hbitter/DNMS/Firmware/Teensy/Teensy3.6/V2/README.md

# [English text below](#teensy36-dnms-firmware)

## Teensy3.6 DNMS Firmware

### Versions Historie:

 - DNMS_V2.5.0 - Korrektur Fehler bei der Initialisierung
 - DNMS_V2.5.1 - Korrektur Fehler bei der Initialisierung<br><br>

------------------------------------------------------------------------
## Teensy3.6 DNMS Firmware

### Version history:

 - DNMS_V2.5.0 - Correction of a bug at startup
 - DNMS_V2.5.1 - Correction of a bug at startup<br><br>
