hbitter/DNMS/Firmware/Teensy/Teensy4.0/V2/README.md

# [English text below](#dnms-firmware-teensy40-v2-english)

# DNMS Firmware Teensy4.0 V2

## Diese Versionen berechnen LAeq, LAmin und LAmax

### aktuelle Versionen:

- DNMS_V2.4.4 - ohne USB-Audio Ausgabe
- DNMS_V2.4.5 - mit USB-Audio Ausgabe

------------------------------------------------------------------------

# DNMS Firmware Teensy4.0 V2 English

## This version calculates LAeq, LAmin and LAmax

### current versions:

- DNMS_V2.4.4 - without USB-Audio output
- DNMS_V2.4.5 - with USB-Audio output
