hbitter/DNMS/Firmware/Teensy4.0/DNMS_Vt.0.4/images/Image 1.jpg

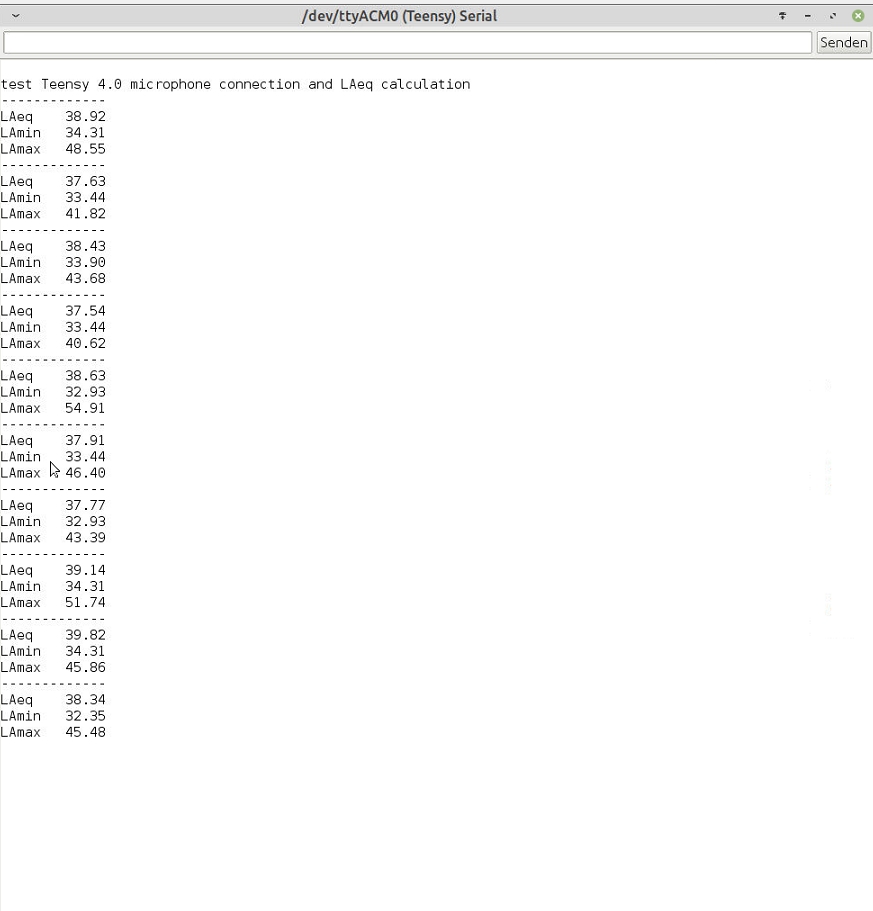
Firmware/Teensy4.0/DNMS_Vt.0.4/images/Image 1.jpg
