hbitter/DNMS/Firmware/Teensy/Teensy3.6/images/Arduino IDE Teensy3.6 USB.jpg

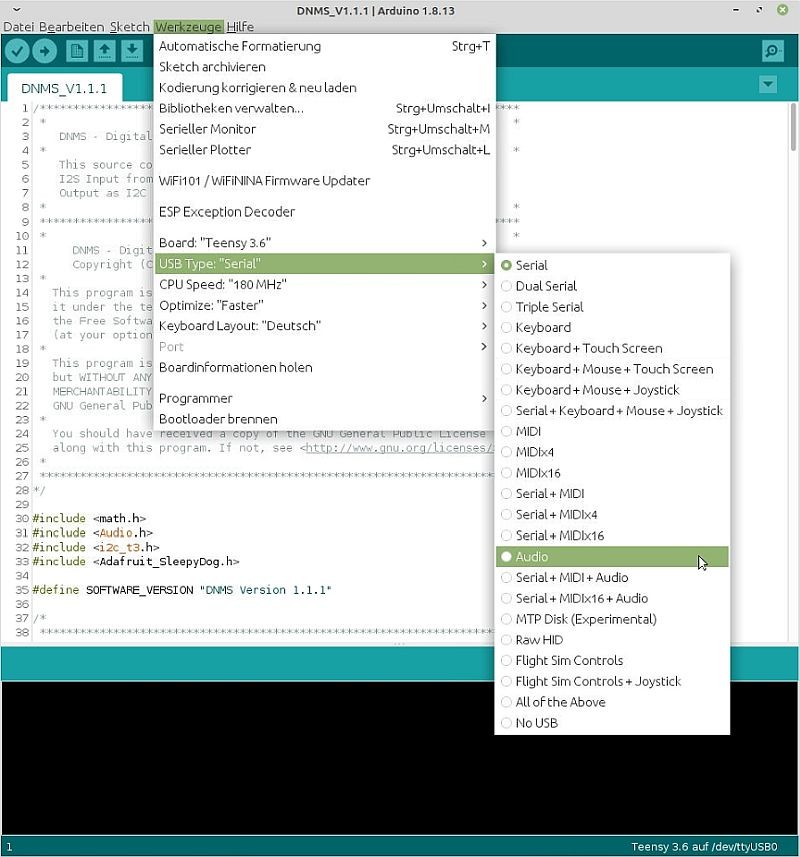
Firmware/Teensy/Teensy3.6/images/Arduino IDE Teensy3.6 USB.jpg
