hbitter/DNMS/PCBs/Airrohr PCB/Airrohr PCB V1.2 KiCad/Airrohr PCB V1.2 Bild 1.jpg

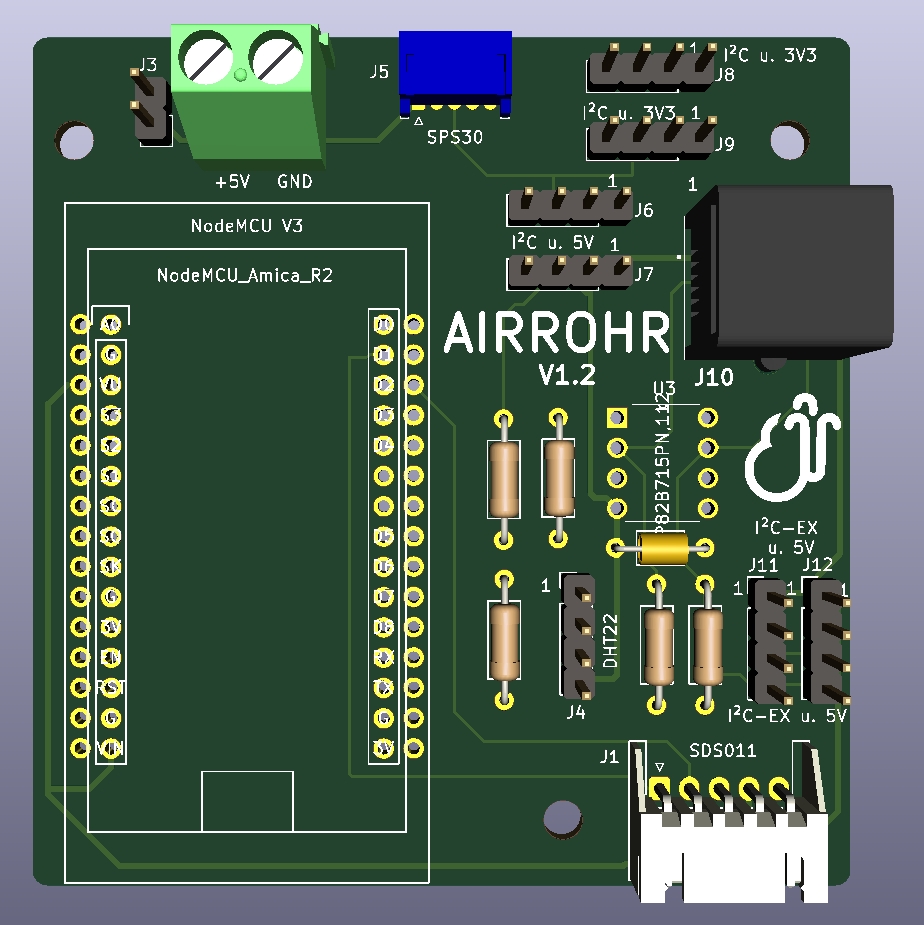
PCBs/Airrohr PCB/Airrohr PCB V1.2 KiCad/Airrohr PCB V1.2 Bild 1.jpg
