hbitter/DNMS/PCBs/Airrohr PCB/Airrohr PCB V1.2 KiCad/Airrohr PCB V1.2 Schaltplan.jpg

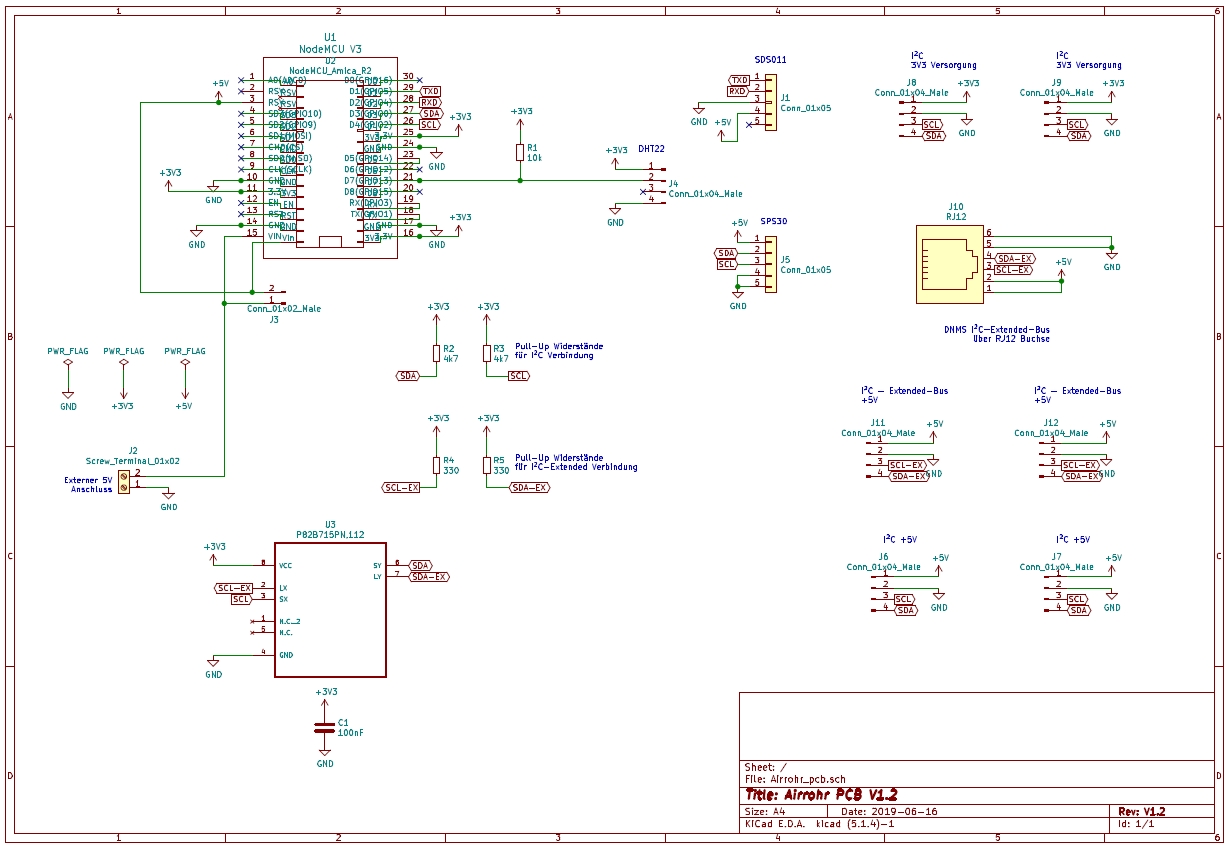
PCBs/Airrohr PCB/Airrohr PCB V1.2 KiCad/Airrohr PCB V1.2 Schaltplan.jpg
