hbitter/DNMS/PCBs/Airrohr-PCB/Airrohr-PCB-V1.6/Bild1.png

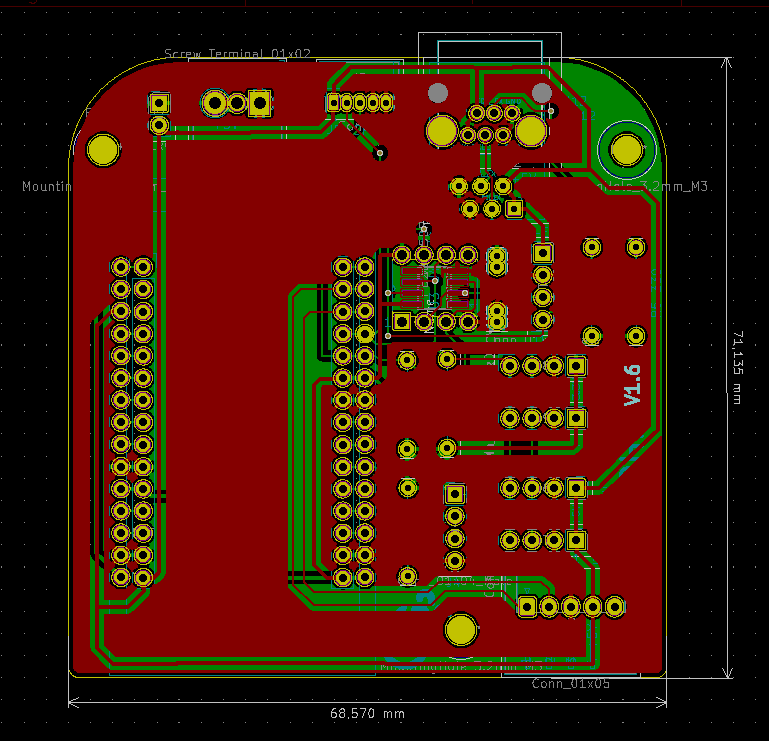
PCBs/Airrohr-PCB/Airrohr-PCB-V1.6/Bild1.png
