hbitter/DNMS/PCBs/Airrohr-PCB/Airrohr-PCB-V1.6/Bild2.png

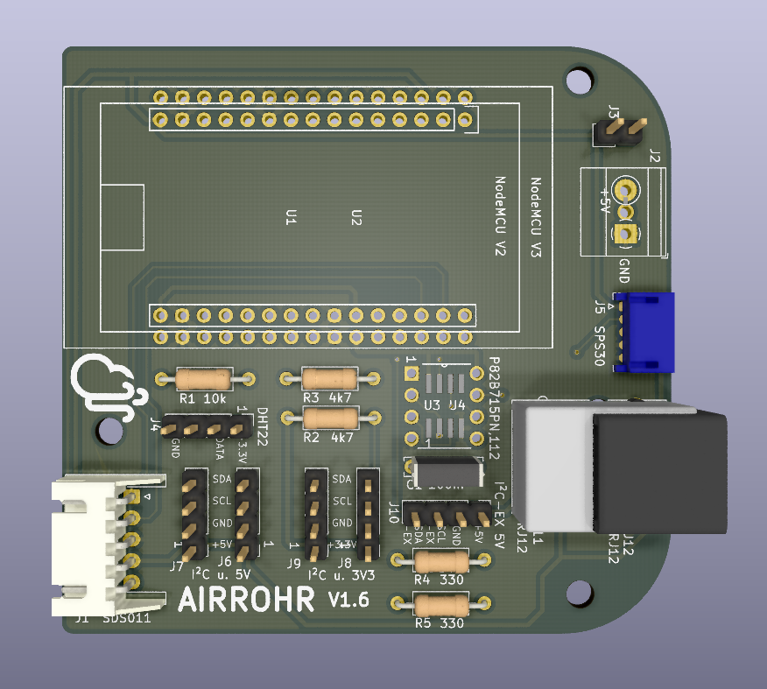
PCBs/Airrohr-PCB/Airrohr-PCB-V1.6/Bild2.png
