hbitter/DNMS/PCBs/Airrohr-PCB/Airrohr-PCB-V1.6/Bild3.png

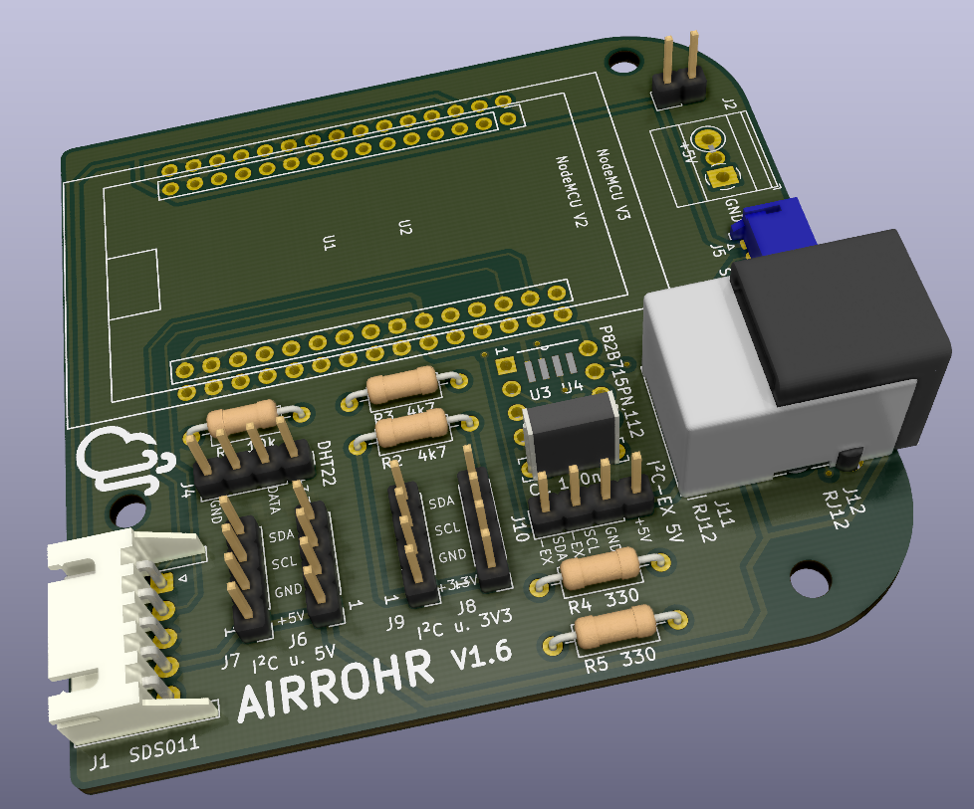
PCBs/Airrohr-PCB/Airrohr-PCB-V1.6/Bild3.png
