hbitter/DNMS/PCBs/DNMS - T3.6/DNMS - T3.6 V1.1/Ansicht PCB 1.jpg

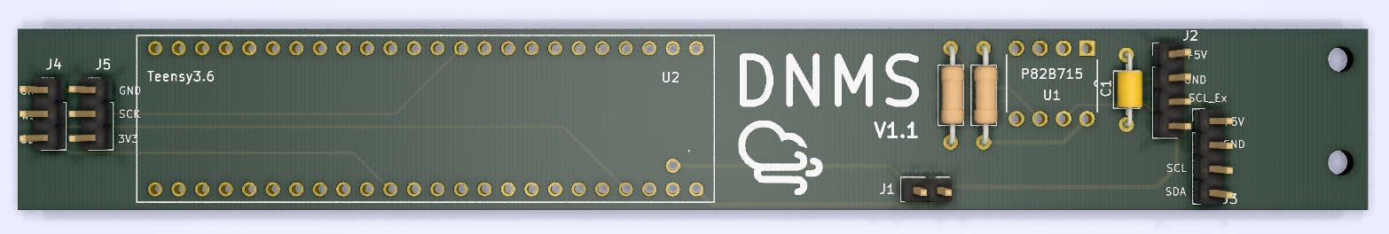
PCBs/DNMS - T3.6/DNMS - T3.6 V1.1/Ansicht PCB 1.jpg
