hbitter/DNMS/PCBs/DNMS - T3.6/DNMS - T3.6 V1.1/Ansicht PCB 2.jpg

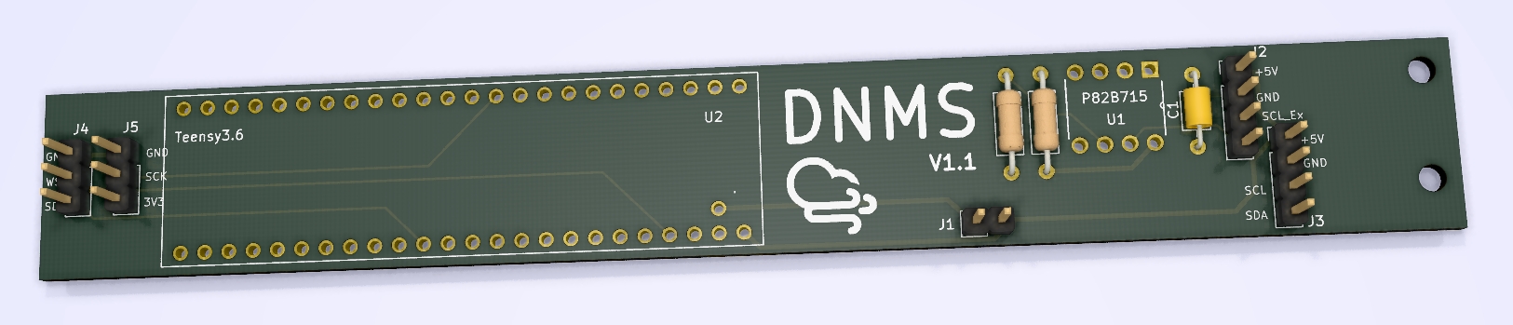
PCBs/DNMS - T3.6/DNMS - T3.6 V1.1/Ansicht PCB 2.jpg
