hbitter/DNMS/PCBs/DNMS - T3.6/DNMS-T3.6-V1.2/DNMS - T3.6 V1.2 Bild 2.jpg

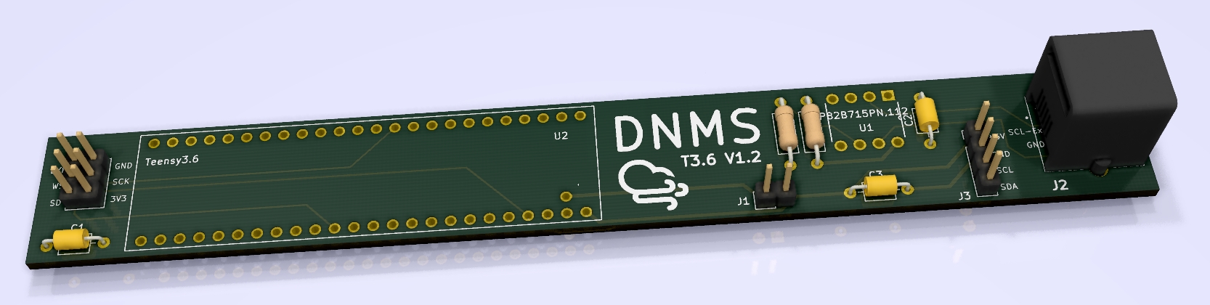
PCBs/DNMS - T3.6/DNMS-T3.6-V1.2/DNMS - T3.6 V1.2 Bild 2.jpg
