hbitter/DNMS/PCBs/DNMS - T4+NodeMCU/DNMS - T4+NodeMCU V1.2/DNMS - T4+NodeMCU V1.2 back 2.jpg

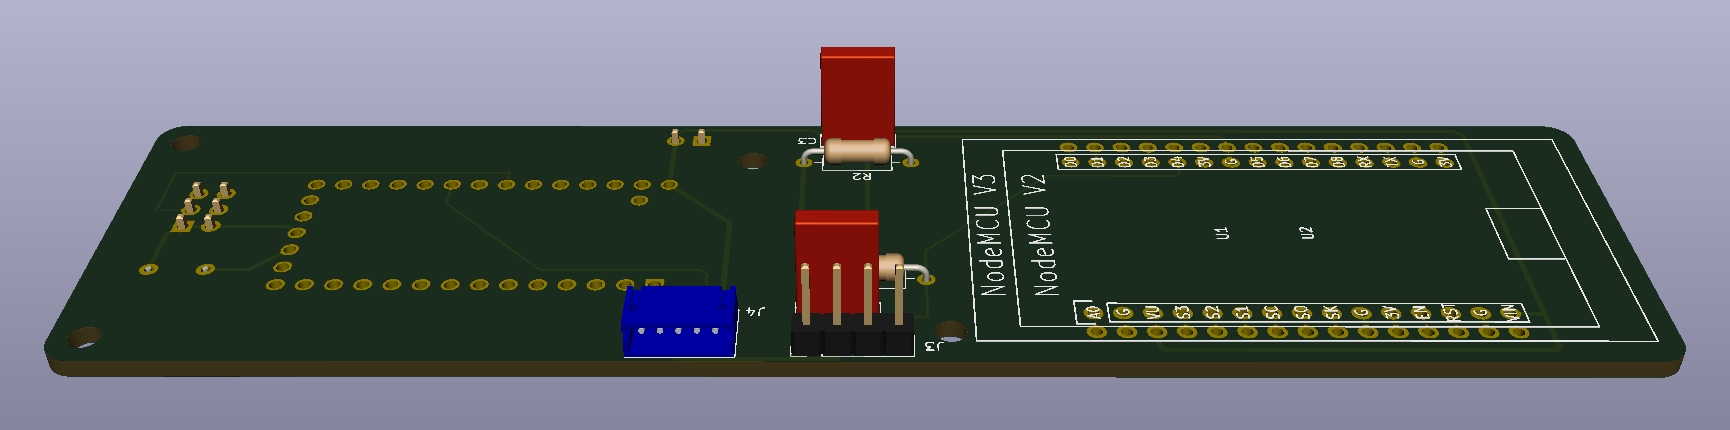
PCBs/DNMS - T4+NodeMCU/DNMS - T4+NodeMCU V1.2/DNMS - T4+NodeMCU V1.2 back 2.jpg
