hbitter/DNMS/PCBs/DNMS - T4/DNMS - T4 V1.2/DNMS - T4 V1.2 Bild 2.jpg

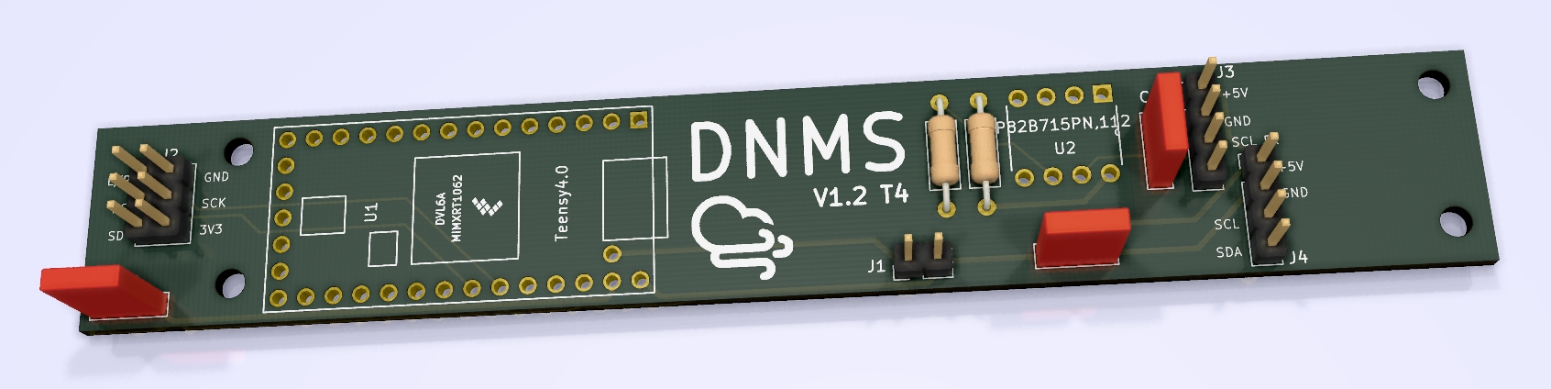
PCBs/DNMS - T4/DNMS - T4 V1.2/DNMS - T4 V1.2 Bild 2.jpg
