hbitter/DNMS/PCBs/DNMS - T4/DNMS - T4 V1.2/DNMS - T4 V1.2 Schaltplan.jpg

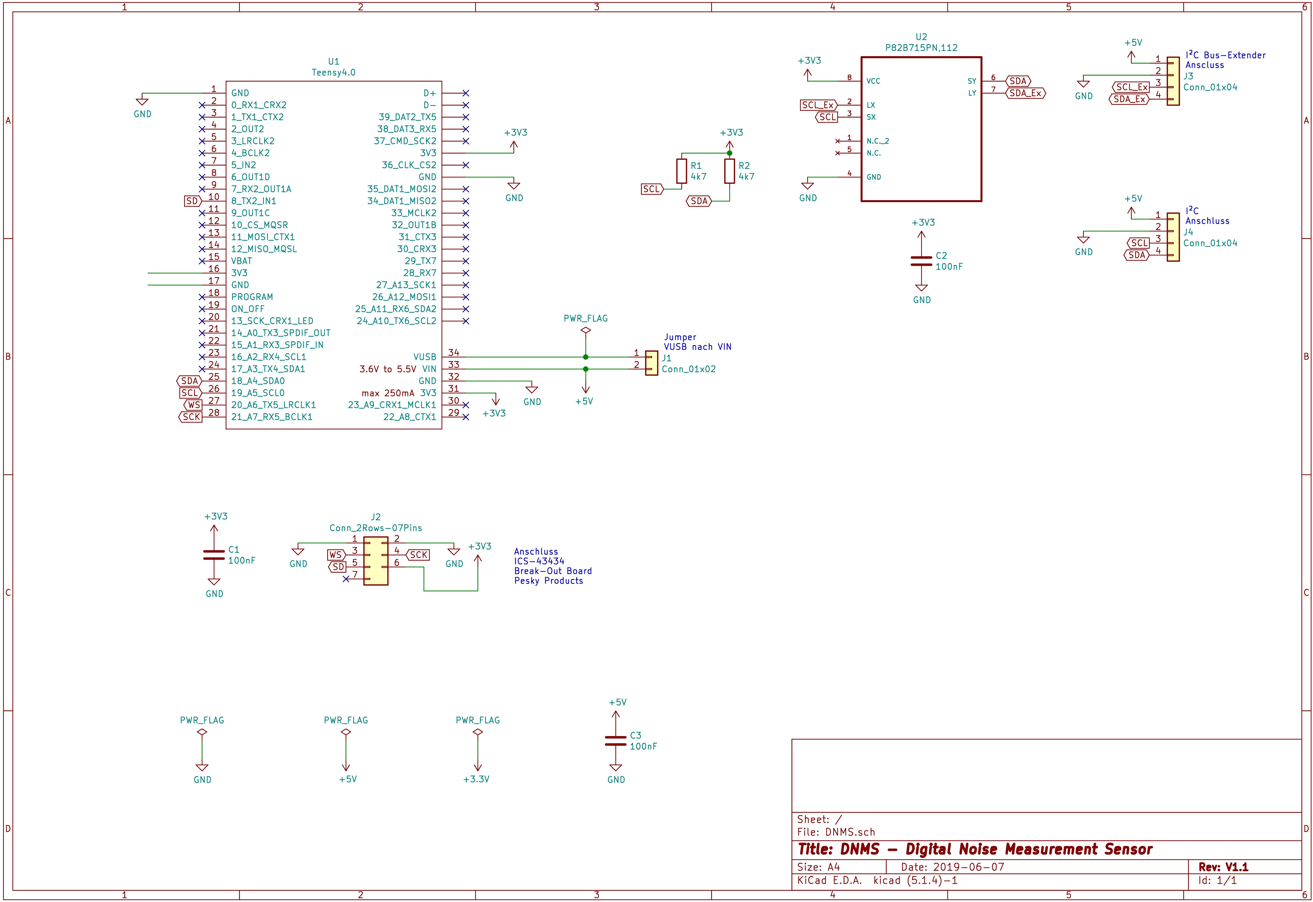
PCBs/DNMS - T4/DNMS - T4 V1.2/DNMS - T4 V1.2 Schaltplan.jpg
