hbitter/DNMS/PCBs/DNMS-RPI-HAT/DNMS-RPI-HAT-V1.0/Bild 1.png

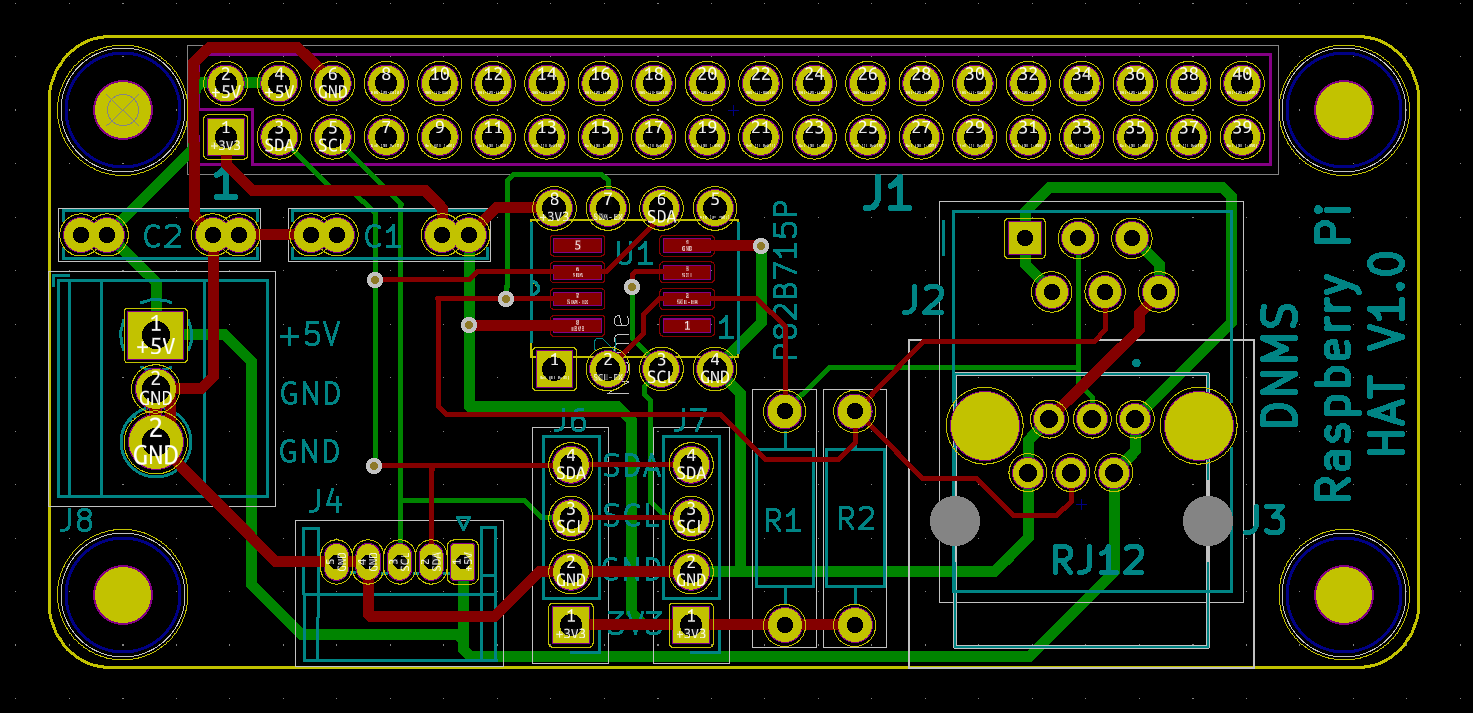
PCBs/DNMS-RPI-HAT/DNMS-RPI-HAT-V1.0/Bild 1.png
