hbitter/DNMS/PCBs/DNMS-RPI-HAT/DNMS-RPI-HAT-V1.0/Bild 4.png

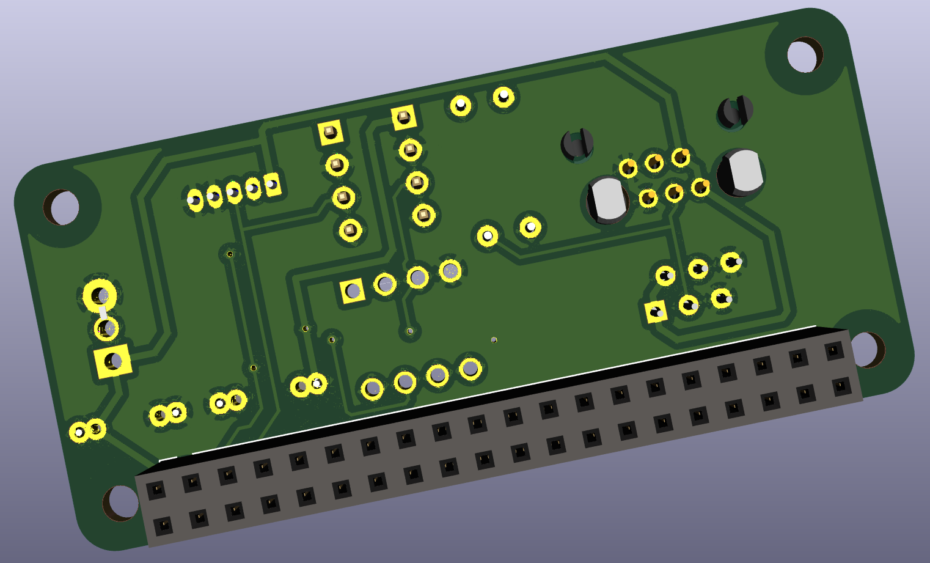
PCBs/DNMS-RPI-HAT/DNMS-RPI-HAT-V1.0/Bild 4.png
