hbitter/DNMS/PCBs/DNMS-RPI-HAT/images/DNMS-RPI-HAT-V1.0 Bild2.jpg

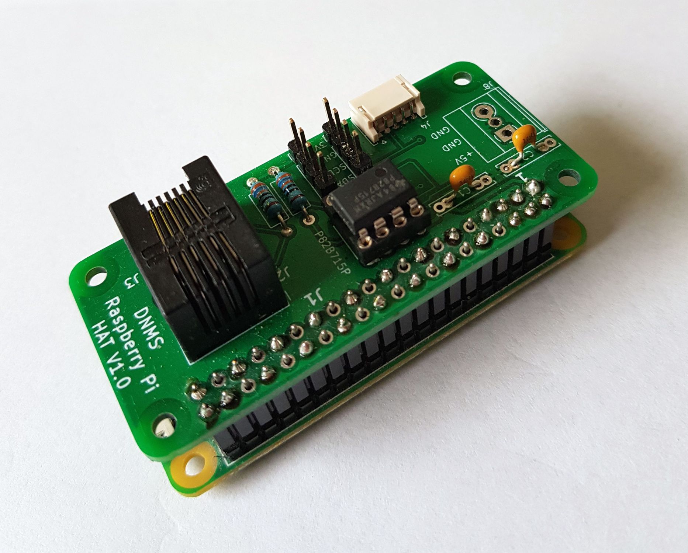
PCBs/DNMS-RPI-HAT/images/DNMS-RPI-HAT-V1.0 Bild2.jpg
