hbitter/DNMS/PCBs/DNMS-T3.6+NodeMCU/DNMS-T3.6+NodeMCUV1.0/T3.6+NodeMCU-V1.0-Bild-4.jpg

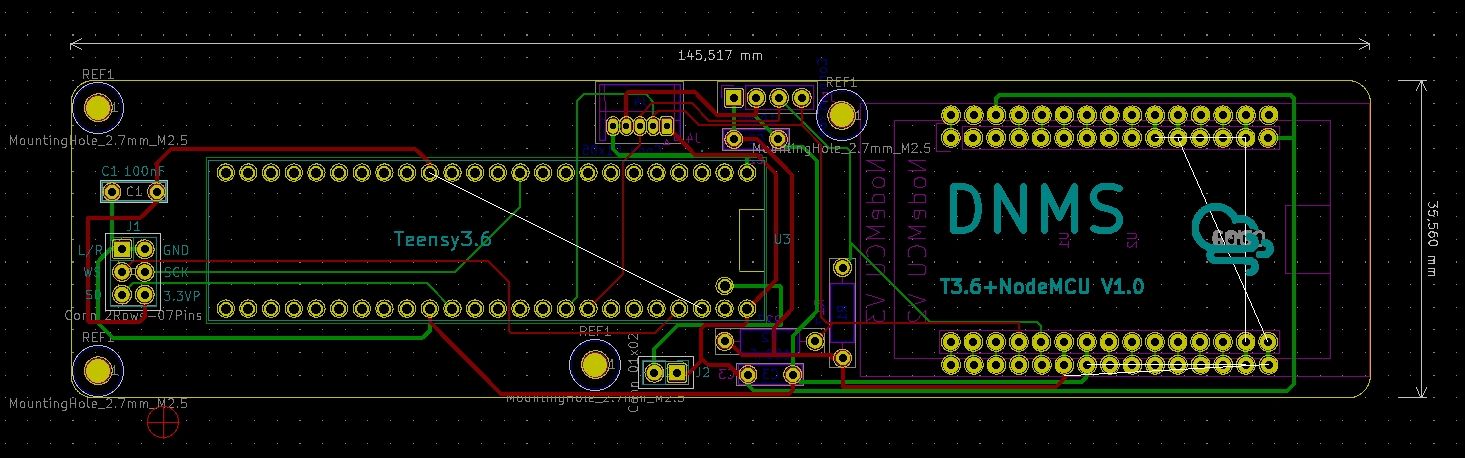
PCBs/DNMS-T3.6+NodeMCU/DNMS-T3.6+NodeMCUV1.0/T3.6+NodeMCU-V1.0-Bild-4.jpg
