hbitter/DNMS/PCBs/DNMS-T3.6/DNMS-T3.6-V1.4/Bild2.jpg

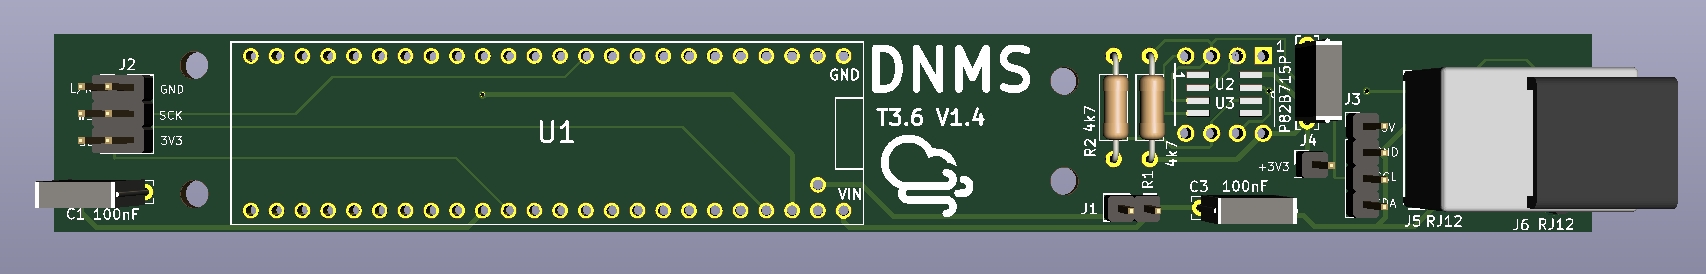
PCBs/DNMS-T3.6/DNMS-T3.6-V1.4/Bild2.jpg
