hbitter/DNMS/PCBs/DNMS-T4.0+NodeMCU/DNMS-T4.0+NodeMCU-V1.5/Bild5.png

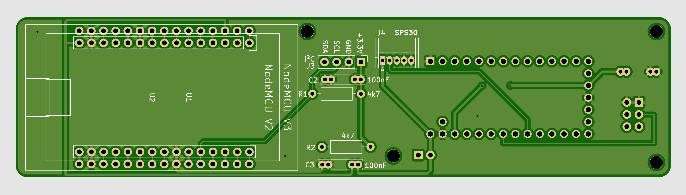
PCBs/DNMS-T4.0+NodeMCU/DNMS-T4.0+NodeMCU-V1.5/Bild5.png
