hbitter/DNMS/PCBs/DNMS-T4.0/DNMS-T4.0-V1.7/Bild4.png

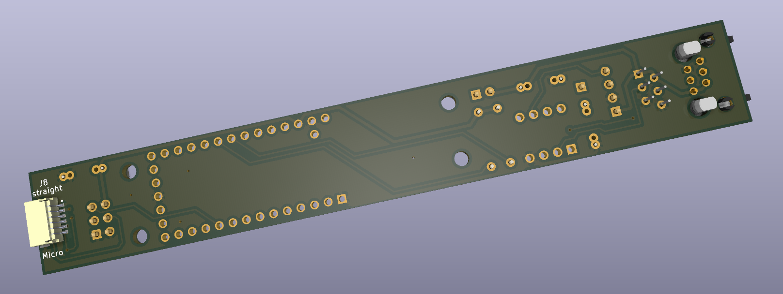
PCBs/DNMS-T4.0/DNMS-T4.0-V1.7/Bild4.png
