hbitter/DNMS/PCBs/DNMS-T4.0/DNMS-T4.0-V1.7/Teensy_Mikro_reverse.jpg

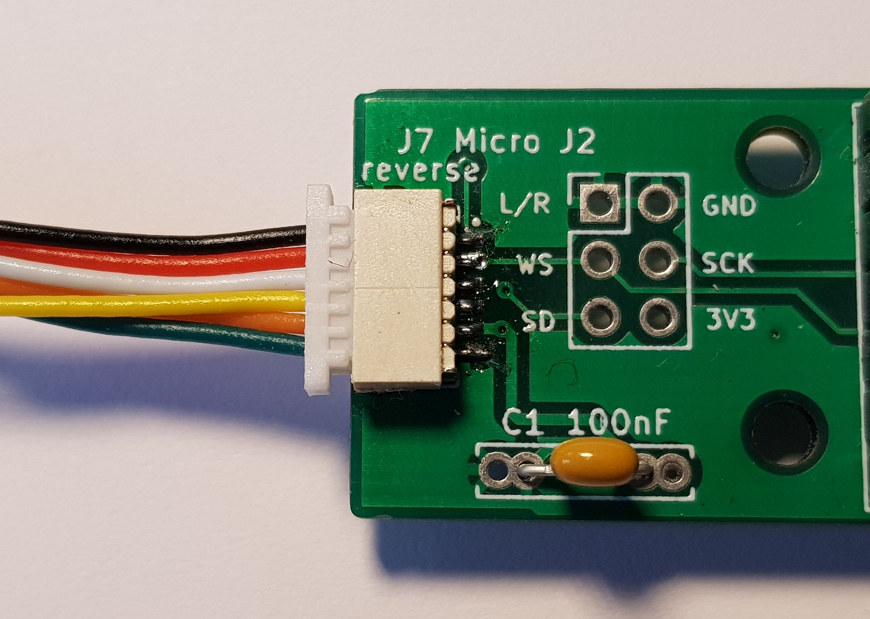
PCBs/DNMS-T4.0/DNMS-T4.0-V1.7/Teensy_Mikro_reverse.jpg
