hbitter/DNMS/PCBs/DNMS-T4.0/DNMS-T4.0-V1.8S/Aisler zugewiesene Bauteile 2026-04-07_18-02.png

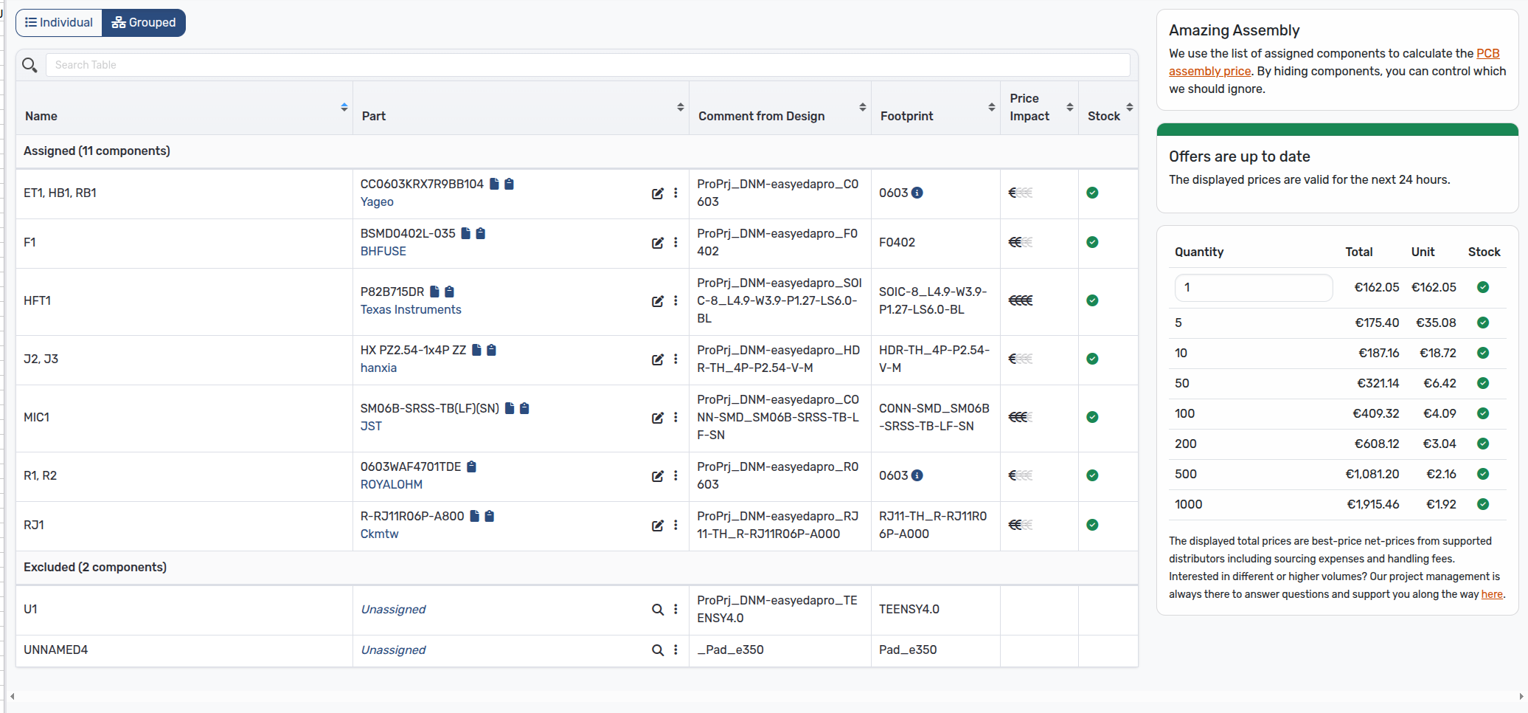
PCBs/DNMS-T4.0/DNMS-T4.0-V1.8S/Aisler zugewiesene Bauteile 2026-04-07_18-02.png
