hbitter/DNMS/PCBs/DNMS-T4.0/DNMS-T4.0-V1.8S/picture1.png

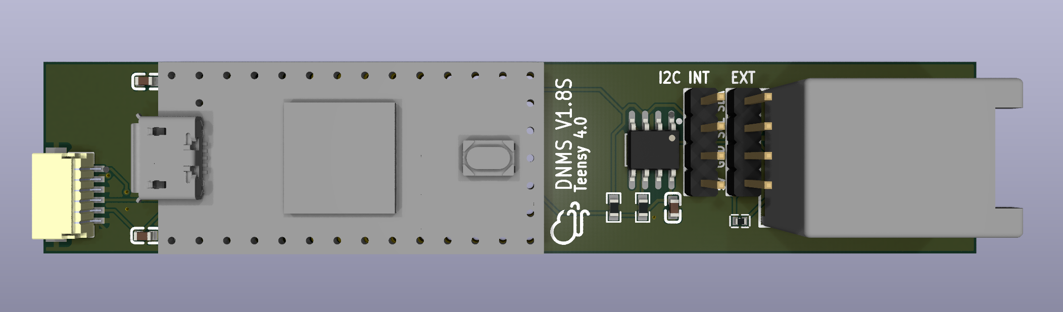
PCBs/DNMS-T4.0/DNMS-T4.0-V1.8S/picture1.png
