hbitter/DNMS/PCBs/DNMS-T4.0/DNMS-T4.0-V1.8S/ProPrj_DNMS_TEENSY_2025-10-10.png

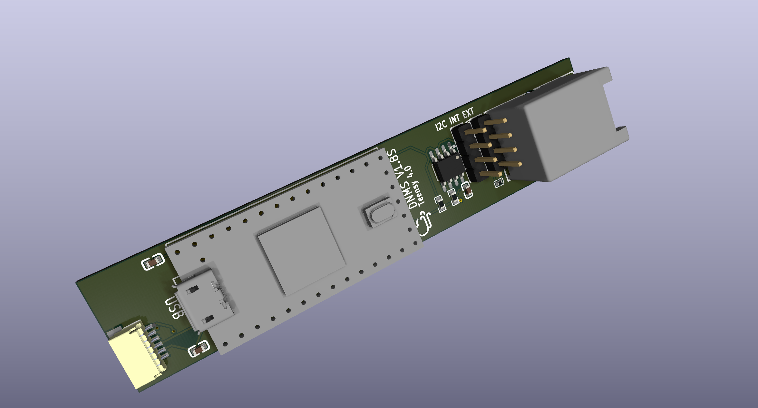
PCBs/DNMS-T4.0/DNMS-T4.0-V1.8S/ProPrj_DNMS_TEENSY_2025-10-10.png
