hbitter/DNMS/PCBs/ICS-43434 microphone PCB/ICS-43434-PCB-V1.4/Bild1.png

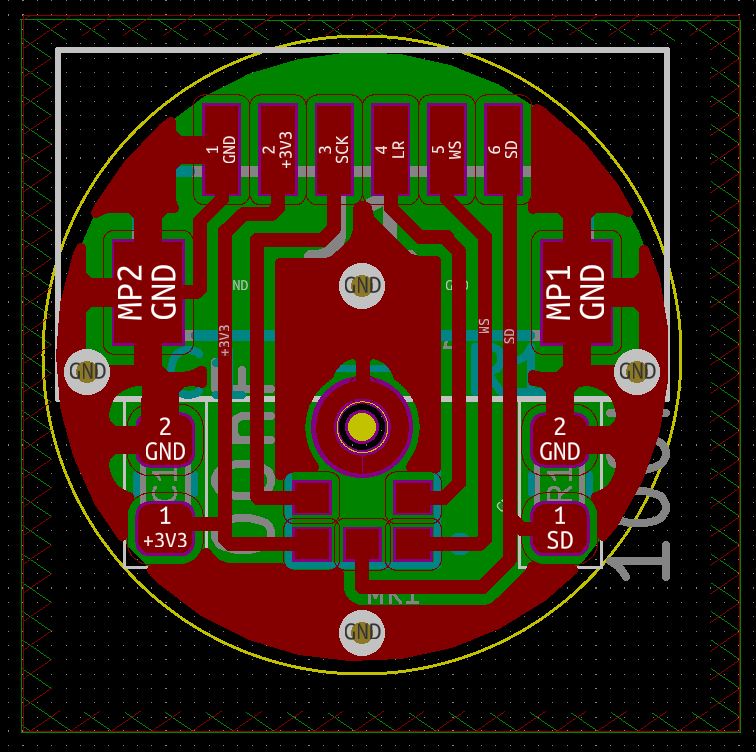
PCBs/ICS-43434 microphone PCB/ICS-43434-PCB-V1.4/Bild1.png
