hbitter/DNMS/PCBs/ICS-43434 microphone PCB/ICS-43434-PCB-V1.4/Bild4.png

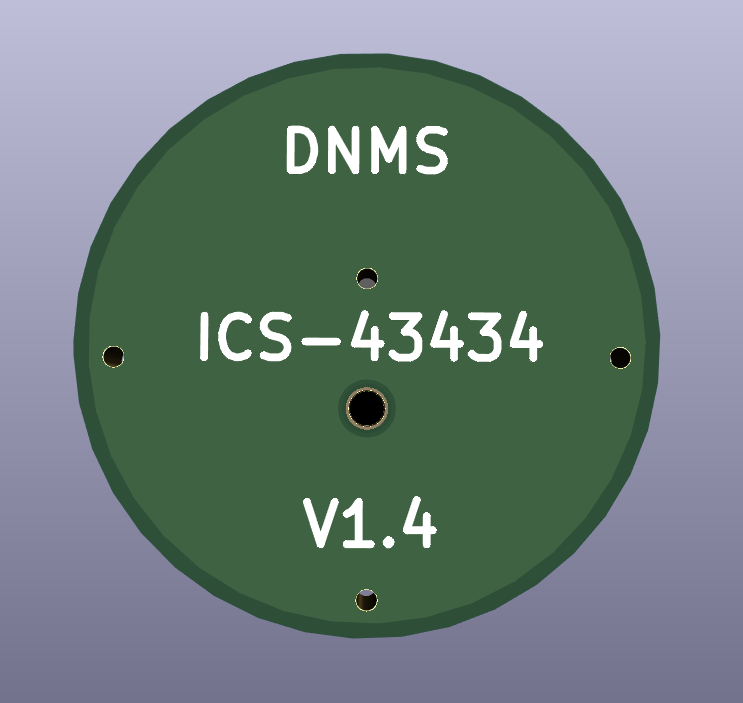
PCBs/ICS-43434 microphone PCB/ICS-43434-PCB-V1.4/Bild4.png
