hbitter/DNMS/PCBs/IM72D128 microphone PCB/IM72D128-PCB-V1.0/Bild1.png

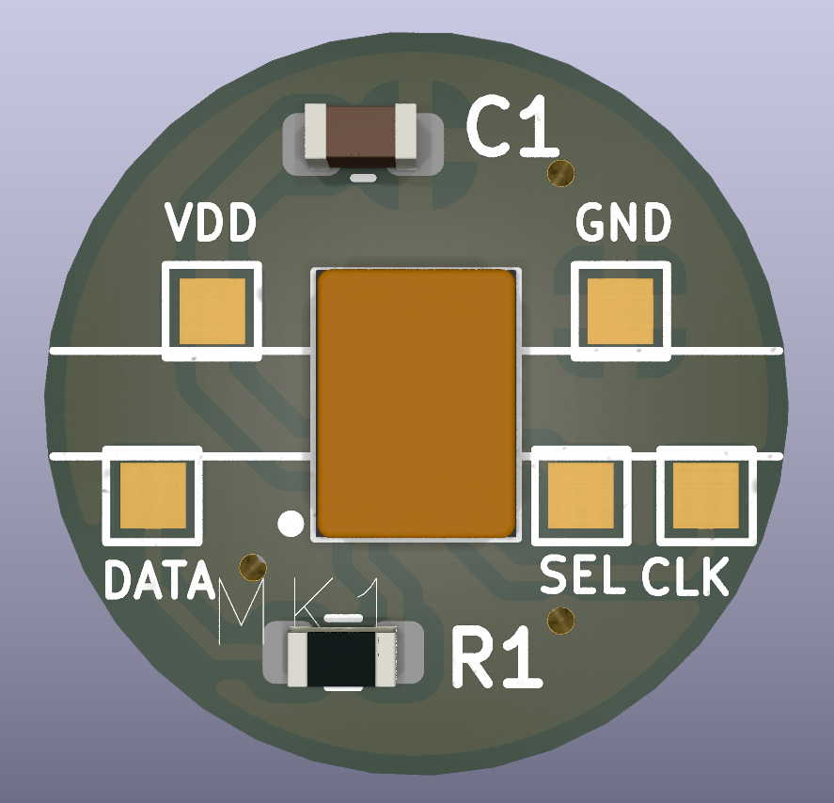
PCBs/IM72D128 microphone PCB/IM72D128-PCB-V1.0/Bild1.png
