hbitter/DNMS/PCBs/IM72D128 microphone PCB/IM72D128-Tube-PCB-V1.0/Bild5.png

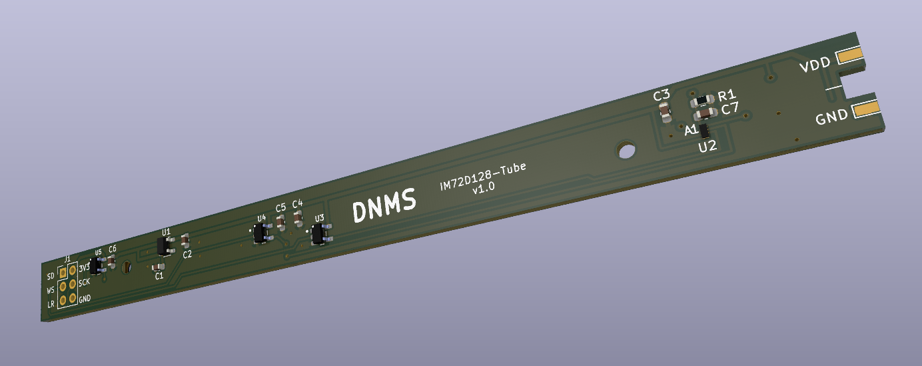
PCBs/IM72D128 microphone PCB/IM72D128-Tube-PCB-V1.0/Bild5.png
