hbitter/DNMS/PCBs/images/Airrohr-ESP32-V1.0.jpg

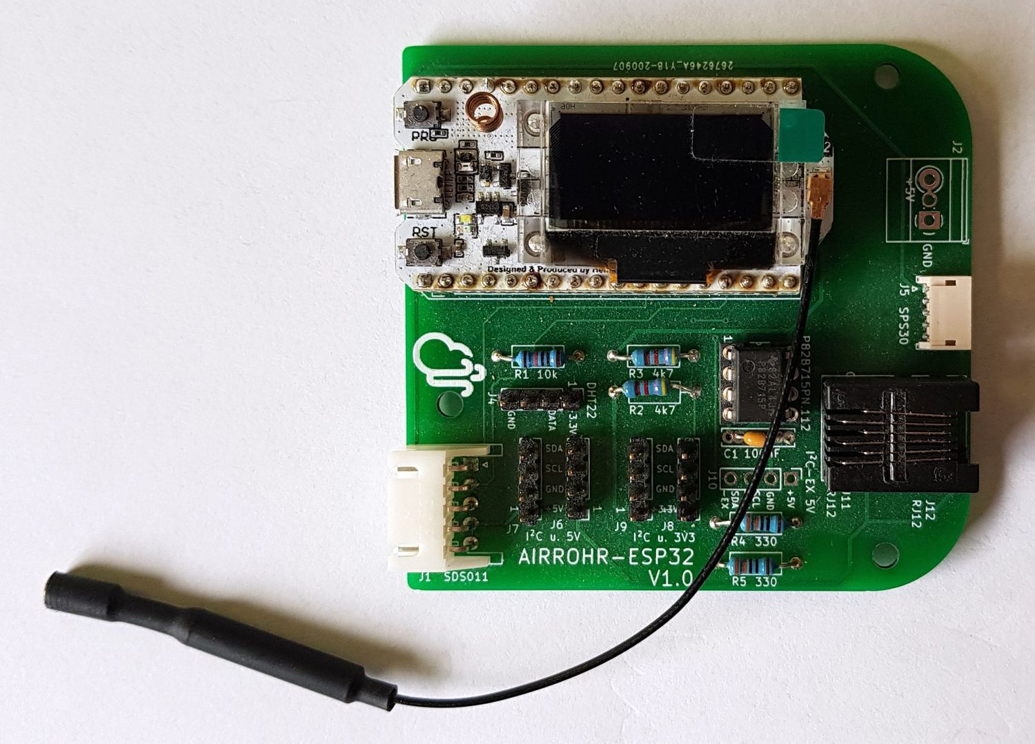
PCBs/images/Airrohr-ESP32-V1.0.jpg
