hbitter/DNMS/web-flash-esp8266-de/noise.webp

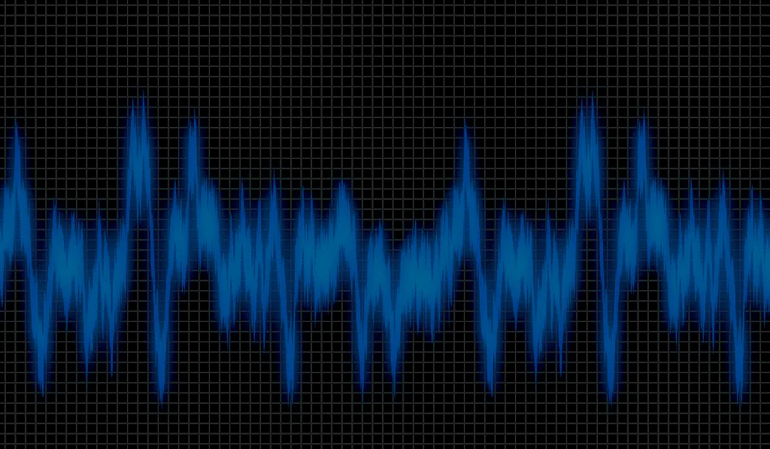
web-flash-esp8266-de/noise.webp
