hbitter/DNMS/PCBs/ICS-43434 microphone PCB/ICS-43434-PCB-V1.4/10sets-ICS-43434-PCB-V1.4-BOM.xls

PCBWay Bom Quotation , Product No.:
Item # | *Designator | *Qty | Manufacturer | *Mfg Part # | Description / Value | *Package/Footprint | Mounting Type | Your Instructions / Notes | *Unit Price(10 sets) | *Total | *Delivery Time | *PCBWay Note | PCBWay Update
1 | R1 | 1 | Yageo | RC0603JR-07100KL | RES SMD 100K OHM 5% 1/10W 0603 | 0603 | SMT | any other Manufacturer is ok |  | $0.000
2 | MK1 | 1 | TDK InvenSense | ICS-43434 | MEMS Microphone | 6-Terminal LGA_CAV | SMT | Link to Datasheet: https://invensense.tdk.com/products/ics-43434/ |  | $0.000
3 | C1 | 1 | KEMET | C0603C104M4RAC7411 | CAP CER 0.1UF 16V X7R 0603 | 0603 | SMT | any other Manufacturer is ok |  | $0.000
4 | J1 | 1 | JST | BM06B-SRSS-TB(LF)(SN) | JST SH Series 6-pin connector |  | SMT | any other Manufacturer is ok |  | $0.000
 |  |  |  |  |  |  |  |  | All Total | $0.000
