hbitter/DNMS/Test Ergebnisse - test results/ICS-43434 DNMS_V5.2.4 26.01.2024.xlsx

Sheet: Teil1
ICS-43434 Vergleich von vier Watterott Prototyp Mikrofonen
Datum der Test: 26.01.2024
Ort: HFT, Stuttgart im Halbfreifeldraum
DNMS Firmware Version: DNMS_V5.2.4
Referenzsystem zum Vergleich: XL2 Analysator von NTI Audio mit Bauartzulassung und Klasse 1 Mikrofon
Folgende Bezeichung und Zuordnung:
XL2 Referenzsystem von NTI Audio
M1 bit 1,8V Versorgungsspannung
M2 bit 3,3V Versorgungsspannung
M3 HFT 1,8V Versorgungsspannung
M4 HFT 3,3V Versorgungsspannung
Messungen:
1.1 Klasse 1 Kalibrator 114 dB Einzahlwerte
 | LZ | LA
XL2 | 114.0 | 114.0
M1 | 113.9 | 113.9
M2 | 114.1 | 114.1
M3 | 114.0 | 114.0
M4 | 113.6 | 113.6
1.2. Kalibrator Terzen Z-Werte über 1 s
Hz | 20 | 31,5 | 40 | 40 | 50 | 63 | 80 | 100 | 125 | 160 | 200 | 250 | 315 | 400 | 500 | 630 | 800 | 1000 | 1250 | 1600 | 2000 | 2500 | 3150 | 4000 | 5000 | 6300 | 8000 | 10000 | 12500 | 16000 | 20000
XL2
M1 | 38.0 | 39.1 | 42.0 | 33.6 | 33.0 | 28.7 | 26.8 | 26.8 | 26.0 | 26.8 | 28.6 | 28.0 | 31.4 | 34.7 | 38.6 | 41.2 | 43.4 | 114.0 | 42.6 | 19.5 | 68.5 | 17.4 | 62.6 | 47.6 | 48.5 | 52.6 | 43.0 | 46.9 | 42.6 | 36.4 | 31.8
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
