hbitter/DNMS/Test Ergebnisse - test results/IM72D128 DNMS_V5.2.6 26.01.2024.xlsx

Sheet: Teil1
IM72D128 Vergleich von drei Watterott Prototyp Mikrofonen und einem selbst gefertigtem Mikrofon
Datum der Test: 26.01.2024
Ort: HFT, Stuttgart im Halbfreifeldraum
DNMS Firmware Version: DNMS_V5.2.6
Referenzsystem zum Vergleich: XL2 Analysator von NTI Audio mit Bauartzulassung und Klasse 1 Mikrofon
Folgende Bezeichung und Zuordnung:
XL2 Referenzsystem von NTI Audio
M1 bit 1,8V Versorgungsspannung
M2 bit 3,3V Versorgungsspannung
M3 selbst gefertigt 1,8V Versorgungsspannung
M4 HFT 3,3V Versorgungsspannung
Messungen:
1.1 Klasse 1 Kalibrator 114 dB Einzahlwerte
 | LZ | LA
XL2 | 114.0 | 114.0
M1 | 114.1 | 114.1
M2 | 114.4 | 114.4
M3 | 114.7 | 114.7
M4 | 114.3 | 114.4
1.2. Kalibrator Terzen Z-Werte über 1 s
Hz | 20 | 31,5 | 40 | 40 | 50 | 63 | 80 | 100 | 125 | 160 | 200 | 250 | 315 | 400 | 500 | 630 | 800 | 1000 | 1250 | 1600 | 2000 | 2500 | 3150 | 4000 | 5000 | 6300 | 8000 | 10000 | 12500 | 16000 | 20000
XL2
M1 | 39.9 | 41.4 | 34.5 | 30.8 | 30.9 | 28.9 | 23.9 | 33.0 | 34.6 | 22.3 | 27.2 | 28.6 | 30.2 | 33.4 | 35.8 | 40.3 | 44.7 | 114.0 | 16.6 | 18.4 | 51.3 | 17.9 | 64.1 | 40.1 | 47.9 | 25.3 | 19.2 | 20.8 | 16.6 | 15.0 | 7.1
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
