hbitter/DNMS/PCBs/DNMS - T3.6/DNMS - T3.6 V1.1/DNMS - T3.6 V1.1 Schaltplan.pdf

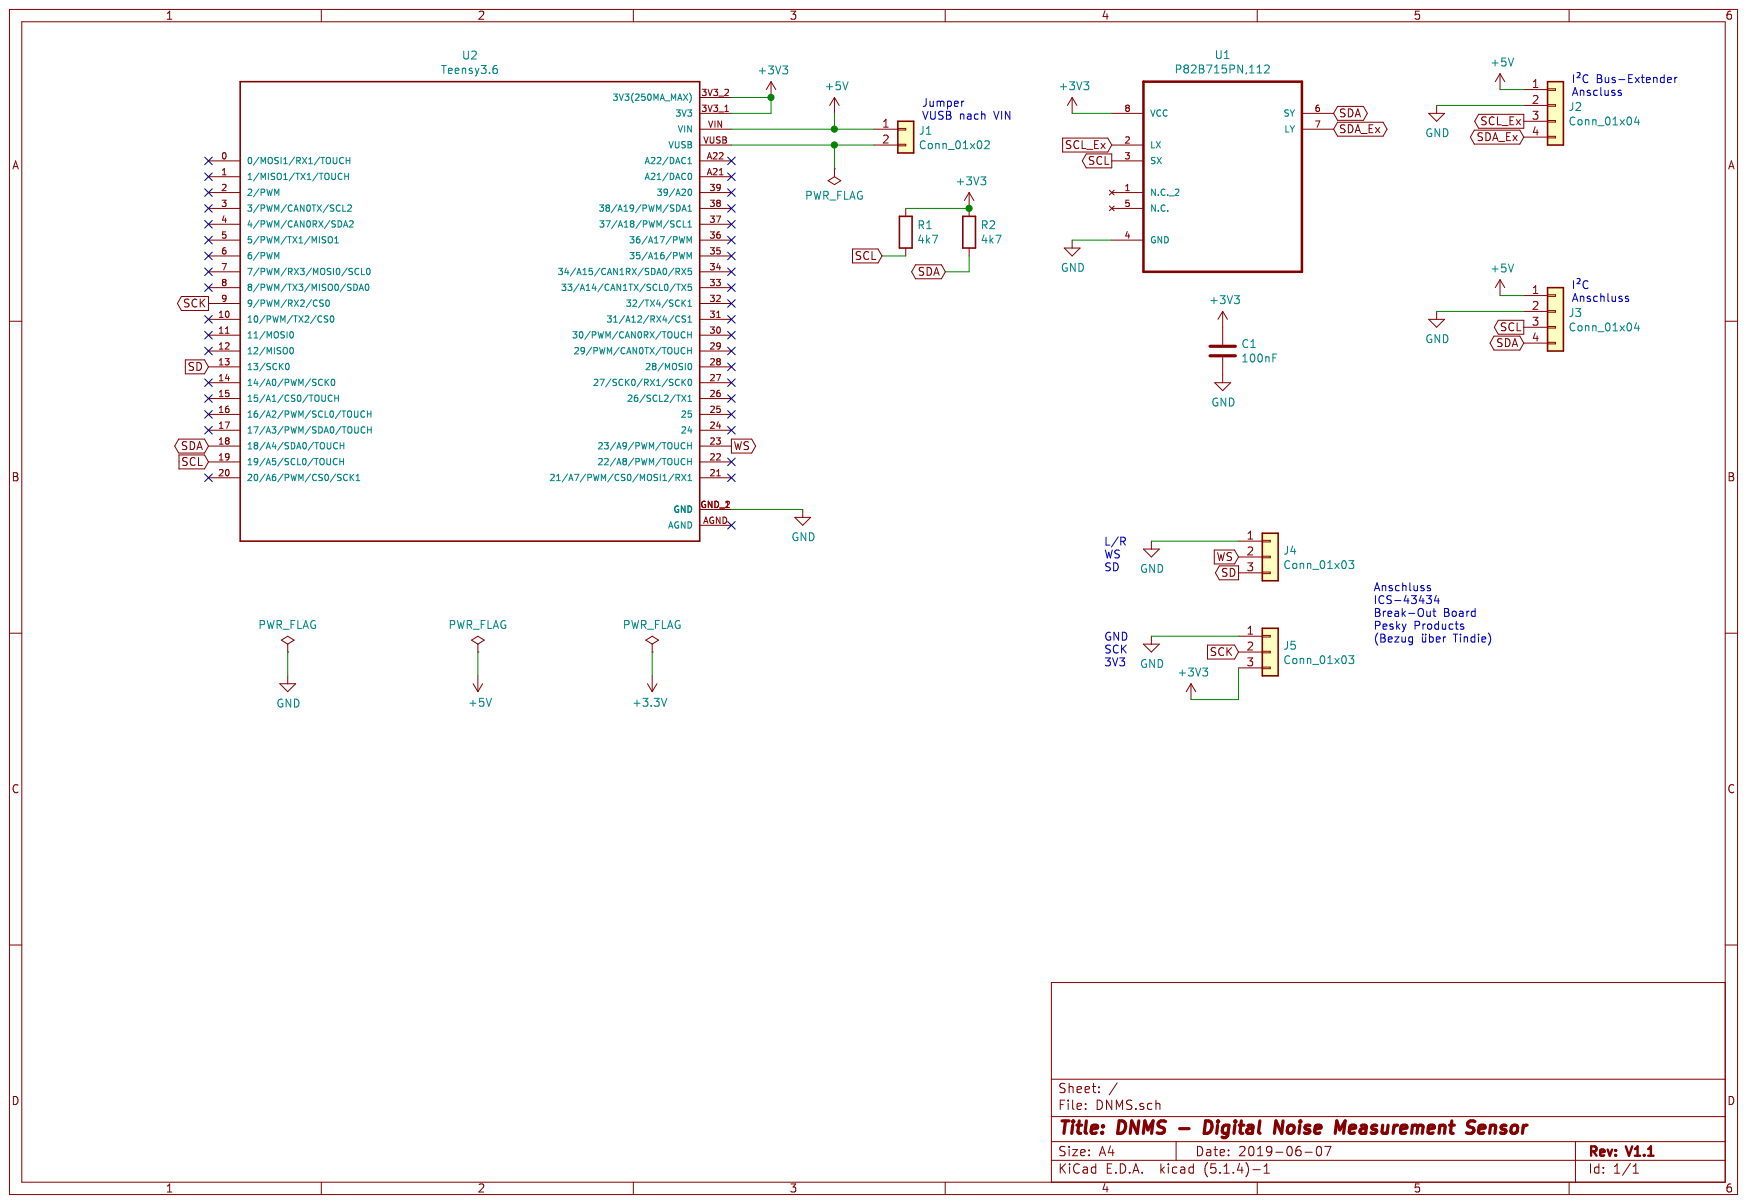
[picture p161: page 1]
