hbitter/DNMS/PCBs/DNMS - T4/DNMS - T4 V1.2/DNMS - T4 V1.2 Schaltplan.pdf

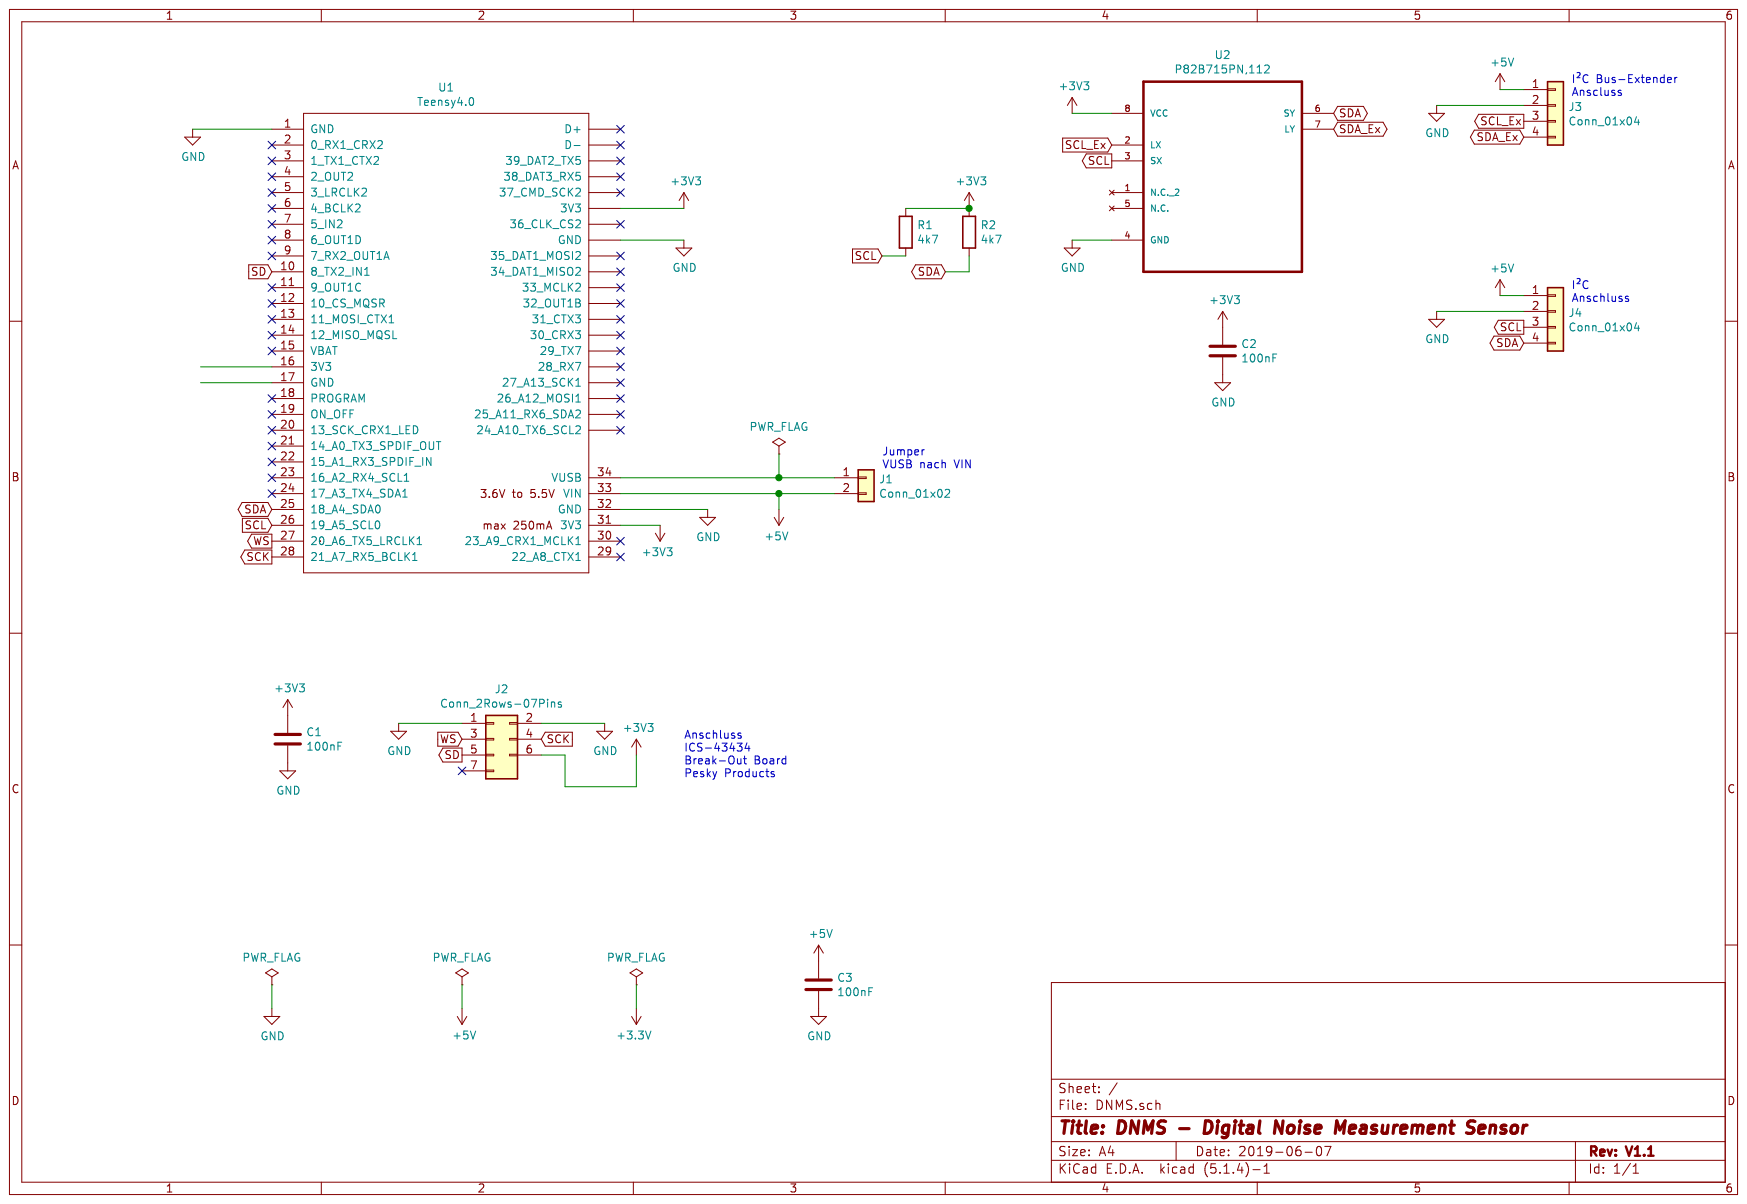
[picture p163: page 1]
