hbitter/DNMS/PCBs/DNMS-T4.0/DNMS-T4.0-V1.7/RJ-12 6P-6C Pulse/Pulse+ce553027-lc-686555.pdf

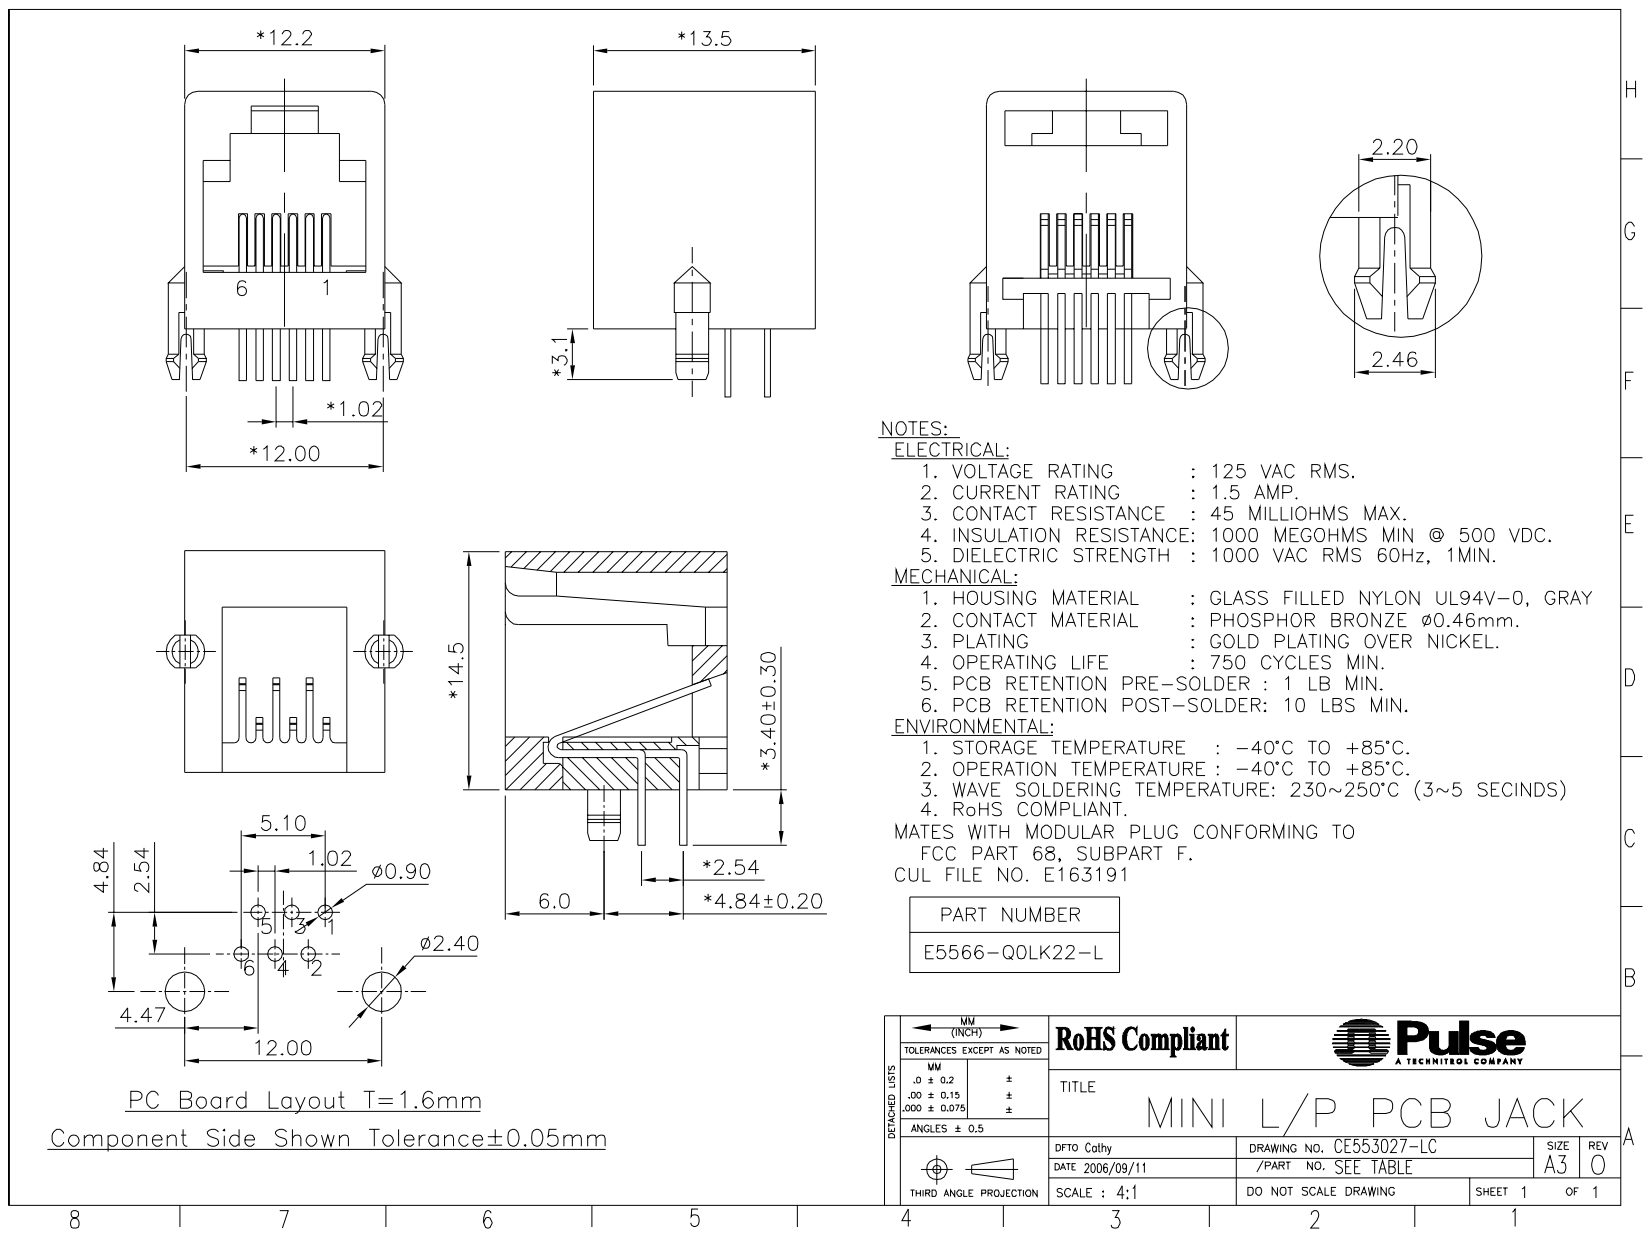
[picture p164: page 1]
