hbitter/DNMS/PCBs/DNMS-T4.0/DNMS-T4.0-V1.8S/RJ-12 6P-6C Amphenol u.a/Molex 955016669_sd drawing.pdf

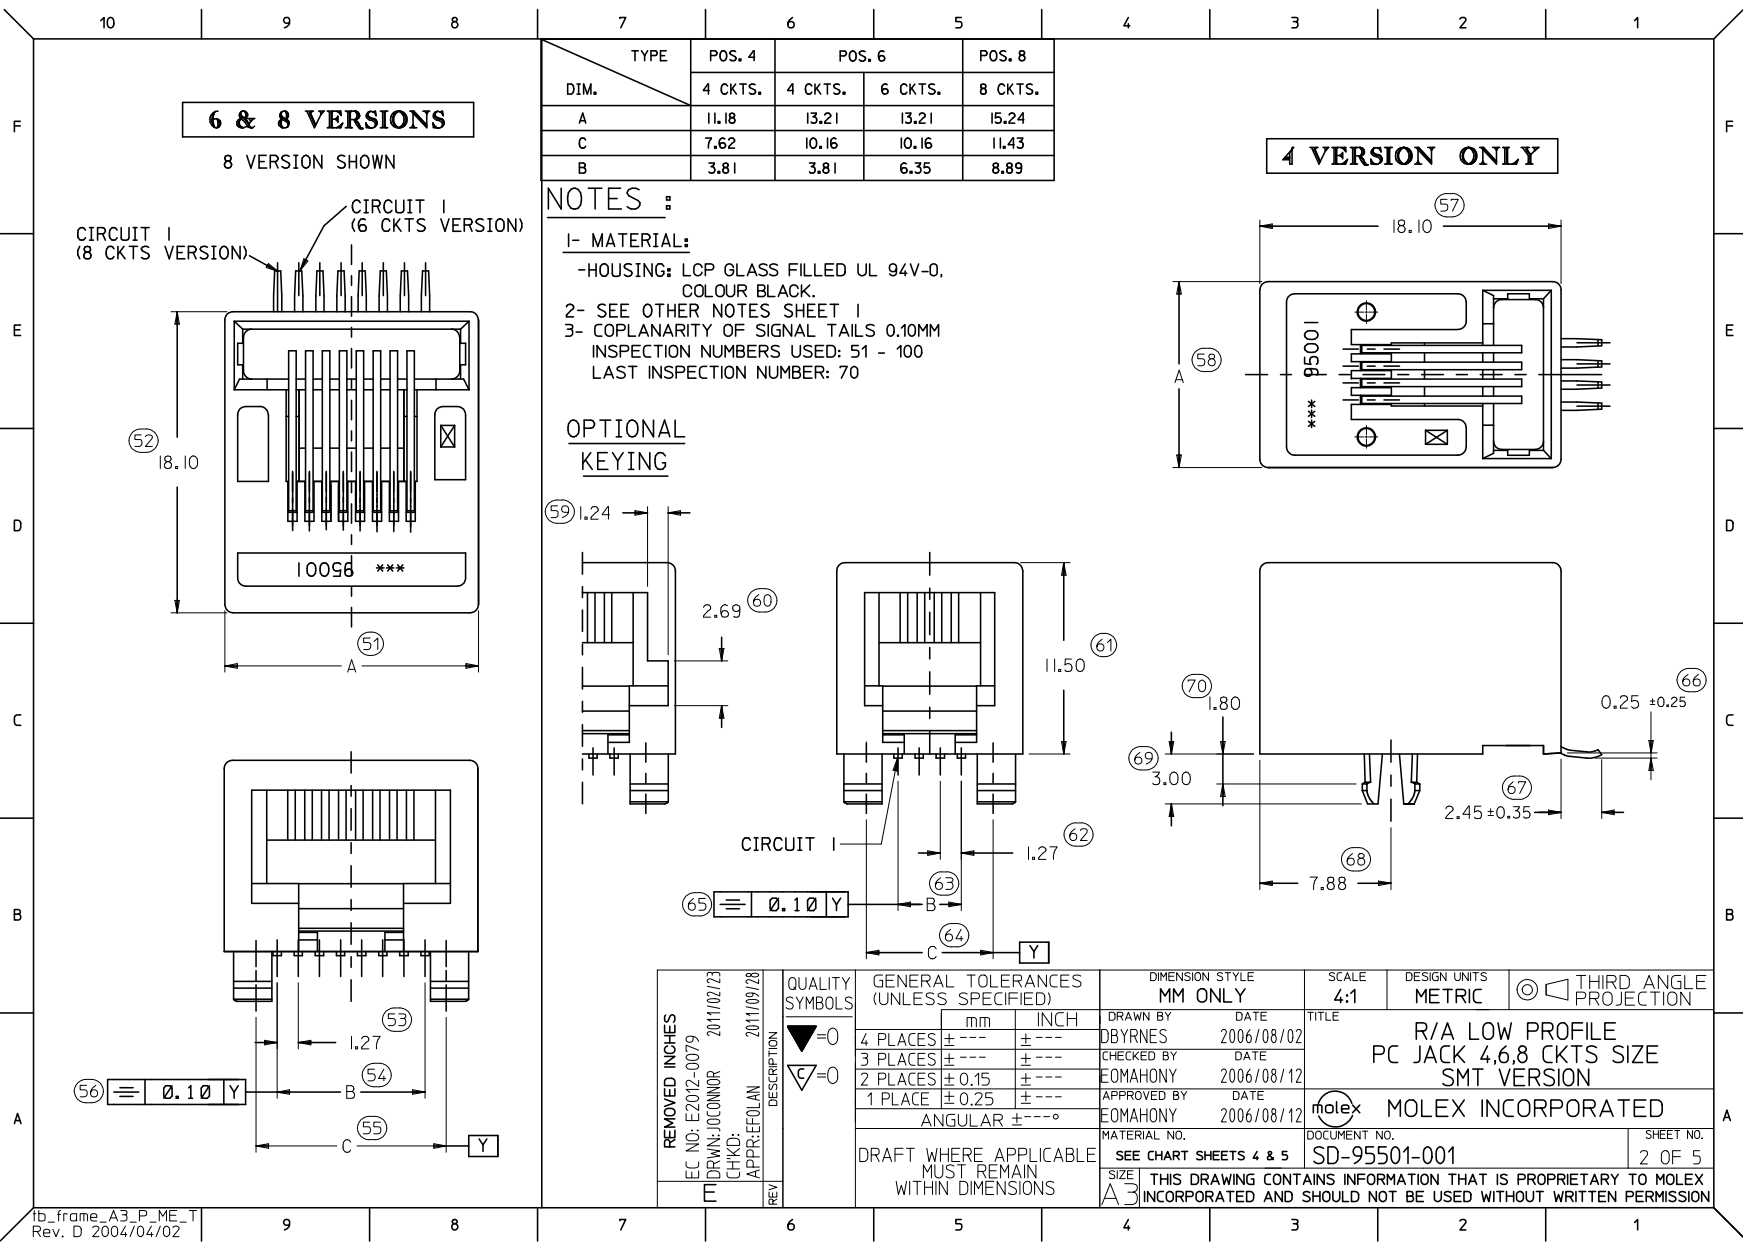
[picture p165: page 1]

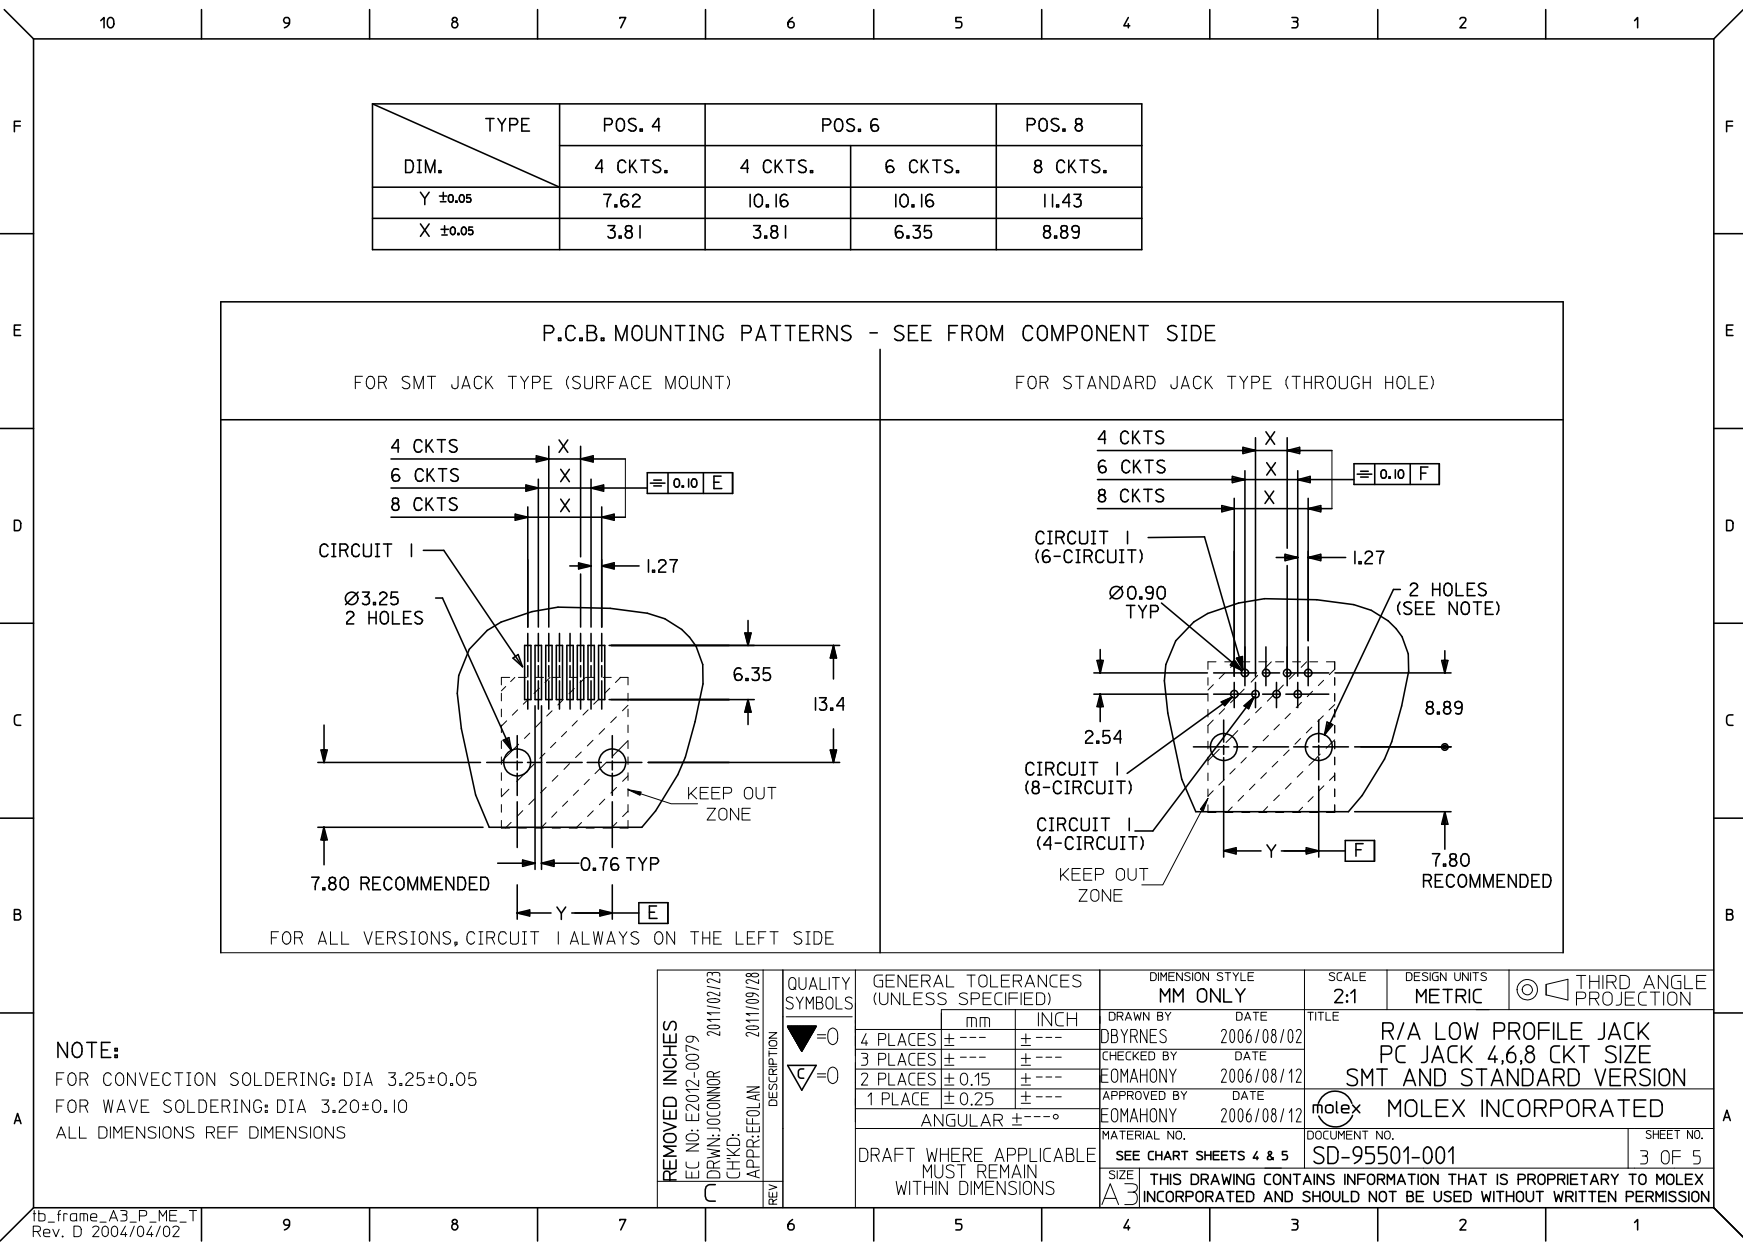
[picture p166: page 2]

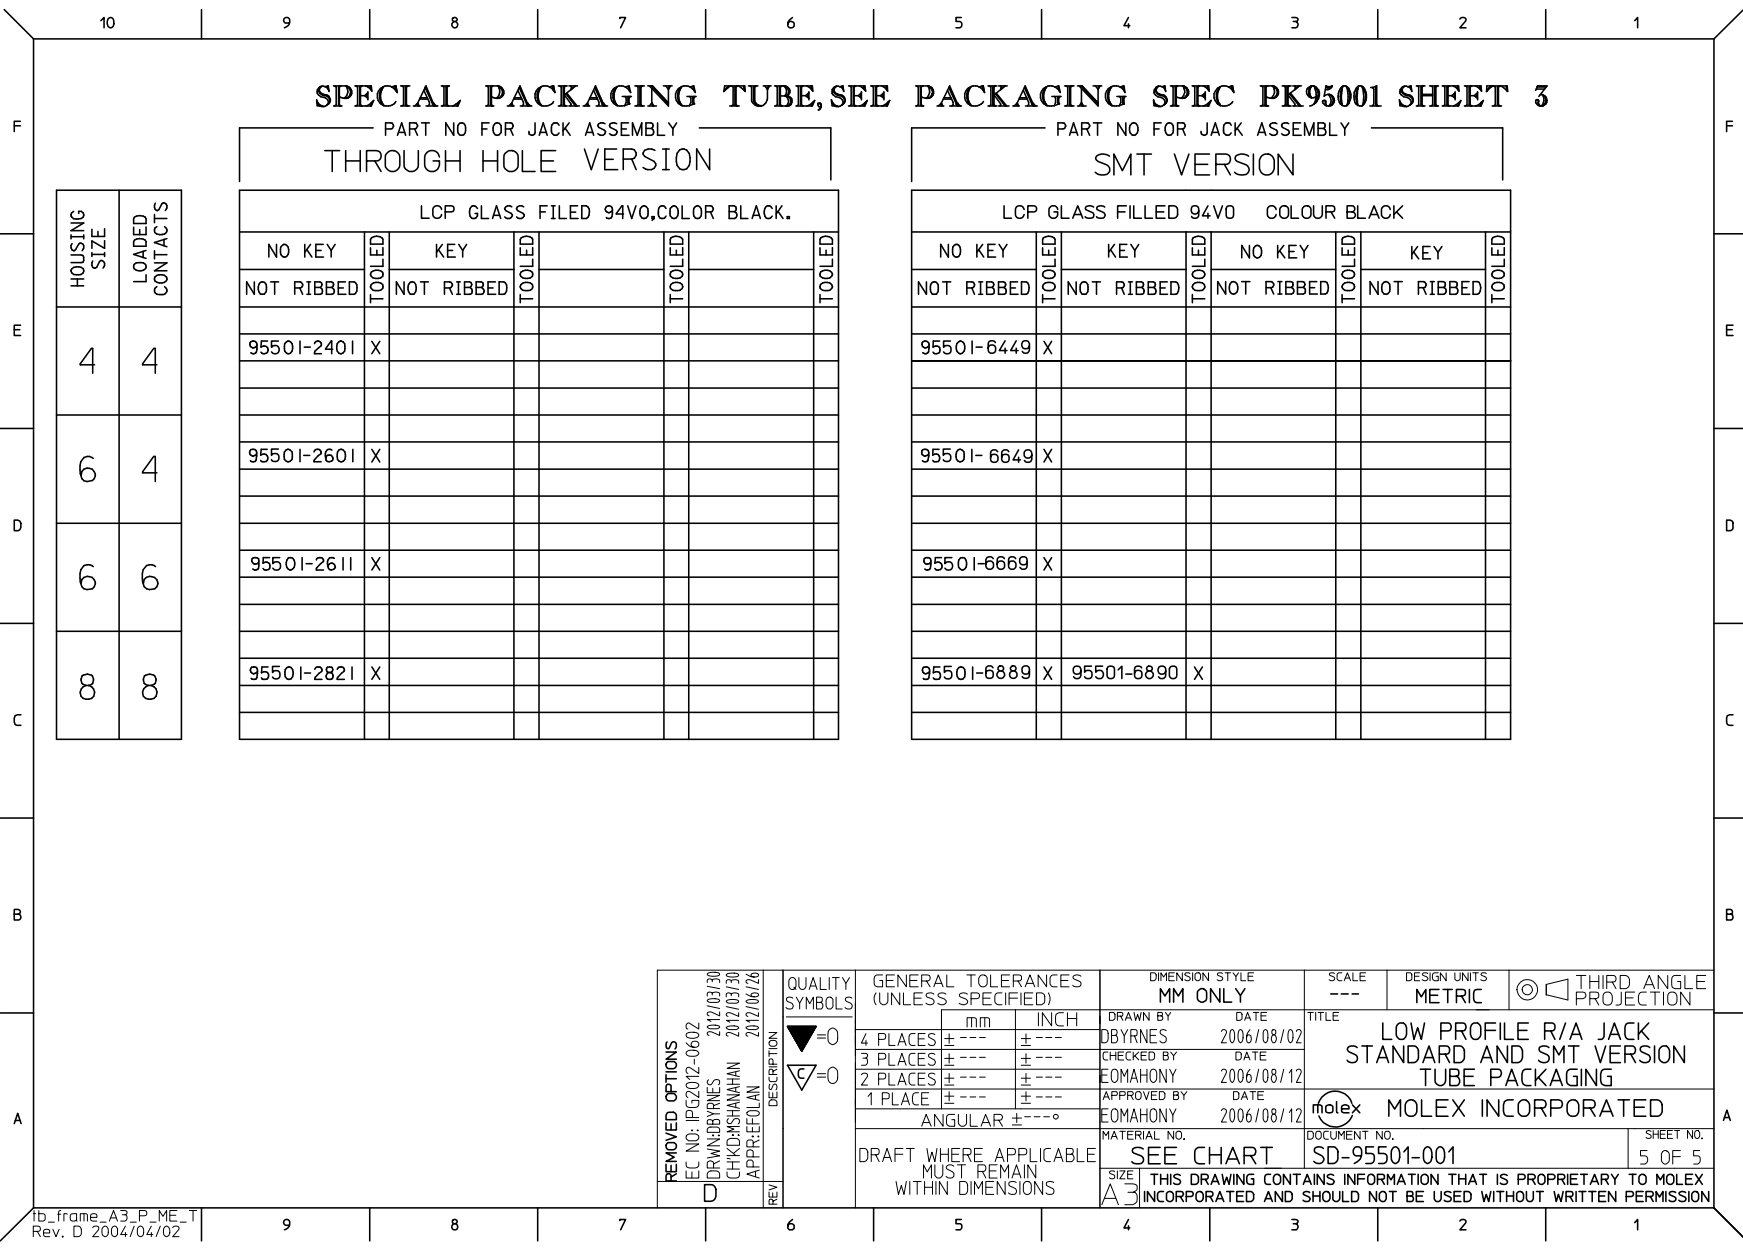
[picture p167: page 3]
