hbitter/DNMS/PCBs/DNMS-RPI-HAT/DNMS-RPI-HAT-V1.0/Phoenix_MKDS/MKDS-1-5-2-5-08_FAM.pdf

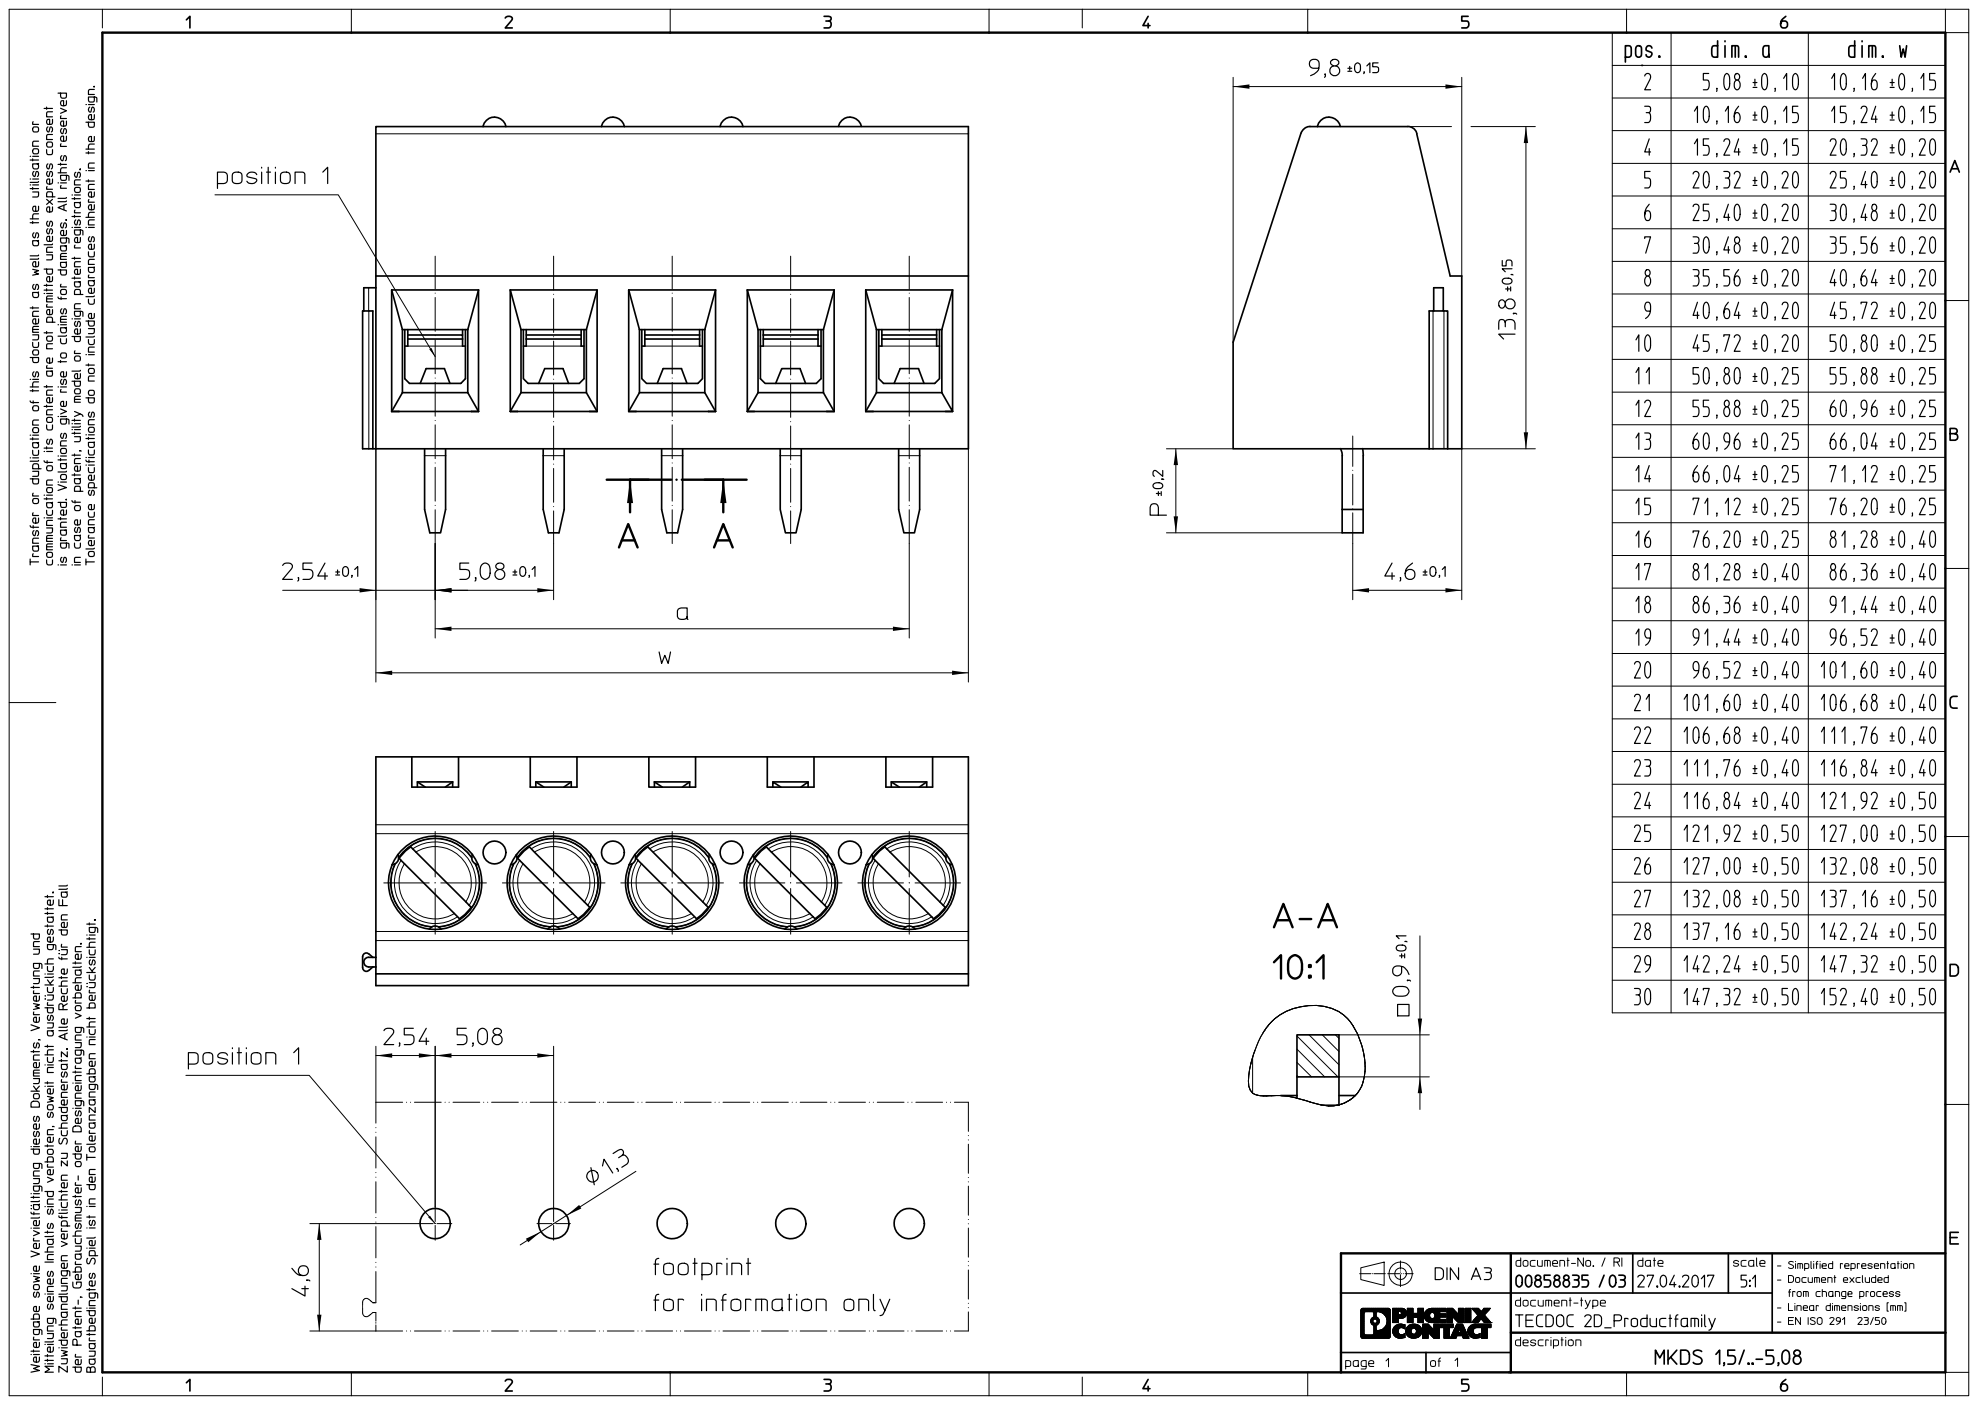
[picture p168: page 1]
