hbitter/DNMS/PCBs/DNMS-T4.0/DNMS-T4.0-V1.5/schematic DNMS-T4.0-V1.5.pdf

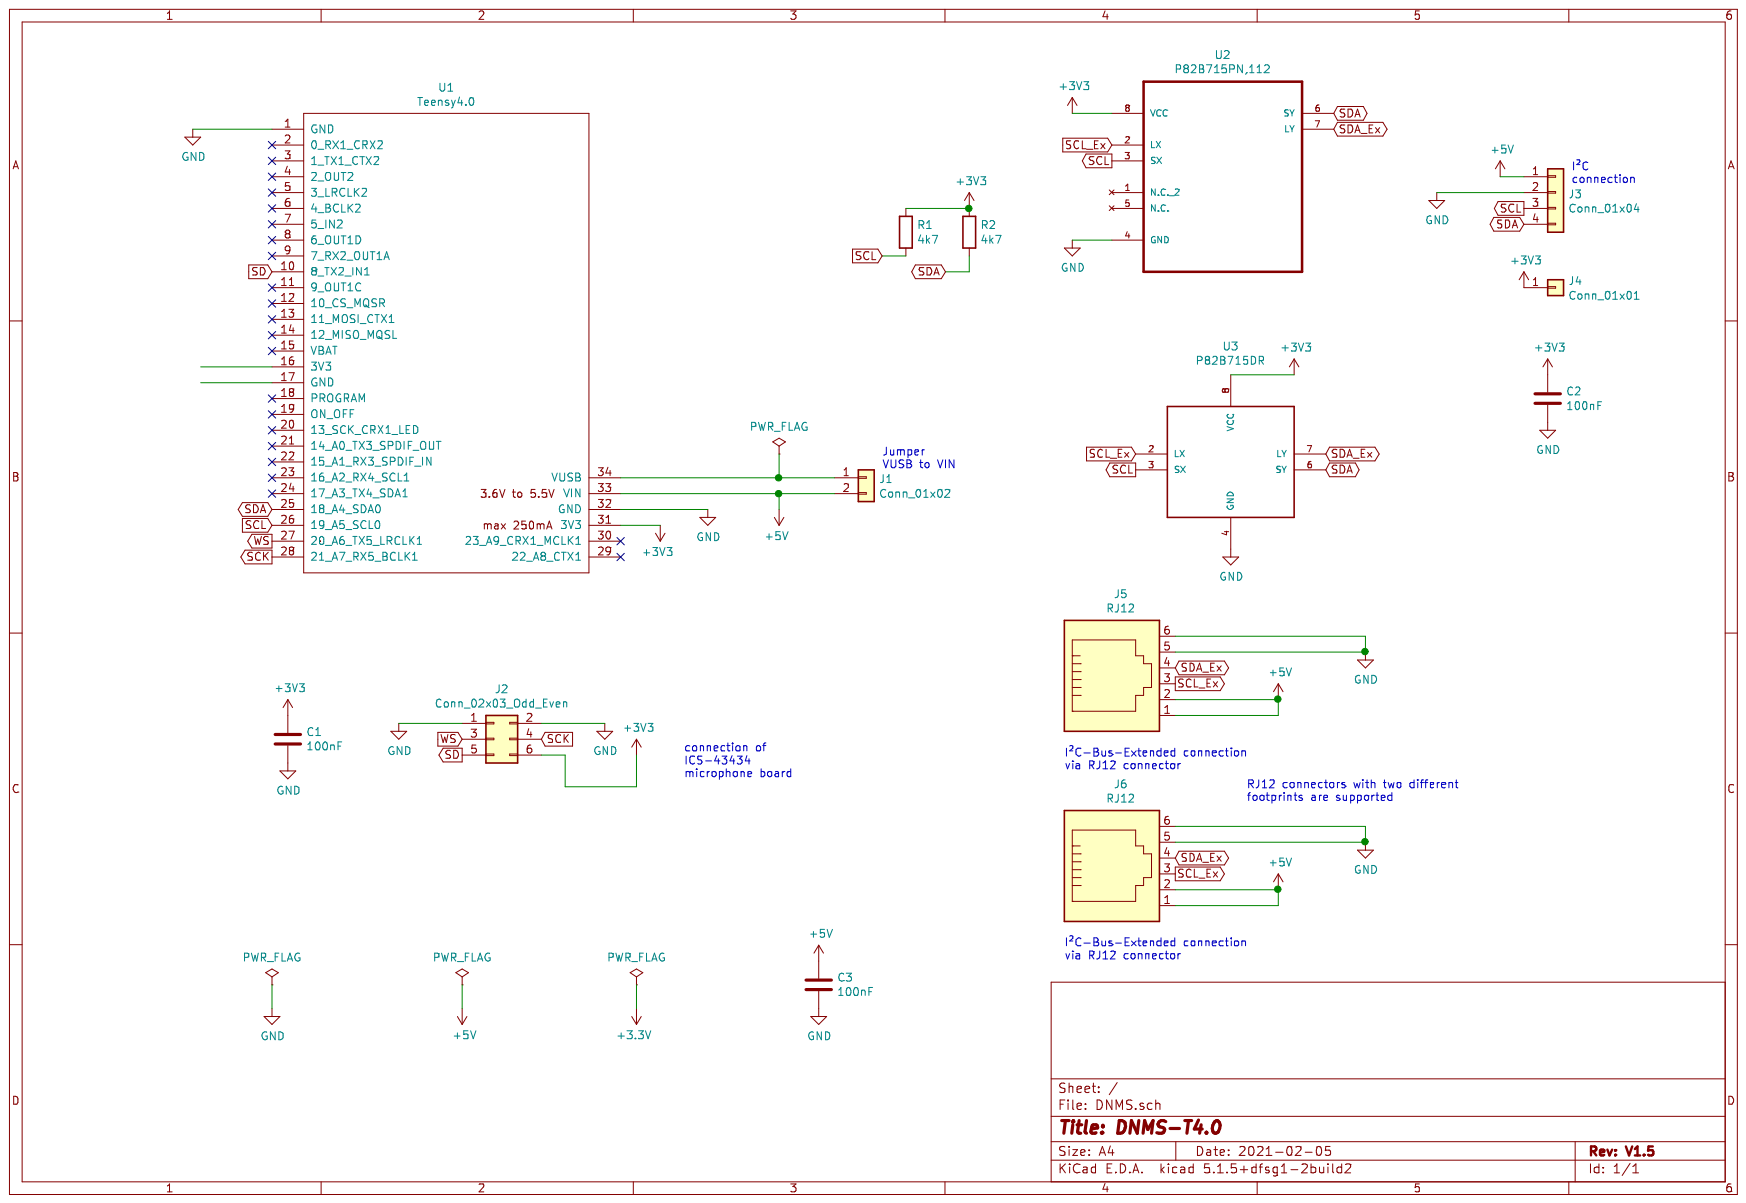
[picture p169: page 1]
