hbitter/DNMS/PCBs/ICS-43434 microphone PCB/ICS-43434-PCB-V1.3/schematic.pdf

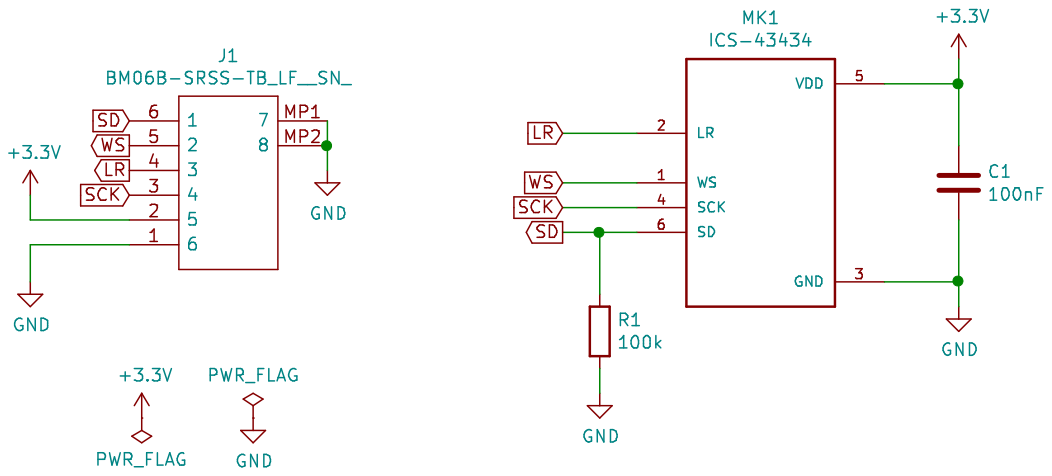
[picture p170: page 1]
