hbitter/DNMS/PCBs/Airrohr-PCB/old versions/Airrohr-PCB-V1.5/schematic AIRROHR-V1.5.pdf

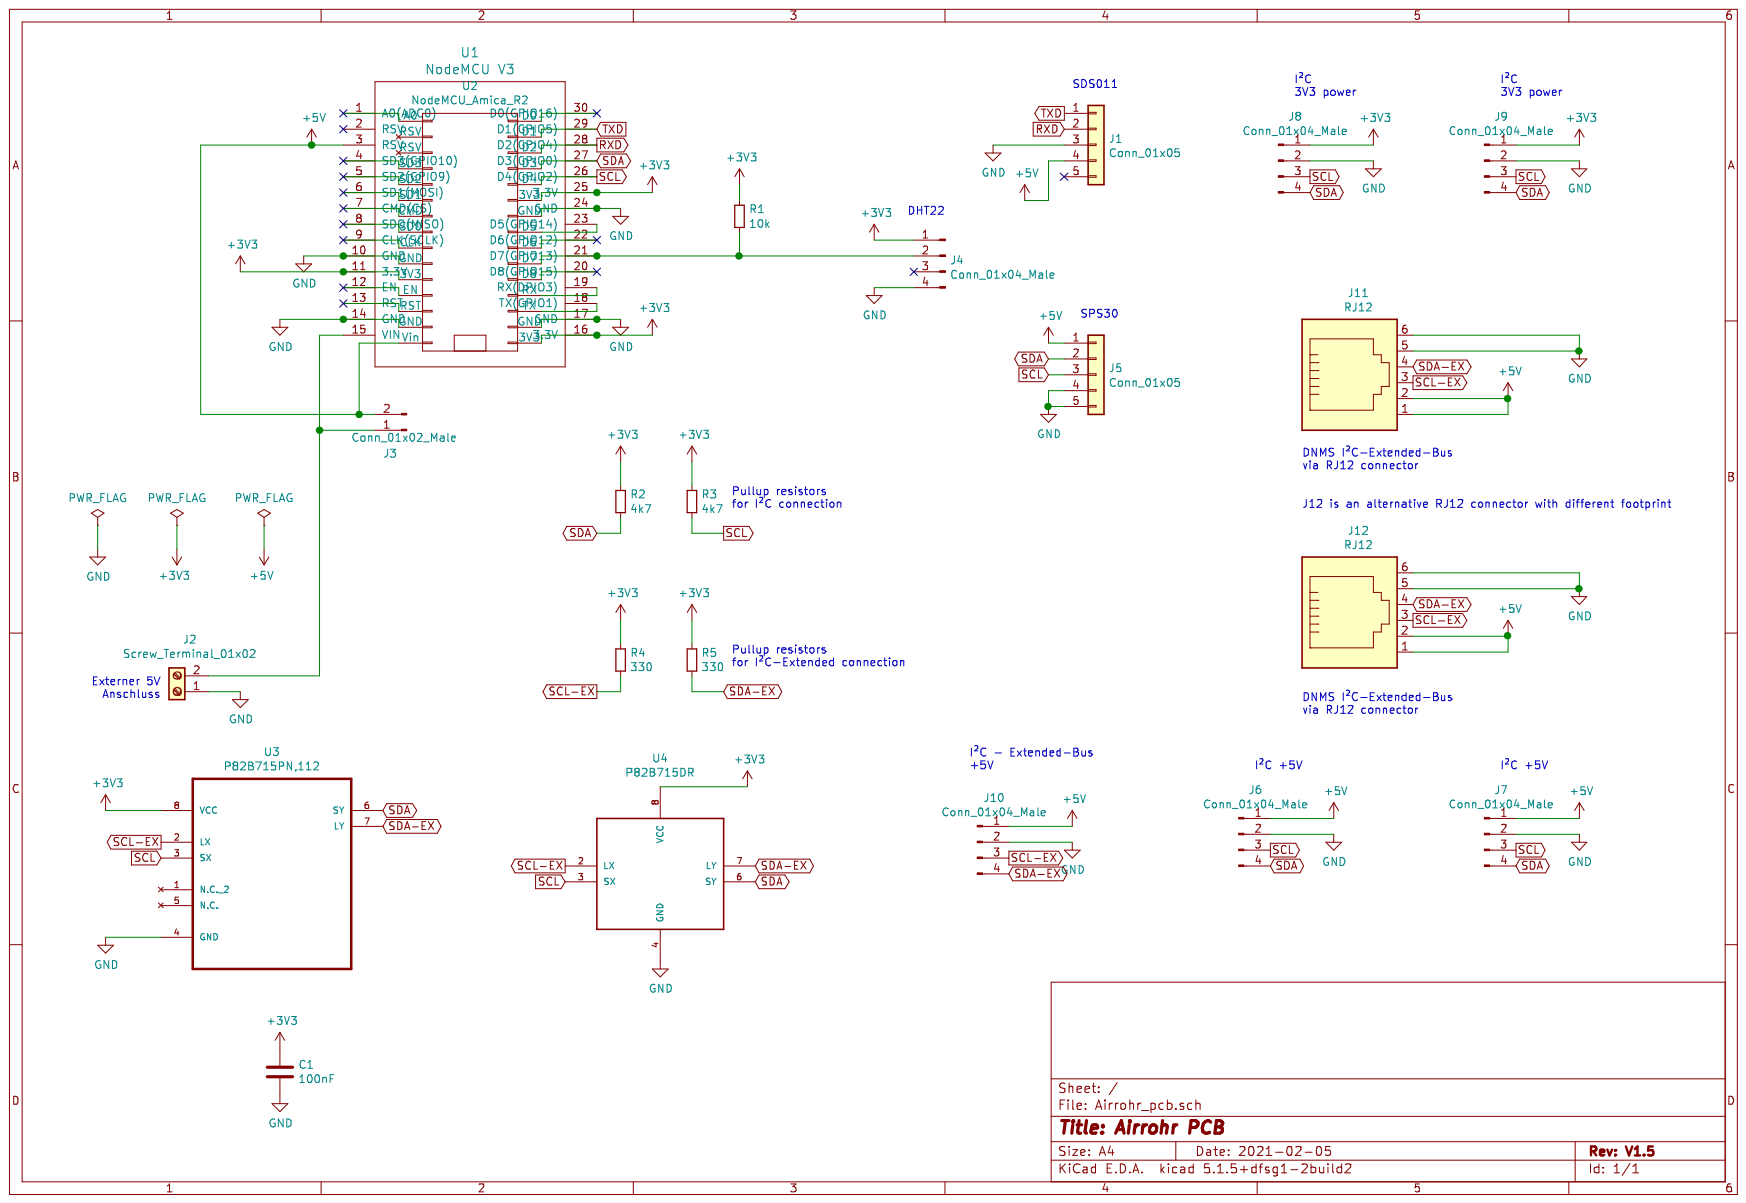
[picture p171: page 1]
