hbitter/DNMS/PCBs/DNMS-T4.0/old versions/DNMS-T4.0-V1.4/schematic DNMS-T4.0-V1.4.pdf

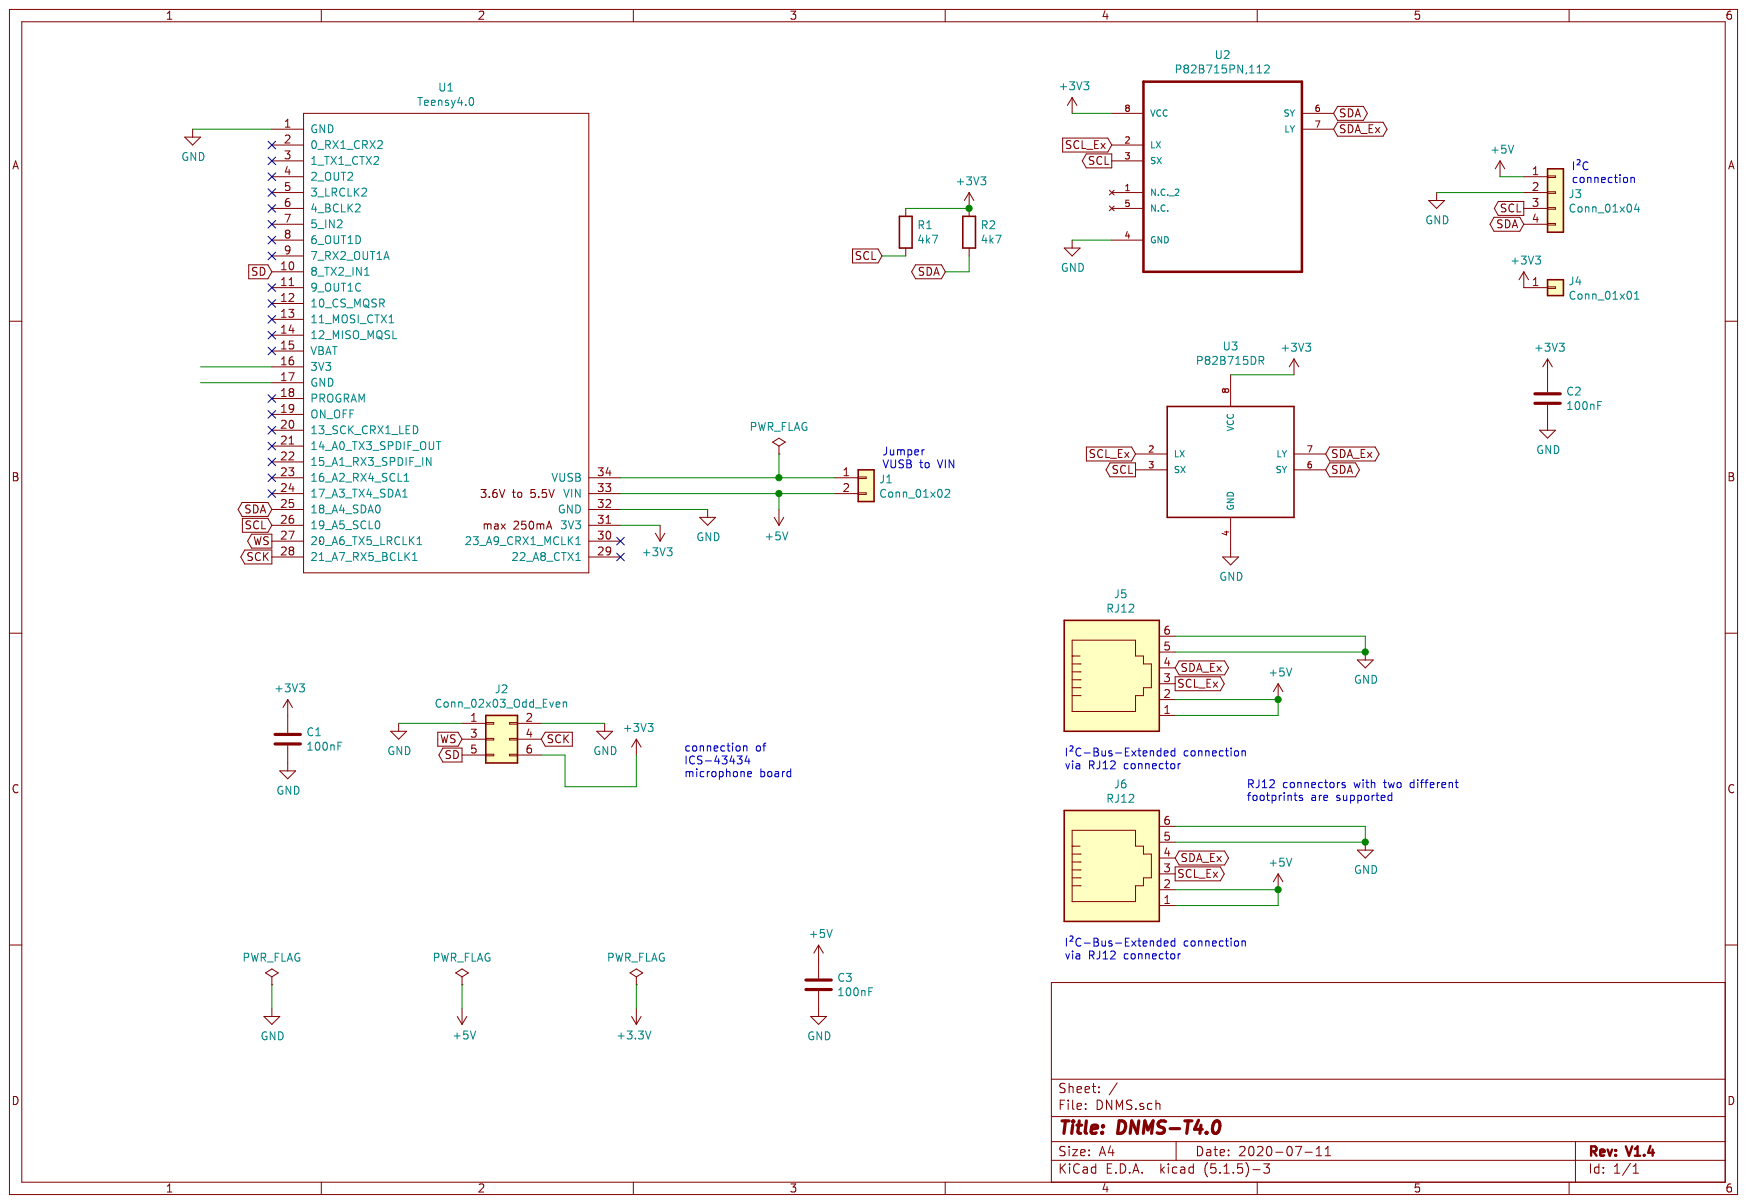
[picture p172: page 1]
