hbitter/DNMS/PCBs/Airrohr-PCB/old versions/Airrohr-PCB-V1.4/schematic AIRROHR-V1.4.pdf

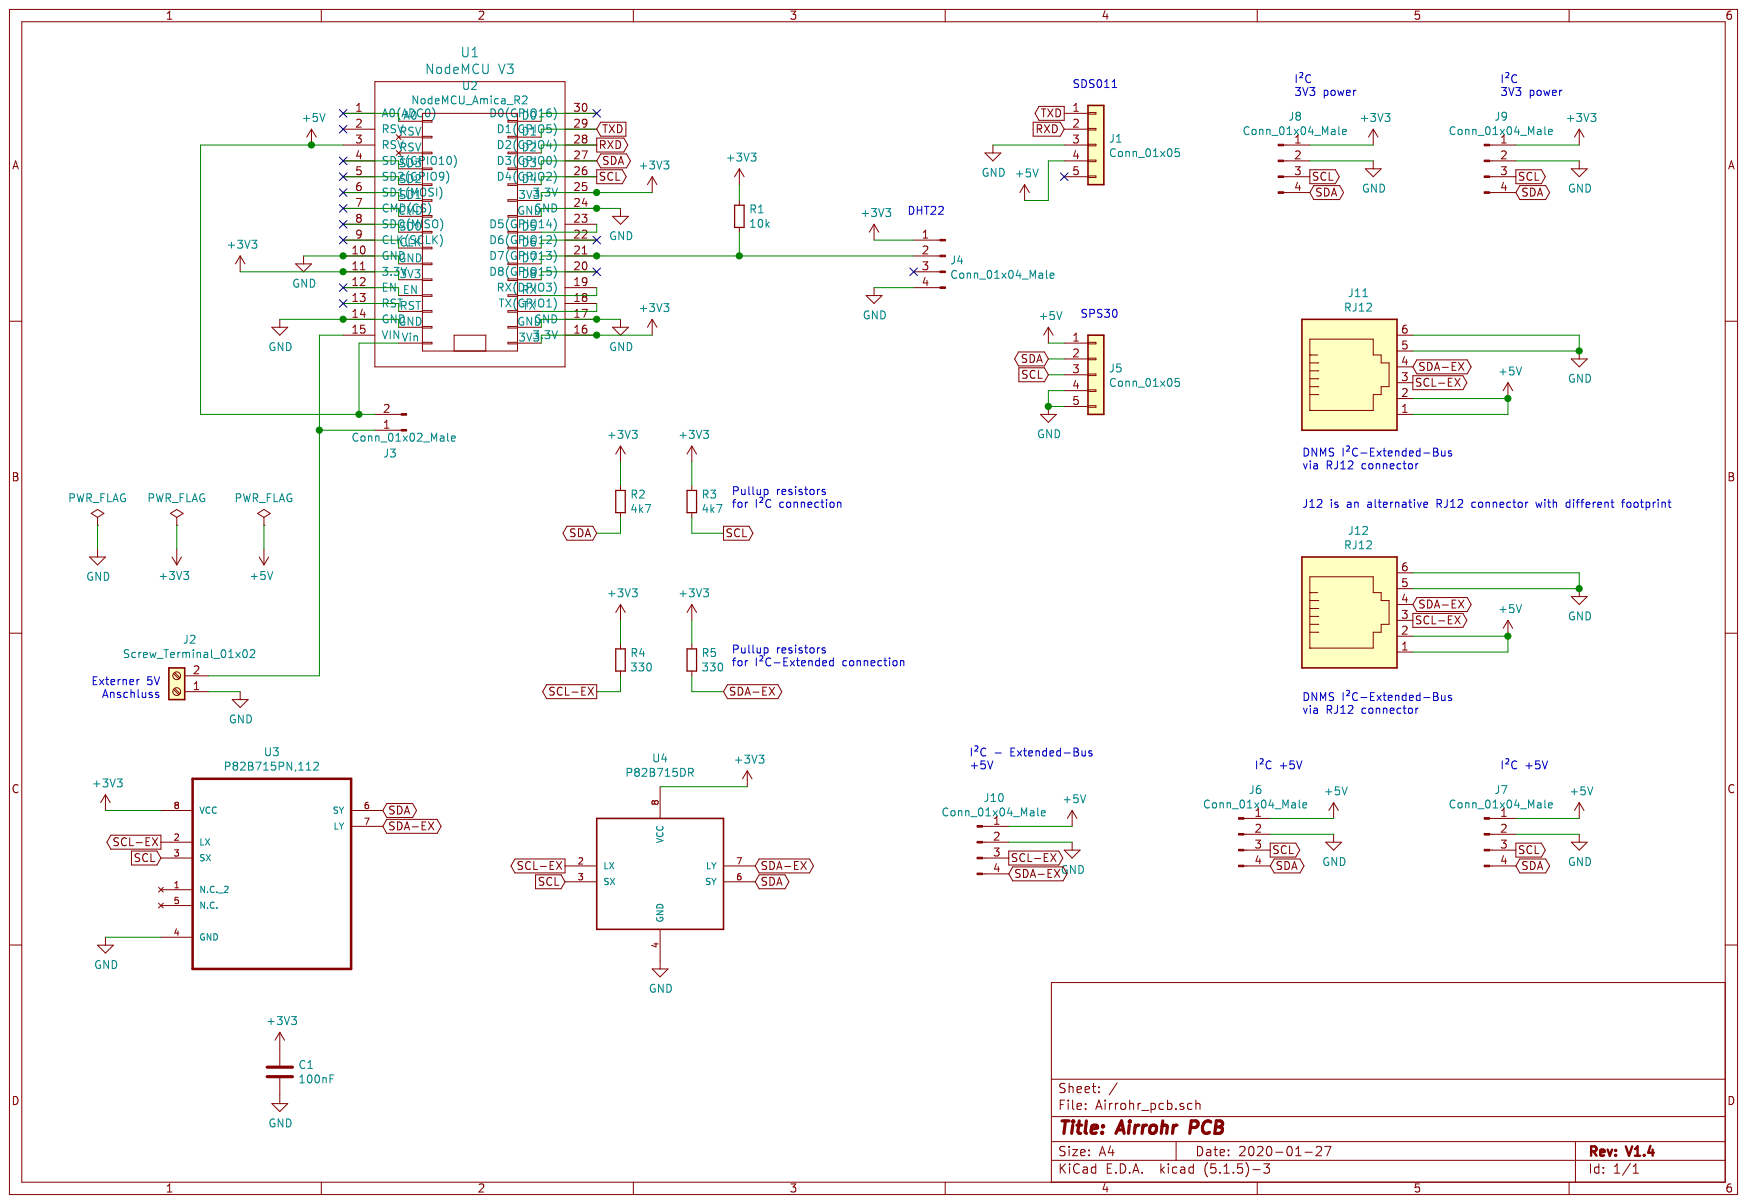
[picture p173: page 1]
