hbitter/DNMS/PCBs/Airrohr PCB/Airrohr PCB V1.1 KiCad/Airrohr V1.1 Schaltplan.pdf

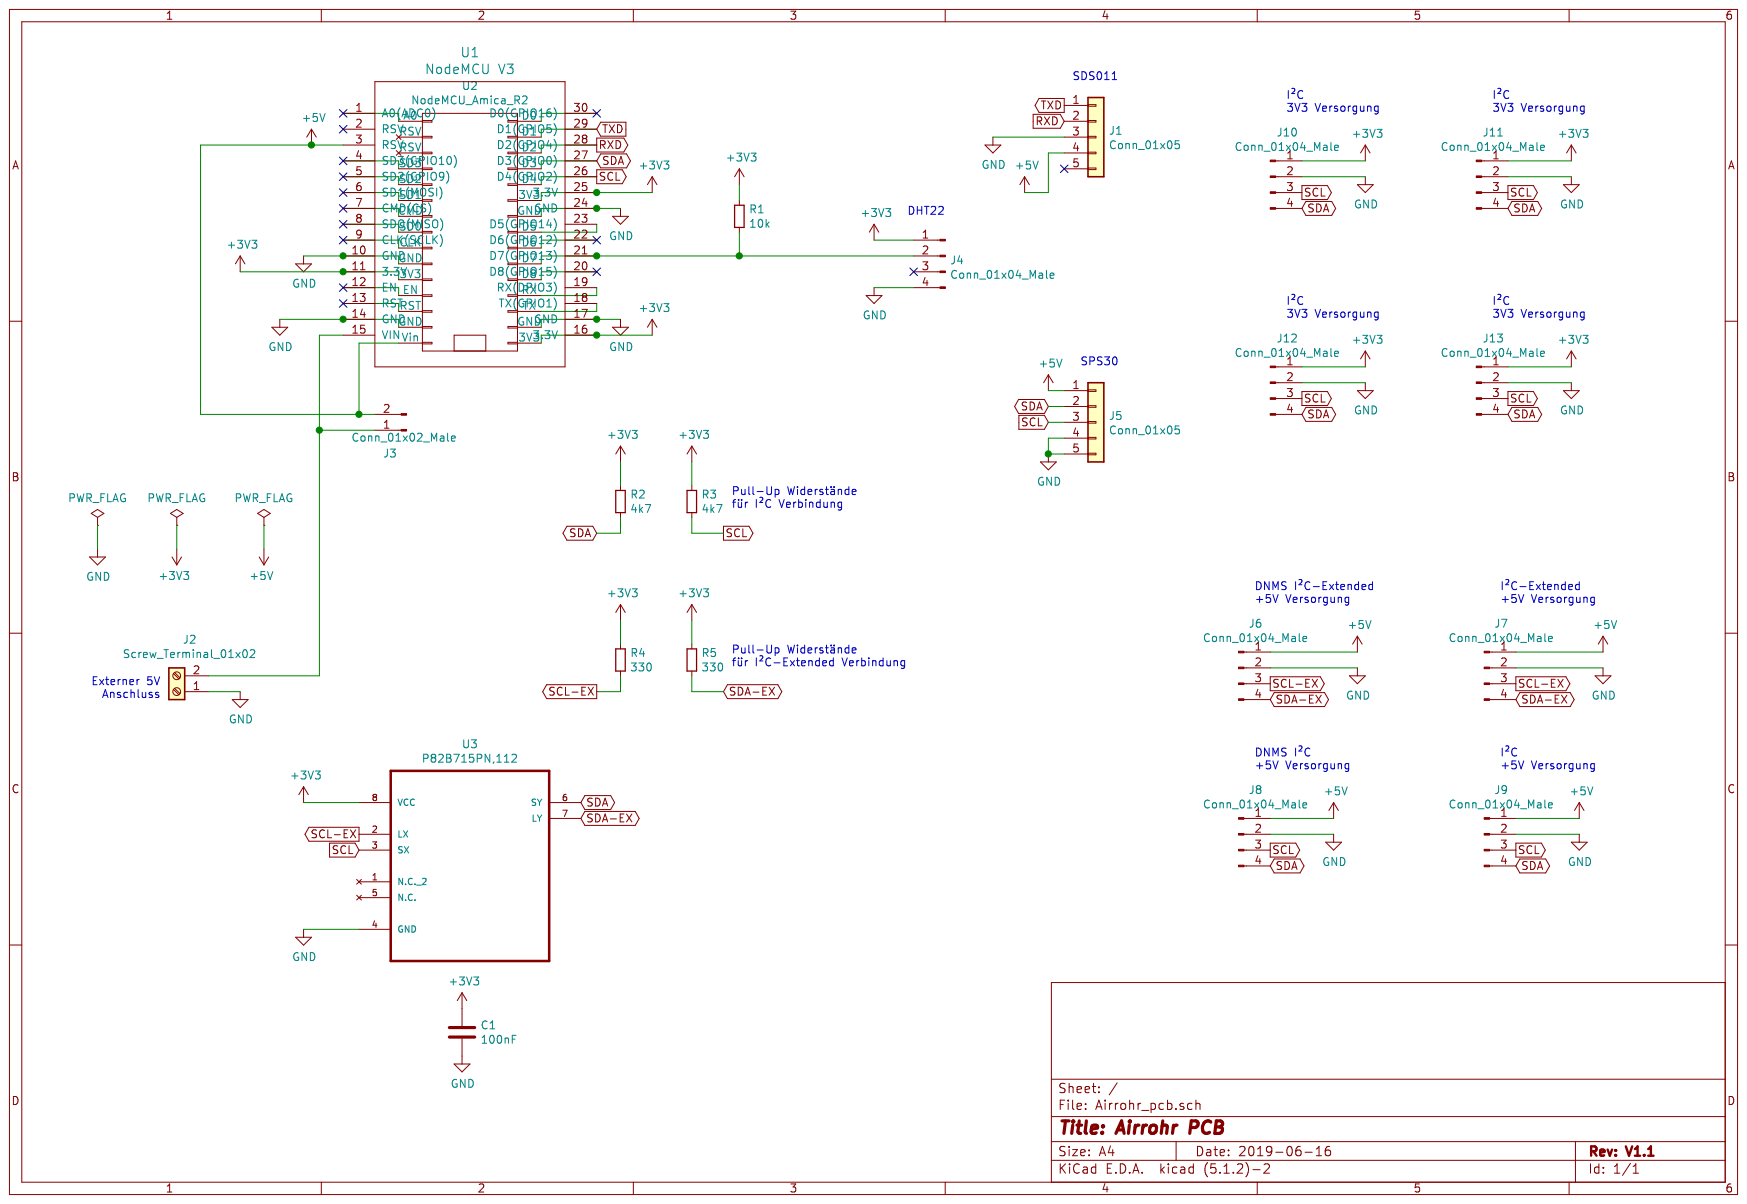
[picture p174: page 1]
