hbitter/DNMS/PCBs/DNMS-T3.6/old versions/DNMS-T3.6-V1.3/Schaltplan.pdf

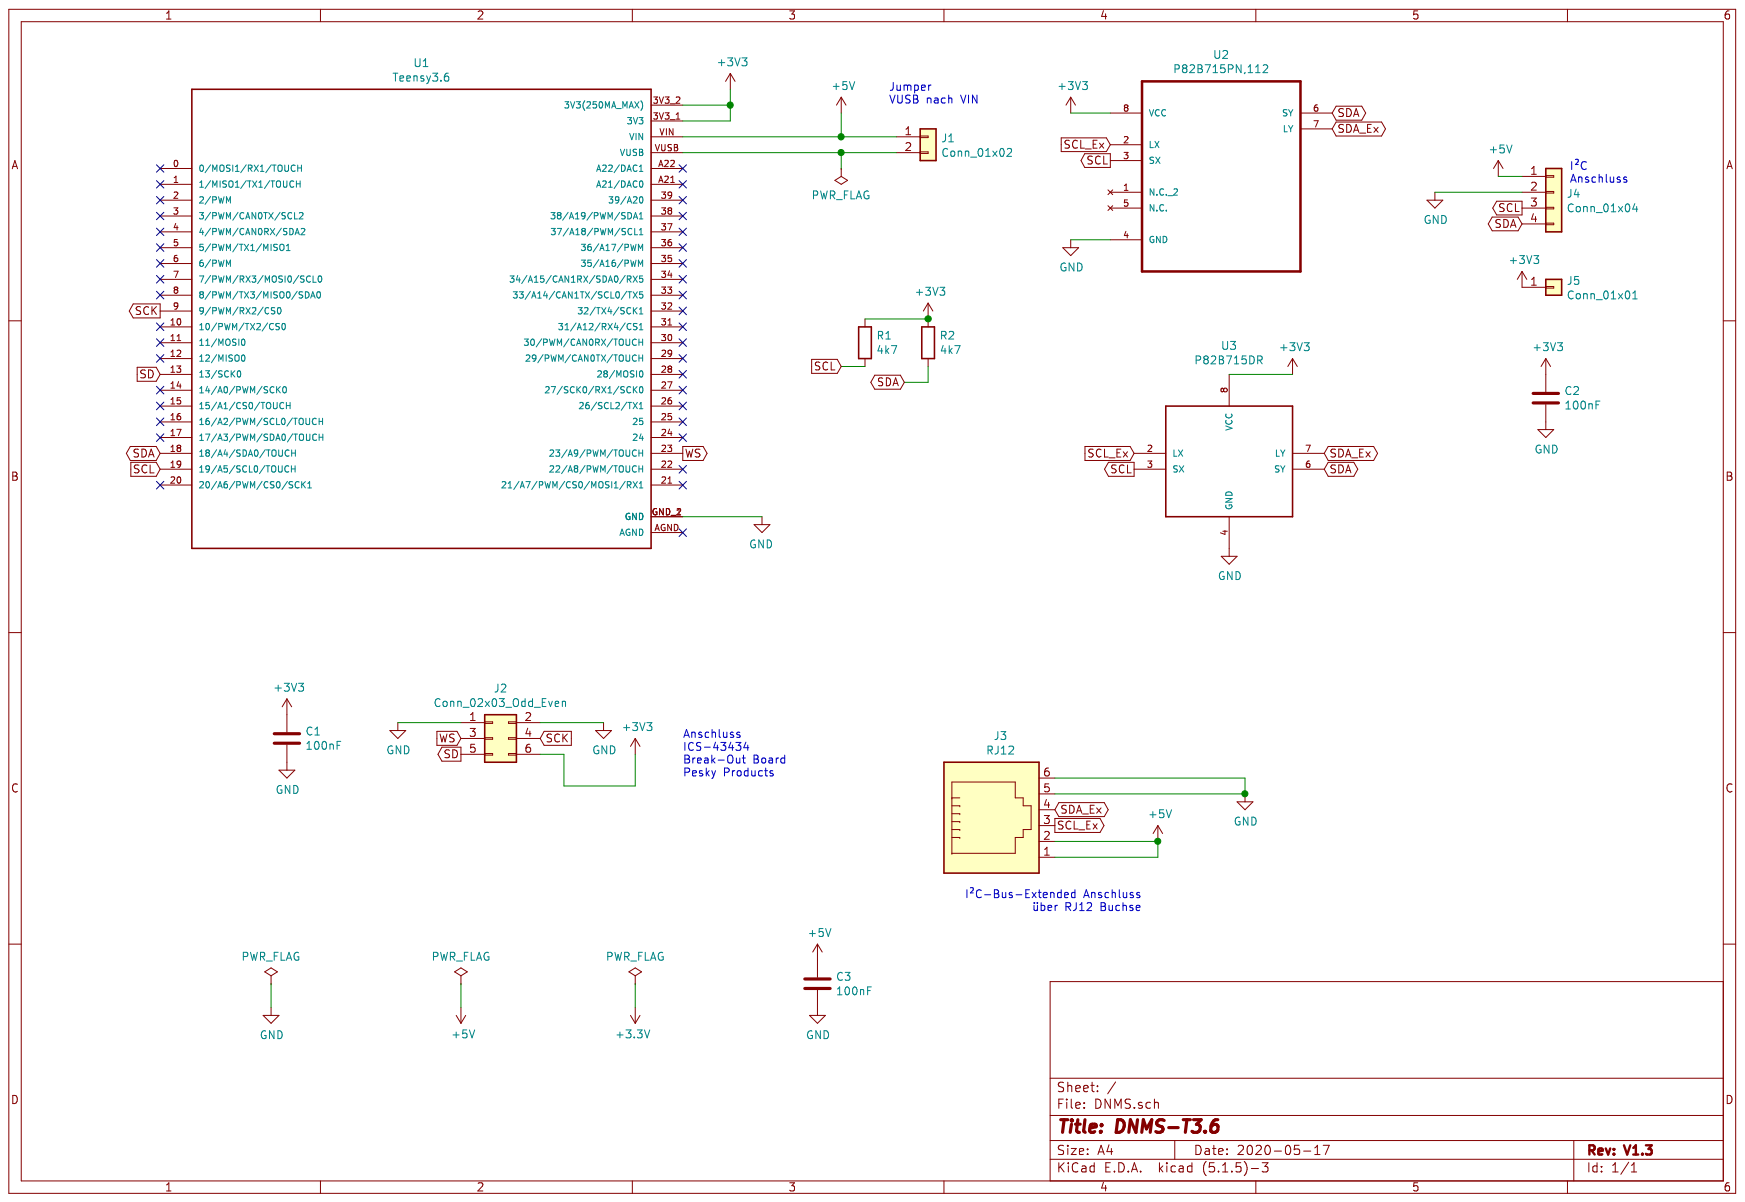
[picture p175: page 1]
