hbitter/DNMS/PCBs/DNMS-T4.0/old versions/DNMS-T4 V1.2/DNMS.kicad_pcb

## KiCad design PCBs/DNMS-T4.0/old versions/DNMS-T4 V1.2/DNMS.kicad_pcb (2021-01-29, an earlier design)

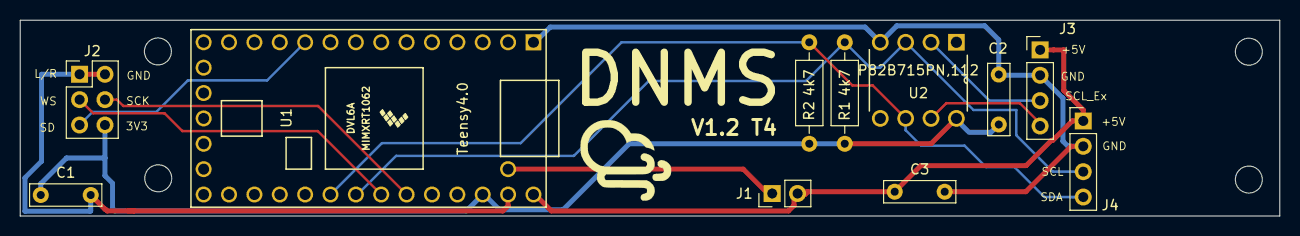
[picture p192: board PCBs/DNMS-T4.0/old versions/DNMS-T4 V1.2/DNMS.kicad_pcb from above]

Board: 2 copper layers, 126.1 x 19.6 mm, 15 parts (0 on the bottom side), 11 nets.

Parts:
C1, C2, C3: 100nF; C_Rect_L7.0mm_W2.0mm_P5.00mm
J1: Conn_01x02; PinHeader_1x02_P2.54mm_Vertical
J2: Conn_2Rows-07Pins; PinHeader_2x03_P2.54mm_Vertical
J3, J4: Conn_01x04; PinHeader_1x04_P2.54mm_Vertical
R1, R2: 4k7; R_Axial_DIN0207_L6.3mm_D2.5mm_P10.16mm_Horizontal
REF1, REF1#2, REF1#3, REF2: MountingHole_2.7mm_M2.5
U1: Teensy4.0; Teensy40
U2: P82B715PN,112; DIP254P762X420-8

Connections:
+3V3: C1.1, C2.1, J2.6, R1.1, R2.1, U1.31, U2.8
+5V: C3.1, J1.2, J3.1, J4.1, U1.33
GND: C1.2, C2.2, C3.2, J2.1, J2.2, J3.2, J4.2, U1.1, U1.32, U2.4
unnamed: J1.1, U1.34
SCK: J2.4, U1.28
SCL: J4.3, R1.2, U1.26, U2.3
SCL_Ex: J3.3, U2.2
SD: J2.5, U1.10
SDA: J4.4, R2.2, U1.25, U2.6
SDA_Ex: J3.4, U2.7
WS: J2.3, U1.27
