hbitter/DNMS/PCBs/DNMS-T3.6/old versions/DNMS-T3.6-V1.2/DNMS.kicad_pcb

## KiCad design PCBs/DNMS-T3.6/old versions/DNMS-T3.6-V1.2/DNMS.kicad_pcb (2021-01-29, an earlier design)

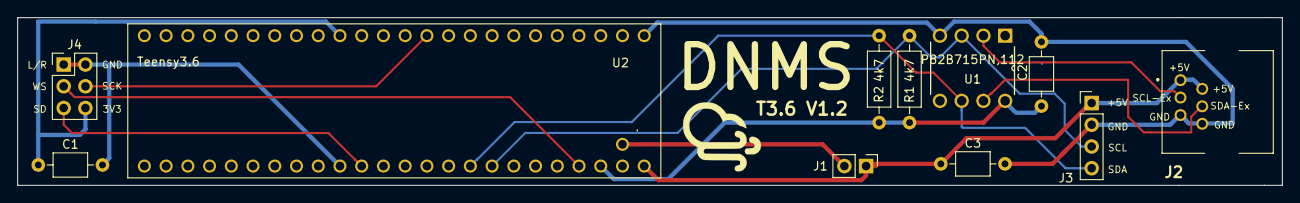
[picture p193: board PCBs/DNMS-T3.6/old versions/DNMS-T3.6-V1.2/DNMS.kicad_pcb from above]

Board: 2 copper layers, 147.8 x 19.6 mm, 11 parts (0 on the bottom side), 9 nets.

Parts:
C1, C2, C3: 100nF; C_Axial_L3.8mm_D2.6mm_P7.50mm_Horizontal
J1: Conn_01x02; PinHeader_1x02_P2.54mm_Vertical
J2: RJ12; RJ12_Pulse_E5566Q0LK22L
J3: Conn_01x04; PinHeader_1x04_P2.54mm_Vertical
J4: Conn_2Rows-07Pins; PinHeader_2x03_P2.54mm_Vertical
R1, R2: 4k7; R_Axial_DIN0207_L6.3mm_D2.5mm_P10.16mm_Horizontal
U1: P82B715PN,112; DIP254P762X420-8
U2: Teensy3.6

Connections:
+3V3: C1.1, C2.1, J4.6, R1.1, R2.1, U1.8, U2.3V3_1, U2.3V3_2
+5V: C3.1, J1.1, J2.1, J2.2, J3.1, U2.VIN
GND: C1.2, C2.2, C3.2, J2.5, J2.6, J3.2, J4.1, J4.2, U1.4, U2.GND_1, U2.GND_2
unnamed: J1.2, U2.VUSB
SCK: J4.4, U2.9
SCL: J3.3, R1.2, U1.3, U2.19
SD: J4.5, U2.13
SDA: J3.4, R2.2, U1.6, U2.18
WS: J4.3, U2.23
