hbitter/DNMS/PCBs/DNMS-T3.6/old versions/DNMS-T3.6-V1.3/DNMS.kicad_pcb

## KiCad design PCBs/DNMS-T3.6/old versions/DNMS-T3.6-V1.3/DNMS.kicad_pcb (2021-01-29, an earlier design)

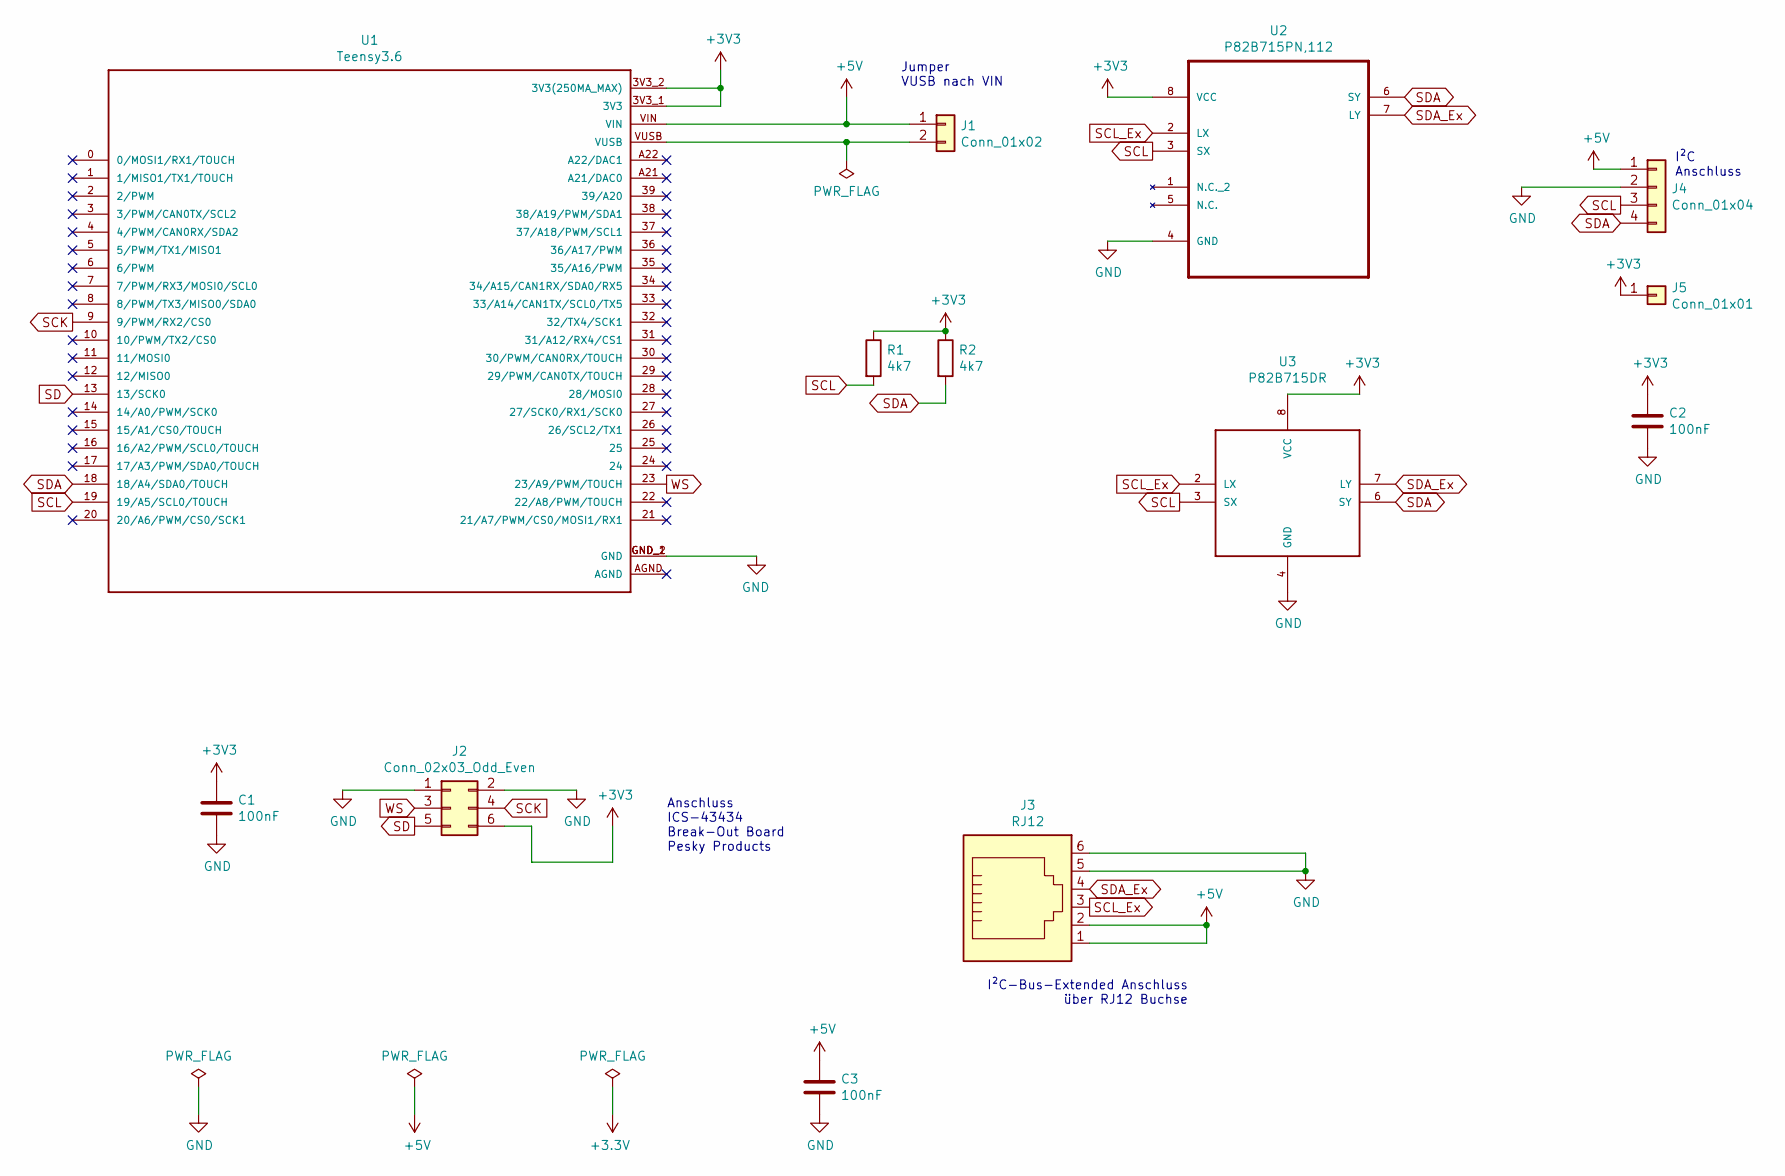
[picture p194: schematic DNMS.sch, DNMS-T3.6]

Parts:
C1, C2, C3: 100nF; C_THT_100nF_L9.0mm_W2.0mm_P5.00mm_P7.50mm
J1: Conn_01x02; PinHeader_1x02_P2.54mm_Vertical
J2: Conn_02x03_Odd_Even; PinHeader_2x03_P2.54mm_Vertical
J3: RJ12; RJ12_Pulse_E5566Q0LK22L
J4: Conn_01x04; PinHeader_1x04_P2.54mm_Vertical
J5: Conn_01x01; PinHeader_1x01_P2.54mm_Vertical
R1, R2: 4k7; R_Axial_DIN0207_L6.3mm_D2.5mm_P10.16mm_Horizontal
U1: Teensy3.6
U2: P82B715PN,112; DIP254P762X420-8
U3: P82B715DR; SOIC8

Connections:
+3V3: C1.1, C2.1, J2.6, J5.1, R1.1, R2.1, U1.3V3_1 (3V3), U1.3V3_2 (3V3(250MA_MAX)), U2.8 (VCC), U3.8 (VCC); also elsewhere on the board
+5V: C3.1, J1.1, J3.1, J3.2, J4.1, U1.VIN; also elsewhere on the board
GND: C1.2, C2.2, C3.2, J2.1, J2.2, J3.5, J3.6, J4.2, U1.GND_1 (GND), U1.GND_2 (GND), U2.4 (GND), U3.4 (GND); also elsewhere on the board
unnamed 3: J1.2, U1.VUSB; also elsewhere on the board
SCK: J2.4, U1.9 (9/PWM/RX2/CS0); also elsewhere on the board
SCL: J4.3, R1.2, U1.19 (19/A5/SCL0/TOUCH), U2.3 (SX), U3.3 (SX); also elsewhere on the board
SCL_Ex: J3.3, U2.2 (LX), U3.2 (LX)
SD: J2.5, U1.13 (13/SCK0); also elsewhere on the board
SDA: J4.4, R2.2, U1.18 (18/A4/SDA0/TOUCH), U2.6 (SY), U3.6 (SY); also elsewhere on the board
SDA_Ex: J3.4, U2.7 (LY), U3.7 (LY)
WS: J2.3, U1.23 (23/A9/PWM/TOUCH); also elsewhere on the board

Notes on the sheet:
I²C Anschluss
Anschluss ICS-43434 Break-Out Board Pesky Products
I²C-Bus-Extended Anschluss über RJ12 Buchse
Jumper VUSB nach VIN

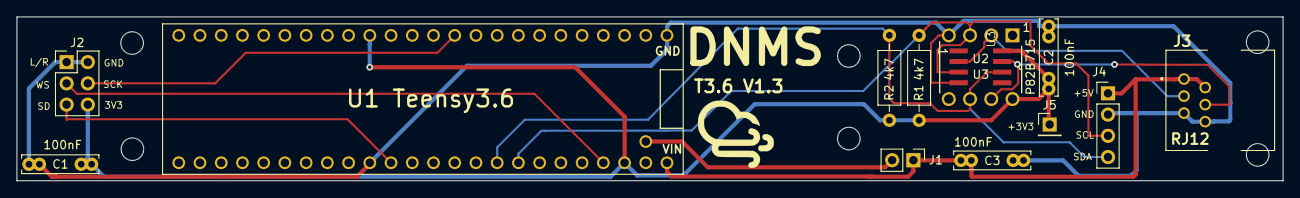
[picture p195: board PCBs/DNMS-T3.6/old versions/DNMS-T3.6-V1.3/DNMS.kicad_pcb from above]

Board: 2 copper layers, 151.5 x 19.6 mm, 19 parts (0 on the bottom side), 11 nets.

Other parts of the board:
REF1, REF1#2, REF1#3, REF1#4, REF1#5, REF1#6: MountingHole_2.7mm_M2.5
U1 Teensy3.6: VAL**; Teensy3.6

Their connections:
+3V3: U1 Teensy3.6.3V3_1, U1 Teensy3.6.3V3_2; also elsewhere on the board
+5V: U1 Teensy3.6.VIN; also elsewhere on the board
GND: U1 Teensy3.6.GND_1, U1 Teensy3.6.GND_2; also elsewhere on the board
unnamed 3: U1 Teensy3.6.VUSB; also elsewhere on the board
SCK: U1 Teensy3.6.9; also elsewhere on the board
SCL: U1 Teensy3.6.19; also elsewhere on the board
SD: U1 Teensy3.6.13; also elsewhere on the board
SDA: U1 Teensy3.6.18; also elsewhere on the board
WS: U1 Teensy3.6.23; also elsewhere on the board
