hbitter/DNMS/PCBs/DNMS-T3.6/old versions/DNMS-T3.6 V1.1/DNMS.kicad_pcb

## KiCad design PCBs/DNMS-T3.6/old versions/DNMS-T3.6 V1.1/DNMS.kicad_pcb (2021-01-29, an earlier design)

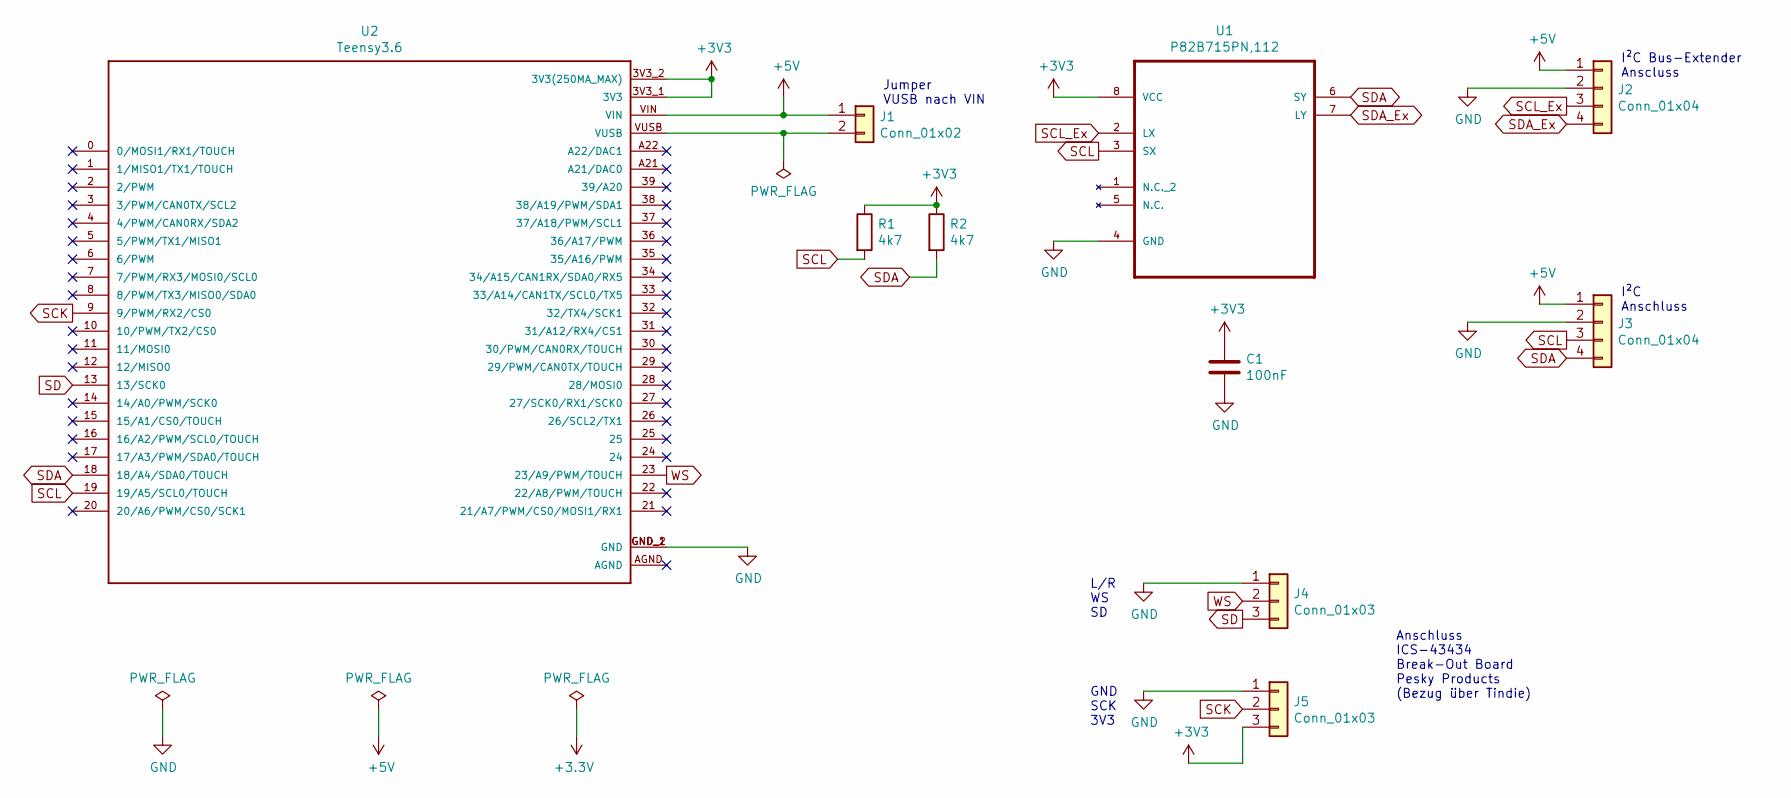
[picture p196: schematic DNMS.sch, DNMS - Digital Noise Measurement Sensor]

Parts:
C1: 100nF; C_Axial_L3.8mm_D2.6mm_P7.50mm_Horizontal
J1: Conn_01x02; PinHeader_1x02_P2.54mm_Vertical
J2, J3: Conn_01x04; PinHeader_1x04_P2.54mm_Vertical
J4, J5: Conn_01x03; PinHeader_1x03_P2.54mm_Vertical
R1, R2: 4k7; R_Axial_DIN0207_L6.3mm_D2.5mm_P10.16mm_Horizontal
U1: P82B715PN,112; DIP254P762X420-8
U2: Teensy3.6

Connections:
+3V3: C1.1, J5.3, R1.1, R2.1, U1.8 (VCC), U2.3V3_1 (3V3), U2.3V3_2 (3V3(250MA_MAX))
+5V: J1.1, J2.1, J3.1, U2.VIN
GND: C1.2, J2.2, J3.2, J4.1, J5.1, U1.4 (GND), U2.GND_1 (GND), U2.GND_2 (GND)
unnamed: J1.2, U2.VUSB
SCK: J5.2, U2.9 (9/PWM/RX2/CS0)
SCL: J3.3, R1.2, U1.3 (SX), U2.19 (19/A5/SCL0/TOUCH)
SCL_Ex: J2.3, U1.2 (LX)
SD: J4.3, U2.13 (13/SCK0)
SDA: J3.4, R2.2, U1.6 (SY), U2.18 (18/A4/SDA0/TOUCH)
SDA_Ex: J2.4, U1.7 (LY)
WS: J4.2, U2.23 (23/A9/PWM/TOUCH)

Notes on the sheet:
I²C Bus-Extender Anscluss
I²C Anschluss
Jumper VUSB nach VIN
L/R WS SD
Anschluss ICS-43434 Break-Out Board Pesky Products (Bezug über Tindie)
GND SCK 3V3

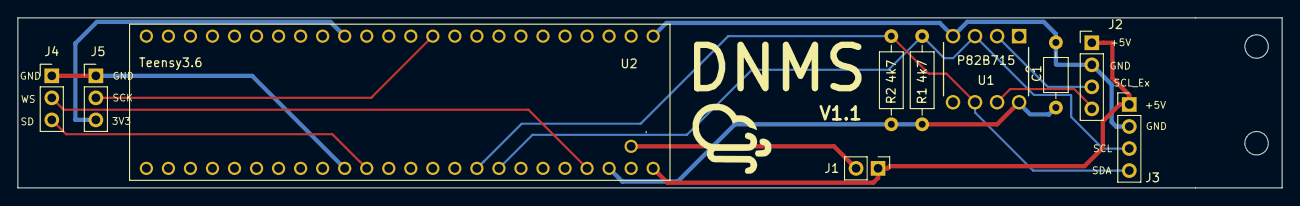
[picture p197: board PCBs/DNMS-T3.6/old versions/DNMS-T3.6 V1.1/DNMS.kicad_pcb from above]

Board: 2 copper layers, 145.7 x 19.6 mm, 12 parts (0 on the bottom side), 11 nets.

Other parts of the board:
REF1, REF2: MountingHole_2.7mm_M2.5
