hbitter/DNMS/Firmware/NodeMCU/airrohr-DNMS-6.0-en/airrohr-firmware/airrohr-firmware.ino

/*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
 * latest build using esp8266 BSP 3.1.2 , do not use a lower version than 3.1.1!
 * Compiled with FS 4MB (FS: 1MB  OTA: ~1019KB)

.. Variables and constants in RAM (global, static), used 47272 / 80192 bytes (58%)
║   SEGMENT  BYTES    DESCRIPTION
╠══ DATA     2984     initialized variables
╠══ RODATA   11552    constants       
╚══ BSS      32736    zeroed variables
. Instruction RAM (IRAM_ATTR, ICACHE_RAM_ATTR), used 63621 / 65536 bytes (97%)
║   SEGMENT  BYTES    DESCRIPTION
╠══ ICACHE   32768    reserved space for flash instruction cache
╚══ IRAM     30853    code in IRAM    
. Code in flash (default, ICACHE_FLASH_ATTR), used 653876 / 1048576 bytes (62%)
║   SEGMENT  BYTES    DESCRIPTION
╚══ IROM     653876   code in flash   

 ************************************************************************/

#include <WString.h>
#include <pgmspace.h>

// increment on change
#define SOFTWARE_VERSION_STR "AIRROHR-DNMS-6.0.4"
String SOFTWARE_VERSION(SOFTWARE_VERSION_STR);



/*****************************************************************
 * Includes                                                      *
 *****************************************************************/

#if defined(ESP8266)
#include <LittleFS.h>  // as alternative to SPIFFS
#include <Esp.h>
#include <ESP8266HTTPClient.h>
#include <ESP8266WiFi.h>
#include <ESP8266WebServer.h>
#include <ESP8266mDNS.h>
#include <SoftwareSerial.h>
#include <Hash.h>
#include <ctime>
#include <coredecls.h>
#include <sntp.h>
#include <PubSubClient.h>
#endif

#if defined(ESP32)
#define FORMAT_SPIFFS_IF_FAILED true
#include <FS.h>
#include <HTTPClient.h>
#include <SPIFFS.h>
#include <WiFi.h>
#include <WiFiClient.h>
#include <WiFiClientSecure.h>
#include <HardwareSerial.h>
//#include <hwcrypto/sha.h>
#include <esp32/sha.h>
#include <WebServer.h>
#include <ESPmDNS.h>
#endif

// includes common to ESP8266 and ESP32 (especially external libraries)
#include "./oledfont.h"  // avoids including the default Arial font, needs to be included before SSD1306.h
#include <SSD1306.h>
#include <SH1106.h>
#include <LiquidCrystal_I2C.h>
#define ARDUINOJSON_ENABLE_ARDUINO_STREAM 0
#define ARDUINOJSON_ENABLE_ARDUINO_PRINT 0
#define ARDUINOJSON_DECODE_UNICODE 0
#include <ArduinoJson.h>
#include <DNSServer.h>
#include "./DHT.h"
#include <Adafruit_HTU21DF.h>
#include <Adafruit_BMP085.h>
#include <Adafruit_SHT31.h>
#include <StreamString.h>
#include <DallasTemperature.h>
#include <SparkFun_SCD30_Arduino_Library.h>
#include <SparkFun_SCD4x_Arduino_Library.h>
#include <SensirionI2CSen5x.h>
#include <TinyGPS++.h>
#include "./bmx280_i2c.h"
#include "./sps30_i2c.h"
#include "./dnms_i2c.h"
#include "./dnms_calib_data.h"

#include "./intl.h"

#include "./utils.h"
#include "./defines.h"
#include "./ext_def.h"
#include "./html-content.h"

/*****************************************************************
 * MQTT transmission                                             *
 *****************************************************************/
WiFiClient wifi_client_for_mqtt;
PubSubClient mqtt_client;
String mqtt_topic = "";


/******************************************************************
 * The variables inside the cfg namespace are persistent          *
 * configuration values. They have defaults which can be          *
 * configured at compile-time via the ext_def.h file              *
 * They can be changed by the user via the web interface, the     *
 * changes are persisted to the flash and read back after reboot. *
 * Note that the names of these variables can't be easily changed *
 * as they are part of the json format used to persist the data.  *
 ******************************************************************/
#define sc_sending_intervall_ms 150000

namespace cfg {
unsigned debug_save;
unsigned debug = 1;

unsigned time_for_wifi_config = 300000;
unsigned sending_intervall_ms = sc_sending_intervall_ms;
unsigned i2c_gpio_scl = 2;
unsigned i2c_gpio_sda = 0;
unsigned dnms_2nd_interval_time = 60000;
unsigned dnms_2nd_threshold = 20;
unsigned dnms_2nd_number_measurements = 120;
unsigned dnms_2nd_gpio_pin = 16;
unsigned dnms_din01_pin = 12;
bool powersave = POWERSAVE;


char current_lang[3];

// credentials for basic auth of internal web server
bool www_basicauth_enabled = WWW_BASICAUTH_ENABLED;
char www_username[LEN_WWW_USERNAME];
char www_password[LEN_CFG_PASSWORD];

// wifi credentials
char wlanssid[LEN_WLANSSID];
bool with_wlanpwd = WITH_WLANPWD;
char wlanpwd[LEN_CFG_PASSWORD];

char static_ip[16];
char static_subnet[16];
char static_gateway[16];
char static_dns[16];

// credentials of the sensor in access point mode
char fs_ssid[LEN_FS_SSID] = FS_SSID;
char fs_pwd[LEN_CFG_PASSWORD] = FS_PWD;

bool start_on_full_minute = START_ON_FULL_MINUTE;
bool start_on_full_hour = START_ON_FULL_HOUR;
bool sensor_cyclic_restart = SENSOR_CYCLIC_RESTART;
unsigned sensor_cyclic_restart_time = 24;

// (in)active sensors
bool dht_read = DHT_READ;
bool htu21d_read = HTU21D_READ;
bool ppd_read = PPD_READ;
bool sds_read = SDS_READ;
bool pms_read = PMS_READ;
bool hpm_read = HPM_READ;
bool npm_read = NPM_READ;
bool npm_fulltime = NPM_FULLTIME;
bool ips_read = IPS_READ;
bool sps30_read = SPS30_READ;
bool sen5x_read = SEN5X_READ;
bool bmp_read = BMP_READ;
bool bmx280_read = BMX280_READ;
char height_above_sealevel[8] = "0";
bool sht3x_read = SHT3X_READ;
bool scd30_read = SCD30_READ;
bool scd4x_read = SCD4X_READ;
bool scd4x_low_power = SCD4X_LOW_POWER;
bool ds18b20_read = DS18B20_READ;
bool dnms_read = DNMS_READ;
bool dnms_read_active = false;
bool dnms_read_Z = DNMS_READ_Z;
bool dnms_read_Z_active = false;
bool dnms_read_C = DNMS_READ_C;
bool dnms_read_C_active = false;
bool dnms_read_spectrum = DNMS_READ_SPECTRUM;
bool dnms_read_spectrum_Z = DNMS_READ_SPECTRUM_Z;
bool dnms_read_spectrum_C = DNMS_READ_SPECTRUM_C;
bool dnms_read_spectrum_active = false;
bool dnms_read_spectrum_Z_active = false;
bool dnms_read_spectrum_C_active = false;
bool dnms_2nd_interval = DNMS_2nd_INTERVAL;
bool dnms_2nd_interval_Z = DNMS_2nd_INTERVAL_Z;
bool dnms_2nd_interval_C = DNMS_2nd_INTERVAL_C;
bool dnms_2nd_read_spectrum = DNMS_2nd_READ_SPECTRUM;
bool dnms_2nd_read_spectrum_Z = DNMS_2nd_READ_SPECTRUM_Z;
bool dnms_2nd_read_spectrum_C = DNMS_2nd_READ_SPECTRUM_C;
bool dnms_2nd_interval_active = false;
bool dnms_2nd_interval_Z_active = false;
bool dnms_2nd_interval_C_active = false;
bool dnms_2nd_read_spectrum_active = false;
bool dnms_2nd_read_spectrum_Z_active = false;
bool dnms_2nd_read_spectrum_C_active = false;
bool dnms_2nd_switch_output = DNMS_2nd_SWITCH_OUTPUT;
char dnms_correction[LEN_DNMS_CORRECTION] = DNMS_CORRECTION;
unsigned dnms_micro_type = 1;
bool gps_read = GPS_READ;
char temp_correction[LEN_TEMP_CORRECTION] = TEMP_CORRECTION;
bool dnms_read_din01 = DNMS_READ_DIN01;



// send to "APIs"
bool send2dusti = SEND2SENSORCOMMUNITY;
bool send2madavi = SEND2MADAVI;
bool send2sensemap = SEND2SENSEMAP;
bool send2fsapp = SEND2FSAPP;
bool send2aircms = SEND2AIRCMS;
bool send2custom = SEND2CUSTOM;
bool send2influx = SEND2INFLUX;
bool send2csv = SEND2CSV;
bool send2mqtt = SEND2MQTT;

bool auto_update = AUTO_UPDATE;
bool use_beta = USE_BETA;

// (in)active displays
bool has_display = HAS_DISPLAY;  // OLED with SSD1306 and I2C
bool has_sh1106 = HAS_SH1106;
bool has_flipped_display = HAS_FLIPPED_DISPLAY;
bool has_lcd1602 = HAS_LCD1602;
bool has_lcd1602_27 = HAS_LCD1602_27;
bool has_lcd2004 = HAS_LCD2004;
bool has_lcd2004_27 = HAS_LCD2004_27;

bool display_wifi_info = DISPLAY_WIFI_INFO;
bool display_device_info = DISPLAY_DEVICE_INFO;

// API settings
bool ssl_madavi = SSL_MADAVI;
bool ssl_dusti = SSL_SENSORCOMMUNITY;
char senseboxid[LEN_SENSEBOXID] = SENSEBOXID;

char host_influx[LEN_HOST_INFLUX];
char url_influx[LEN_URL_INFLUX];
unsigned port_influx = PORT_INFLUX;
char user_influx[LEN_USER_INFLUX] = USER_INFLUX;
char pwd_influx[LEN_PASS_INFLUX] = PWD_INFLUX;
char measurement_name_influx[LEN_MEASUREMENT_NAME_INFLUX];
bool ssl_influx = SSL_INFLUX;

char host_mqtt[LEN_HOST_MQTT];
unsigned port_mqtt = PORT_MQTT;
char user_mqtt[LEN_USER_MQTT] = USER_MQTT;
char pwd_mqtt[LEN_PASS_MQTT] = PWD_MQTT;
char measurement_name_mqtt[LEN_MEASUREMENT_NAME_MQTT];
char mqtt_main_topic[LEN_MQTT_MAIN_TOPIC];
bool id_as_mqtt_sub_topic = ID_AS_MQTT_SUB_TOPIC;
bool tls_mqtt = TLS_MQTT;

char host_custom[LEN_HOST_CUSTOM];
char url_custom[LEN_URL_CUSTOM];
bool ssl_custom = SSL_CUSTOM;
unsigned port_custom = PORT_CUSTOM;
char user_custom[LEN_USER_CUSTOM] = USER_CUSTOM;
char pwd_custom[LEN_CFG_PASSWORD] = PWD_CUSTOM;

char ntp_1[LEN_NTP_1];
char ntp_2[LEN_NTP_2];

void initNonTrivials(const char *id) {
  strcpy(cfg::current_lang, CURRENT_LANG);
  strcpy_P(www_username, WWW_USERNAME);
  strcpy_P(www_password, WWW_PASSWORD);
  strcpy_P(wlanssid, WLANSSID);
  strcpy_P(wlanpwd, WLANPWD);
  strcpy_P(host_custom, HOST_CUSTOM);
  strcpy_P(url_custom, URL_CUSTOM);
  strcpy_P(host_influx, HOST_INFLUX);
  strcpy_P(url_influx, URL_INFLUX);
  strcpy_P(measurement_name_influx, MEASUREMENT_NAME_INFLUX);
  strcpy_P(host_mqtt, HOST_MQTT);
  strcpy_P(measurement_name_mqtt, MEASUREMENT_NAME_MQTT);
  strcpy_P(ntp_1, NTP_SERVER_1);
  strcpy_P(ntp_2, NTP_SERVER_2);

  if (!*fs_ssid) {
    strcpy(fs_ssid, SSID_BASENAME);
    strcat(fs_ssid, id);
  }
}
}  // end of namespace cfg

#define JSON_BUFFER_SIZE 9216

LoggerConfig loggerConfigs[LoggerCount];

char time_string[24];
long int sample_count = 0;
bool htu21d_init_failed = false;
bool bmp_init_failed = false;
bool bmx280_init_failed = false;
bool sht3x_init_failed = false;
bool scd30_init_failed = false;
bool scd4x_init_failed = false;
bool dnms_init_failed = false;
bool gps_init_failed = false;
bool airrohr_selftest_failed = false;
bool led_status_state = false;
unsigned long led_timer;
unsigned din01_state = 0;
#define led_status_period_1 250
#define led_status D0

#if defined(ESP8266)
ESP8266WebServer server(80);
#endif
#if defined(ESP32)
WebServer server(80);
#endif

// default IPv4 address (ex. 192.168.4.1)
const uint8_t default_ip_first_octet = 192;
const uint8_t default_ip_second_octet = 168;
const uint8_t default_ip_third_octet = 4;
const uint8_t default_ip_fourth_octet = 1;

#include "./airrohr-cfg.h"

/*****************************************************************
 * Variables for Noise Measurement DNMS                          *
 *****************************************************************/
float last_value_dnms_laeq = -1.0;
float last_value_dnms_la_min = -1.0;
float last_value_dnms_la_max = -1.0;
float last_value_dnms_laeq_freq_spec[31] = { -1.0 };
float last_value_dnms_laeq_2nd = -1.0;
float last_value_dnms_la_min_2nd = -1.0;
float last_value_dnms_la_max_2nd = -1.0;
float last_value_dnms_laeq_freq_spec_2nd[31] = { -1.0 };
struct timeval dnms_now;
struct timeval dnms_2nd_now;
bool send_2nd_dnms = false;
uint16_t dnms_2nd_count = 0;
float last_value_dnms_lzeq = -1.0;
float last_value_dnms_lz_min = -1.0;
float last_value_dnms_lz_max = -1.0;
float last_value_dnms_lzeq_freq_spec[31] = { -1.0 };
float last_value_dnms_lzeq_2nd = -1.0;
float last_value_dnms_lz_min_2nd = -1.0;
float last_value_dnms_lz_max_2nd = -1.0;
float last_value_dnms_lzeq_freq_spec_2nd[31] = { -1.0 };
float last_value_dnms_lceq = -1.0;
float last_value_dnms_lc_min = -1.0;
float last_value_dnms_lc_max = -1.0;
float last_value_dnms_lceq_freq_spec[31] = { -1.0 };
float last_value_dnms_lceq_2nd = -1.0;
float last_value_dnms_lc_min_2nd = -1.0;
float last_value_dnms_lc_max_2nd = -1.0;
float last_value_dnms_lceq_freq_spec_2nd[31] = { -1.0 };
bool dnms_error = false;
uint16_t DNMS_error_continous_count = 0;
float dnms_corr_value;

/*****************************************************************
 * Variables for temperature correction                          *
 *****************************************************************/
float temp_corr_value;


/*****************************************************************
 * Display definitions                                           *
 *****************************************************************/
SSD1306 *oled_ssd1306 = nullptr;
SH1106 *oled_sh1106 = nullptr;
LiquidCrystal_I2C *lcd_1602 = nullptr;
LiquidCrystal_I2C *lcd_2004 = nullptr;
const uint8_t lcd_1602_default_i2c_address = 0x3f;
const uint8_t lcd_1602_alternate_i2c_address = 0x27;
const uint8_t lcd_1602_columns = 16;
const uint8_t lcd_1602_rows = 2;
const uint8_t lcd_2004_default_i2c_address = 0x3f;
const uint8_t lcd_2004_alternate_i2c_address = 0x27;
const uint8_t lcd_2004_columns = 20;
const uint8_t lcd_2004_rows = 4;

/*****************************************************************
 * Serial declarations                                           *
 *****************************************************************/
#if defined(ESP8266)
SoftwareSerial serialSDS;
SoftwareSerial *serialGPS;
SoftwareSerial serialNPM;
SoftwareSerial serialIPS;
#endif
#if defined(ESP32)
#define serialSDS (Serial1)
#define serialGPS (&(Serial2))
#define serialNPM (Serial1)
#define serialIPS (Serial1)
#endif

/*****************************************************************
 * DHT declaration                                               *
 *****************************************************************/
DHT dht(ONEWIRE_PIN, DHT_TYPE);

/*****************************************************************
 * HTU21D declaration                                            *
 *****************************************************************/
Adafruit_HTU21DF htu21d;

/*****************************************************************
 * BMP declaration                                               *
 *****************************************************************/
Adafruit_BMP085 bmp;

/*****************************************************************
 * BMP/BME280 declaration                                        *
 *****************************************************************/
BMX280 bmx280;
const uint8_t bmx280_default_i2c_address = 0x77;
const uint8_t bmx280_alternate_i2c_address = 0x76;

/*****************************************************************
 * SHT3x declaration                                             *
 *****************************************************************/
Adafruit_SHT31 sht3x;

/*****************************************************************
 * DS18B20 declaration                                            *
 *****************************************************************/
OneWire oneWire;
DallasTemperature ds18b20(&oneWire);

/*****************************************************************
 * SEN5X declaration                                             *
 *****************************************************************/
SensirionI2CSen5x sen5x;


/*****************************************************************
 * SCD30 declaration                                             *
 *****************************************************************/
SCD30 scd30;

/*****************************************************************
 * SCD4X declaration                                             *
 *****************************************************************/
SCD4x scd4x;

/*****************************************************************
 * GPS declaration                                               *
 *****************************************************************/
TinyGPSPlus gps;

/*****************************************************************
 * Variable Definitions for PPD24NS                              *
 * P1 for PM10 & P2 for PM25                                     *
 *****************************************************************/

boolean trigP1 = false;
boolean trigP2 = false;
unsigned long trigOnP1;
unsigned long trigOnP2;

unsigned long lowpulseoccupancyP1 = 0;
unsigned long lowpulseoccupancyP2 = 0;

bool send_now = false;
bool send_dnms_2nd_interval = false;
unsigned long starttime;
unsigned long time_point_device_start_ms;
unsigned long starttime_SDS;
unsigned long starttime_GPS;
unsigned long starttime_NPM;
unsigned long starttime_IPS;
unsigned long starttime_dnms;
int64_t dnms_2nd_next_wall_ms = 0;
int64_t dnms_1st_start_ms = 0;    // NTP wall-clock ms at alignment-wait end
unsigned long last_mqtt_tx_ms = 0;
unsigned long act_micro;
unsigned long act_milli;
unsigned long last_micro = 0;
unsigned long min_micro = 1000000000;
unsigned long max_micro = 0;

bool is_SDS_running = true;
enum {
  SDS_REPLY_HDR = 10,
  SDS_REPLY_BODY = 8
} SDS_waiting_for;

// To read NPM responses
enum {
  NPM_REPLY_HEADER_16 = 16,
  NPM_REPLY_STATE_16 = 14,
  NPM_REPLY_BODY_16 = 13,
  NPM_REPLY_CHECKSUM_16 = 1
} NPM_waiting_for_16;  //for concentration

enum {
  NPM_REPLY_HEADER_4 = 4,
  NPM_REPLY_STATE_4 = 2,
  NPM_REPLY_CHECKSUM_4 = 1
} NPM_waiting_for_4;  //for change

enum {
  NPM_REPLY_HEADER_5 = 5,
  NPM_REPLY_STATE_5 = 3,
  NPM_REPLY_DATA_5 = 2,
  NPM_REPLY_CHECKSUM_5 = 1
} NPM_waiting_for_5;  //for fan speed

enum {
  NPM_REPLY_HEADER_6 = 6,
  NPM_REPLY_STATE_6 = 4,
  NPM_REPLY_DATA_6 = 3,
  NPM_REPLY_CHECKSUM_6 = 1
} NPM_waiting_for_6;  // for version

enum {
  NPM_REPLY_HEADER_8 = 8,
  NPM_REPLY_STATE_8 = 6,
  NPM_REPLY_BODY_8 = 5,
  NPM_REPLY_CHECKSUM_8 = 1
} NPM_waiting_for_8;  // for temperature/humidity


//ENUM POUR IPS??

String current_state_npm;
String current_th_npm;

bool is_PMS_running = true;
bool is_HPM_running = true;
bool is_NPM_running = false;
bool is_IPS_running;

unsigned long sending_time = 0;
unsigned long last_update_attempt;
int last_update_returncode;
int last_sendData_returncode;

float last_value_BMP_T = -128.0;
float last_value_BMP_P = -1.0;
float last_value_BMX280_T = -128.0;
float last_value_BMX280_P = -1.0;
float last_value_BME280_H = -1.0;
float last_value_DHT_T = -128.0;
float last_value_DHT_H = -1.0;
float last_value_DS18B20_T = -1.0;
float last_value_HTU21D_T = -128.0;
float last_value_HTU21D_H = -1.0;
float last_value_SHT3X_T = -128.0;
float last_value_SHT3X_H = -1.0;
float last_value_SCD30_T = -128.0;
float last_value_SCD30_H = -1.0;
uint16_t last_value_SCD30_CO2 = 0;
uint16_t last_value_SCD30_firmware = 0;
float last_value_SCD4X_T = -128.0;
float last_value_SCD4X_H = -1.0;
uint16_t last_value_SCD4X_CO2 = 0;

uint32_t sds_pm10_sum = 0;
uint32_t sds_pm25_sum = 0;
uint32_t sds_val_count = 0;
uint32_t sds_pm10_max = 0;
uint32_t sds_pm10_min = 20000;
uint32_t sds_pm25_max = 0;
uint32_t sds_pm25_min = 20000;

int pms_pm1_sum = 0;
int pms_pm10_sum = 0;
int pms_pm25_sum = 0;
int pms_val_count = 0;
int pms_pm1_max = 0;
int pms_pm1_min = 20000;
int pms_pm10_max = 0;
int pms_pm10_min = 20000;
int pms_pm25_max = 0;
int pms_pm25_min = 20000;

int hpm_pm10_sum = 0;
int hpm_pm25_sum = 0;
int hpm_val_count = 0;
int hpm_pm10_max = 0;
int hpm_pm10_min = 20000;
int hpm_pm25_max = 0;
int hpm_pm25_min = 20000;

uint32_t npm_pm1_sum = 0;
uint32_t npm_pm10_sum = 0;
uint32_t npm_pm25_sum = 0;
uint32_t npm_pm1_sum_pcs = 0;
uint32_t npm_pm10_sum_pcs = 0;
uint32_t npm_pm25_sum_pcs = 0;
uint16_t npm_val_count = 0;
uint16_t npm_pm1_max = 0;
uint16_t npm_pm1_min = 20000;
uint16_t npm_pm10_max = 0;
uint16_t npm_pm10_min = 20000;
uint16_t npm_pm25_max = 0;
uint16_t npm_pm25_min = 20000;
uint16_t npm_pm1_max_pcs = 0;
uint16_t npm_pm1_min_pcs = 60000;
uint16_t npm_pm10_max_pcs = 0;
uint16_t npm_pm10_min_pcs = 60000;
uint16_t npm_pm25_max_pcs = 0;
uint16_t npm_pm25_min_pcs = 60000;

float ips_pm01_sum = 0;
float ips_pm03_sum = 0;
float ips_pm05_sum = 0;
float ips_pm1_sum = 0;
float ips_pm25_sum = 0;
float ips_pm5_sum = 0;
float ips_pm10_sum = 0;
unsigned long ips_pm01_sum_pcs = 0;
unsigned long ips_pm03_sum_pcs = 0;
unsigned long ips_pm05_sum_pcs = 0;
unsigned long ips_pm1_sum_pcs = 0;
unsigned long ips_pm25_sum_pcs = 0;
unsigned long ips_pm5_sum_pcs = 0;
unsigned long ips_pm10_sum_pcs = 0;
uint16_t ips_val_count = 0;
float ips_pm01_max = 0;
float ips_pm01_min = 200;
float ips_pm03_max = 0;
float ips_pm03_min = 200;
float ips_pm05_max = 0;
float ips_pm05_min = 200;
float ips_pm1_max = 0;
float ips_pm1_min = 200;
float ips_pm25_max = 0;
float ips_pm25_min = 200;
float ips_pm5_max = 0;
float ips_pm5_min = 200;
float ips_pm10_max = 0;
float ips_pm10_min = 200;
unsigned long ips_pm01_max_pcs = 0;
unsigned long ips_pm01_min_pcs = 4000000000;
unsigned long ips_pm03_max_pcs = 0;
unsigned long ips_pm03_min_pcs = 4000000000;
unsigned long ips_pm05_max_pcs = 0;
unsigned long ips_pm05_min_pcs = 4000000000;
unsigned long ips_pm1_max_pcs = 0;
unsigned long ips_pm1_min_pcs = 4000000000;
unsigned long ips_pm25_max_pcs = 0;
unsigned long ips_pm25_min_pcs = 4000000000;
unsigned long ips_pm5_max_pcs = 0;
unsigned long ips_pm5_min_pcs = 4000000000;
unsigned long ips_pm10_max_pcs = 0;
unsigned long ips_pm10_min_pcs = 4000000000;

float last_value_SEN5X_P0 = -1.0;
float last_value_SEN5X_P1 = -1.0;
float last_value_SEN5X_P2 = -1.0;
float last_value_SEN5X_P4 = -1.0;
float last_value_SEN5X_N05 = -1.0;
float last_value_SEN5X_N1 = -1.0;
float last_value_SEN5X_N25 = -1.0;
float last_value_SEN5X_N4 = -1.0;
float last_value_SEN5X_N10 = -1.0;
float last_value_SEN5X_TS = -1.0;
float last_value_SEN5X_T = -128.0;
float last_value_SEN5X_H = -1.0;
float last_value_SEN5X_VOC = -1.0;
float last_value_SEN5X_NOX = -1.0;
float value_SEN5X_P0 = 0.0;
float value_SEN5X_P1 = 0.0;
float value_SEN5X_P2 = 0.0;
float value_SEN5X_P4 = 0.0;
float value_SEN5X_N05 = 0.0;
float value_SEN5X_N1 = 0.0;
float value_SEN5X_N25 = 0.0;
float value_SEN5X_N4 = 0.0;
float value_SEN5X_N10 = 0.0;
float value_SEN5X_TS = 0.0;
float value_SEN5X_T = 0.0;
float value_SEN5X_H = 0.0;
float value_SEN5X_VOC = 0.0;
float value_SEN5X_NOX = 0.0;
float sen5x_temp;

uint16_t SEN5X_measurement_count = 0;
unsigned long SEN5X_read_counter = 0;
unsigned long SEN5X_read_error_counter = 0;
unsigned long SEN5X_read_timer = 0;
bool sen5x_init_failed = false;

float last_value_SPS30_P0 = -1.0;
float last_value_SPS30_P1 = -1.0;
float last_value_SPS30_P2 = -1.0;
float last_value_SPS30_P4 = -1.0;
float last_value_SPS30_N05 = -1.0;
float last_value_SPS30_N1 = -1.0;
float last_value_SPS30_N25 = -1.0;
float last_value_SPS30_N4 = -1.0;
float last_value_SPS30_N10 = -1.0;
float last_value_SPS30_TS = -1.0;
float value_SPS30_P0 = 0.0;
float value_SPS30_P1 = 0.0;
float value_SPS30_P2 = 0.0;
float value_SPS30_P4 = 0.0;
float value_SPS30_N05 = 0.0;
float value_SPS30_N1 = 0.0;
float value_SPS30_N25 = 0.0;
float value_SPS30_N4 = 0.0;
float value_SPS30_N10 = 0.0;
float value_SPS30_TS = 0.0;

uint16_t SPS30_measurement_count = 0;
unsigned long SPS30_read_counter = 0;
unsigned long SPS30_read_error_counter = 0;
unsigned long SPS30_read_timer = 0;
bool sps30_init_failed = false;

float last_value_PPD_P1 = -1.0;
float last_value_PPD_P2 = -1.0;
float last_value_SDS_P1 = -1.0;
float last_value_SDS_P2 = -1.0;
float last_value_PMS_P0 = -1.0;
float last_value_PMS_P1 = -1.0;
float last_value_PMS_P2 = -1.0;
float last_value_HPM_P1 = -1.0;
float last_value_HPM_P2 = -1.0;
float last_value_NPM_P0 = -1.0;
float last_value_NPM_P1 = -1.0;
float last_value_NPM_P2 = -1.0;
float last_value_NPM_N1 = -1.0;
float last_value_NPM_N10 = -1.0;
float last_value_NPM_N25 = -1.0;

float last_value_IPS_P0 = -1.0;   //PM1
float last_value_IPS_P1 = -1.0;   //PM10
float last_value_IPS_P2 = -1.0;   //PM2.5
float last_value_IPS_P01 = -1.0;  //PM0.1
float last_value_IPS_P03 = -1.0;  //PM0.3 //ATTENTION P4 = PM4 POUR SPS30
float last_value_IPS_P05 = -1.0;  //PM0.5
float last_value_IPS_P5 = -1.0;   //PM5
float last_value_IPS_N1 = -1.0;
float last_value_IPS_N10 = -1.0;
float last_value_IPS_N25 = -1.0;
float last_value_IPS_N01 = -1.0;
float last_value_IPS_N03 = -1.0;  //ATTENTION P4 = PM4 POUR SPS30
float last_value_IPS_N05 = -1.0;
float last_value_IPS_N5 = -1.0;

float last_value_GPS_alt = -1000.0;
double last_value_GPS_lat = -200.0;
double last_value_GPS_lon = -200.0;
String last_value_GPS_timestamp;
String last_data_string;
int last_signal_strength;
int last_disconnect_reason;

String esp_chipid;
String esp_mac_id;
String last_value_SDS_version;
String last_value_NPM_version;
String last_value_IPS_version;
String last_value_DNMS_version;
String last_value_SPS30_version;
String last_value_SCD4X_serialNumber;
String last_value_SEN5X_serialNumber;
String last_value_SEN5X_type;
String last_value_SEN5X_hw;
String last_value_SEN5X_sw;

unsigned long SDS_error_count;
unsigned long NPM_error_count;
unsigned long IPS_error_count;
unsigned long WiFi_error_count;
unsigned long DNMS_error_count;
unsigned long SCD30_read_error_counter;
unsigned long SCD4X_read_error_counter;
uint16_t      mqtt_error_count;
uint16_t      g_tx_2nd_drop_count;

unsigned long last_page_load = millis();

bool wificonfig_loop = false;
uint8_t sntp_time_set;

unsigned long count_sends = 0;
unsigned long count_sends_2nd = 0;
unsigned long last_display_millis = 0;
uint8_t next_display_count = 0;

struct TxEntry {
  bool   in_use;
  String data;
  struct timeval saved_dnms_now;
};
static TxEntry g_tx_buf[3];

struct TxEntry2nd {
  bool   in_use;
  String data;
  struct timeval saved_dnms_2nd_now;
};
#if defined(ESP8266)
static TxEntry2nd g_tx_2nd_buf[20];   // 20 s WiFi-down buffer at 1 Hz
#else
static TxEntry2nd g_tx_2nd_buf[30];   // 30 s WiFi-down buffer at 1 Hz
#endif

/* Non-blocking send queue: jobs enqueued here, one processed per loop() iteration
   so the 2nd-interval check runs between sends and no measurements are missed. */
#define TX_QUEUE_SIZE 32

struct TxJob {
  uint8_t logger_id;
  int     pin;
  String  host;
  String  url;
  String  payload;
  uint8_t retry_count;
};
static TxJob tx_q[TX_QUEUE_SIZE];
static int   tx_q_head = 0;
static int   tx_q_tail = 0;
static int   tx_q_len  = 0;

static bool enqueue_tx_job(uint8_t logger_id, String payload, int pin,
                            const char *host, const char *url) {
  if (tx_q_len >= TX_QUEUE_SIZE) {
    debug_outln_error(F("TX queue full, dropping send"));
    return false;
  }
  TxJob &j    = tx_q[tx_q_head];
  j.logger_id = logger_id;
  j.pin       = pin;
  j.host      = String(FPSTR(host));
  j.url       = String(FPSTR(url));
  j.payload     = std::move(payload);
  j.retry_count = 0;
  tx_q_head     = (tx_q_head + 1) % TX_QUEUE_SIZE;
  ++tx_q_len;
  return true;
}

struct struct_wifiInfo {
  char ssid[LEN_WLANSSID];
  uint8_t encryptionType;
  int32_t RSSI;
  int32_t channel;
#if defined(ESP8266)
  bool isHidden;
  uint8_t unused[3];
#endif
};

struct tm *ts_wait;

struct struct_wifiInfo *wifiInfo;
uint8_t count_wifiInfo;

IPAddress addr_static_ip;
IPAddress addr_static_subnet;
IPAddress addr_static_gateway;
IPAddress addr_static_dns;

#define msSince(timestamp_before) (act_milli - (timestamp_before))

const char data_first_part[] PROGMEM = "{\"software_version\": \"" SOFTWARE_VERSION_STR "\", \"sensordatavalues\":[";
const char JSON_SENSOR_DATA_VALUES[] PROGMEM = "sensordatavalues";

/*****************************************************************
 * display values                                                *
 *****************************************************************/
static void display_debug(const String &text1, const String &text2) {
  debug_outln_info(F("output debug text to displays..."));
  if (oled_ssd1306) {
    oled_ssd1306->clear();
    oled_ssd1306->displayOn();
    oled_ssd1306->setTextAlignment(TEXT_ALIGN_LEFT);
    oled_ssd1306->drawString(0, 12, text1);
    oled_ssd1306->drawString(0, 24, text2);
    oled_ssd1306->display();
  }
  if (oled_sh1106) {
    oled_sh1106->clear();
    oled_sh1106->displayOn();
    oled_sh1106->setTextAlignment(TEXT_ALIGN_LEFT);
    oled_sh1106->drawString(0, 12, text1);
    oled_sh1106->drawString(0, 24, text2);
    oled_sh1106->display();
  }
  if (lcd_1602) {
    lcd_1602->clear();
    lcd_1602->setCursor(0, 0);
    lcd_1602->print(text1);
    lcd_1602->setCursor(0, 1);
    lcd_1602->print(text2);
  }
  if (lcd_2004) {
    lcd_2004->clear();
    lcd_2004->setCursor(0, 0);
    lcd_2004->print(text1);
    lcd_2004->setCursor(0, 1);
    lcd_2004->print(text2);
  }
}

/*****************************************************************
 * read SDS011 sensor serial and firmware date                   *
 *****************************************************************/
static String SDS_version_date() {

  if (cfg::sds_read && !last_value_SDS_version.length()) {
    debug_outln_verbose(FPSTR(DBG_TXT_START_READING), FPSTR(DBG_TXT_SDS011_VERSION_DATE));
    is_SDS_running = SDS_cmd(PmSensorCmd::Start);
    delay(250);
#if defined(ESP8266)
//		serialSDS.perform_work();
#endif
    serialSDS.flush();
    // Query Version/Date
    SDS_rawcmd(0x07, 0x00, 0x00);
    delay(400);
    const constexpr uint8_t header_cmd_response[2] = { 0xAA, 0xC5 };
    while (serialSDS.find(header_cmd_response, sizeof(header_cmd_response))) {
      uint8_t data[8];
      unsigned r = serialSDS.readBytes(data, sizeof(data));
      if (r == sizeof(data) && data[0] == 0x07 && SDS_checksum_valid(data)) {
        char tmp[20];
        snprintf_P(tmp, sizeof(tmp), PSTR("%02d-%02d-%02d(%02x%02x)"),
                   data[1], data[2], data[3], data[4], data[5]);
        last_value_SDS_version = tmp;
        break;
      }
    }
    debug_outln_verbose(FPSTR(DBG_TXT_END_READING), FPSTR(DBG_TXT_SDS011_VERSION_DATE));
  }

  return last_value_SDS_version;
}

/*****************************************************************
 * read Next PM sensor serial and firmware date                   *
 *****************************************************************/

static uint8_t NPM_get_state() {
  uint8_t result;
  NPM_waiting_for_4 = NPM_REPLY_HEADER_4;
  debug_outln_info(F("State NPM..."));
  NPM_cmd(PmSensorCmd2::State);

  while (!serialNPM.available()) {
    debug_outln("Wait for Serial...", DEBUG_MAX_INFO);
  }

  while (serialNPM.available() >= NPM_waiting_for_4) {
    const uint8_t constexpr header[2] = { 0x81, 0x16 };
    uint8_t state[1];
    uint8_t checksum[1];
    uint8_t test[4];

    switch (NPM_waiting_for_4) {
      case NPM_REPLY_HEADER_4:
        if (serialNPM.find(header, sizeof(header)))
          NPM_waiting_for_4 = NPM_REPLY_STATE_4;
        break;
      case NPM_REPLY_STATE_4:
        serialNPM.readBytes(state, sizeof(state));
        NPM_state(state[0]);
        result = state[0];
        NPM_waiting_for_4 = NPM_REPLY_CHECKSUM_4;
        break;
      case NPM_REPLY_CHECKSUM_4:
        serialNPM.readBytes(checksum, sizeof(checksum));
        memcpy(test, header, sizeof(header));
        memcpy(&test[sizeof(header)], state, sizeof(state));
        memcpy(&test[sizeof(header) + sizeof(state)], checksum, sizeof(checksum));
        NPM_data_reader(test, 4);
        NPM_waiting_for_4 = NPM_REPLY_HEADER_4;
        if (NPM_checksum_valid_4(test)) {
          debug_outln_info(F("Checksum OK..."));
        }
        break;
    }
  }
  return result;
}

static bool NPM_start_stop() {
  bool result;
  NPM_waiting_for_4 = NPM_REPLY_HEADER_4;
  debug_outln_info(F("Switch start/stop NPM..."));
  NPM_cmd(PmSensorCmd2::Change);

  while (!serialNPM.available()) {
    debug_outln("Wait for Serial...", DEBUG_MAX_INFO);
  }

  while (serialNPM.available() >= NPM_waiting_for_4) {
    const uint8_t constexpr header[2] = { 0x81, 0x15 };
    uint8_t state[1];
    uint8_t checksum[1];
    uint8_t test[4];

    switch (NPM_waiting_for_4) {
      case NPM_REPLY_HEADER_4:
        if (serialNPM.find(header, sizeof(header)))
          NPM_waiting_for_4 = NPM_REPLY_STATE_4;
        break;
      case NPM_REPLY_STATE_4:
        serialNPM.readBytes(state, sizeof(state));
        NPM_state(state[0]);

        if (bitRead(state[0], 0) == 0) {
          debug_outln_info(F("NPM start..."));
          result = true;
        } else if (bitRead(state[0], 0) == 1) {
          debug_outln_info(F("NPM stop..."));
          result = false;
        } else {
          result = !is_NPM_running;  //DANGER BECAUSE NON INITIALISED
        }
        NPM_waiting_for_4 = NPM_REPLY_CHECKSUM_4;
        break;
      case NPM_REPLY_CHECKSUM_4:
        serialNPM.readBytes(checksum, sizeof(checksum));
        memcpy(test, header, sizeof(header));
        memcpy(&test[sizeof(header)], state, sizeof(state));
        memcpy(&test[sizeof(header) + sizeof(state)], checksum, sizeof(checksum));
        NPM_data_reader(test, 4);
        NPM_waiting_for_4 = NPM_REPLY_HEADER_4;
        if (NPM_checksum_valid_4(test)) {
          debug_outln_info(F("Checksum OK..."));
        }
        break;
    }
  }
  return result;  //ATTENTION
}

static String NPM_version_date() {
  //debug_outln_verbose(FPSTR(DBG_TXT_START_READING), FPSTR(DBG_TXT_NPM_VERSION_DATE));
  delay(250);
  NPM_waiting_for_6 = NPM_REPLY_HEADER_6;
  debug_outln_info(F("Version NPM..."));
  NPM_cmd(PmSensorCmd2::Version);

  while (!serialNPM.available()) {
    debug_outln("Wait for Serial...", DEBUG_MAX_INFO);
  }

  while (serialNPM.available() >= NPM_waiting_for_6) {
    const uint8_t constexpr header[2] = { 0x81, 0x17 };
    uint8_t state[1];
    uint8_t data[2];
    uint8_t checksum[1];
    uint8_t test[6];

    switch (NPM_waiting_for_6) {
      case NPM_REPLY_HEADER_6:
        if (serialNPM.find(header, sizeof(header)))
          NPM_waiting_for_6 = NPM_REPLY_STATE_6;
        break;
      case NPM_REPLY_STATE_6:
        serialNPM.readBytes(state, sizeof(state));
        NPM_state(state[0]);
        NPM_waiting_for_6 = NPM_REPLY_DATA_6;
        break;
      case NPM_REPLY_DATA_6:
        if (serialNPM.readBytes(data, sizeof(data)) == sizeof(data)) {
          NPM_data_reader(data, 2);
          uint16_t NPMversion = word(data[0], data[1]);
          last_value_NPM_version = String(NPMversion);
          //debug_outln_verbose(FPSTR(DBG_TXT_END_READING), FPSTR(DBG_TXT_NPM_VERSION_DATE));
          debug_outln_info(F("Next PM Firmware: "), last_value_NPM_version);
        }
        NPM_waiting_for_6 = NPM_REPLY_CHECKSUM_6;
        break;
      case NPM_REPLY_CHECKSUM_6:
        serialNPM.readBytes(checksum, sizeof(checksum));
        memcpy(test, header, sizeof(header));
        memcpy(&test[sizeof(header)], state, sizeof(state));
        memcpy(&test[sizeof(header) + sizeof(state)], data, sizeof(data));
        memcpy(&test[sizeof(header) + sizeof(state) + sizeof(data)], checksum, sizeof(checksum));
        NPM_data_reader(test, 6);
        NPM_waiting_for_6 = NPM_REPLY_HEADER_6;
        if (NPM_checksum_valid_6(test)) {
          debug_outln_info(F("Checksum OK..."));
        }
        break;
    }
  }
  return last_value_NPM_version;
}

static void NPM_fan_speed() {

  NPM_waiting_for_5 = NPM_REPLY_HEADER_5;
  debug_outln_info(F("Set fan speed to 50 %..."));
  NPM_cmd(PmSensorCmd2::Speed);

  while (!serialNPM.available()) {
    debug_outln("Wait for Serial...", DEBUG_MAX_INFO);
  }

  while (serialNPM.available() >= NPM_waiting_for_5) {
    const uint8_t constexpr header[2] = { 0x81, 0x21 };
    uint8_t state[1];
    uint8_t data[1];
    uint8_t checksum[1];
    uint8_t test[5];

    switch (NPM_waiting_for_5) {
      case NPM_REPLY_HEADER_5:
        if (serialNPM.find(header, sizeof(header)))
          NPM_waiting_for_5 = NPM_REPLY_STATE_5;
        break;
      case NPM_REPLY_STATE_5:
        serialNPM.readBytes(state, sizeof(state));
        NPM_state(state[0]);
        NPM_waiting_for_5 = NPM_REPLY_DATA_5;
        break;
      case NPM_REPLY_DATA_5:
        if (serialNPM.readBytes(data, sizeof(data)) == sizeof(data)) {
          NPM_data_reader(data, 1);
        }
        NPM_waiting_for_5 = NPM_REPLY_CHECKSUM_5;
        break;
      case NPM_REPLY_CHECKSUM_5:
        serialNPM.readBytes(checksum, sizeof(checksum));
        memcpy(test, header, sizeof(header));
        memcpy(&test[sizeof(header)], state, sizeof(state));
        memcpy(&test[sizeof(header) + sizeof(state)], data, sizeof(data));
        memcpy(&test[sizeof(header) + sizeof(state) + sizeof(data)], checksum, sizeof(checksum));
        NPM_data_reader(test, 5);
        NPM_waiting_for_5 = NPM_REPLY_HEADER_5;
        if (NPM_checksum_valid_5(test)) {
          debug_outln_info(F("Checksum OK..."));
        }
        break;
    }
  }
}



static String NPM_temp_humi() {
  uint16_t NPM_temp;
  uint16_t NPM_humi;
  NPM_waiting_for_8 = NPM_REPLY_HEADER_8;
  debug_outln_info(F("Temperature/Humidity in Next PM..."));
  NPM_cmd(PmSensorCmd2::Temphumi);
  while (!serialNPM.available()) {
    debug_outln("Wait for Serial...", DEBUG_MAX_INFO);
  }

  while (serialNPM.available() >= NPM_waiting_for_8) {
    const uint8_t constexpr header[2] = { 0x81, 0x14 };
    uint8_t state[1];
    uint8_t data[4];
    uint8_t checksum[1];
    uint8_t test[8];

    switch (NPM_waiting_for_8) {
      case NPM_REPLY_HEADER_8:
        if (serialNPM.find(header, sizeof(header)))
          NPM_waiting_for_8 = NPM_REPLY_STATE_8;
        break;
      case NPM_REPLY_STATE_8:
        serialNPM.readBytes(state, sizeof(state));
        NPM_state(state[0]);
        NPM_waiting_for_8 = NPM_REPLY_BODY_8;
        break;
      case NPM_REPLY_BODY_8:
        if (serialNPM.readBytes(data, sizeof(data)) == sizeof(data)) {
          NPM_data_reader(data, 4);
          NPM_temp = word(data[0], data[1]);
          NPM_humi = word(data[2], data[3]);
          debug_outln_verbose(F("Temperature (°C): "), String(NPM_temp / 100.0f));
          debug_outln_verbose(F("Relative humidity (%): "), String(NPM_humi / 100.0f));
        }
        NPM_waiting_for_8 = NPM_REPLY_CHECKSUM_8;
        break;
      case NPM_REPLY_CHECKSUM_16:
        serialNPM.readBytes(checksum, sizeof(checksum));
        memcpy(test, header, sizeof(header));
        memcpy(&test[sizeof(header)], state, sizeof(state));
        memcpy(&test[sizeof(header) + sizeof(state)], data, sizeof(data));
        memcpy(&test[sizeof(header) + sizeof(state) + sizeof(data)], checksum, sizeof(checksum));
        NPM_data_reader(test, 8);
        if (NPM_checksum_valid_8(test))
          debug_outln_info(F("Checksum OK..."));
        NPM_waiting_for_8 = NPM_REPLY_HEADER_8;
        break;
    }
  }
  return String(NPM_temp / 100.0f) + " / " + String(NPM_humi / 100.0f);
}


/*****************************************************************
 * read IPS-7100 sensor serial and firmware date                   *
*****************************************************************/

static String IPS_version_date() {
  debug_outln_info(F("Version IPS..."));
  String serial_data;

  IPS_cmd(PmSensorCmd3::Reset);

  if (serialIPS.available() > 0) {
    serial_data = serialIPS.readString();
    //Debug.println(serial_data);
  }

  int index1 = serial_data.indexOf("VERSION_NUMBER ");
  int index2 = serial_data.indexOf("\nSERIAL_NUMBER ");
  int index3 = serial_data.indexOf("\nD:");

  String version_ips = serial_data.substring(index1 + 15, index2 - 1);
  String serial_ips = serial_data.substring(index2 + 15, index3 - 1);

  last_value_IPS_version = version_ips + "/" + serial_ips;

  debug_outln_info(F("IPS-7100 Version/Serial Number: "), last_value_IPS_version);

  return last_value_IPS_version;
}

/*****************************************************************
 * read SEN5X sensor serial and firmware date                    *
 *****************************************************************/

unsigned char SEN5X_type[6];

#define MAXBUF_REQUIREMENT 48

#if (defined(I2C_BUFFER_LENGTH) && (I2C_BUFFER_LENGTH >= MAXBUF_REQUIREMENT)) || (defined(BUFFER_LENGTH) && BUFFER_LENGTH >= MAXBUF_REQUIREMENT)
#define USE_PRODUCT_INFO
#endif

void printModuleVersions() {
  uint16_t error;
  char errorMessage[256];

  unsigned char productName[32];
  int8_t productNameSize = 32;

  error = sen5x.getProductName(productName, productNameSize);

  if (error) {
    Debug.print("Error trying to execute getProductName(): ");
    errorToString(error, errorMessage, 256);
    Debug.println(errorMessage);
    sen5x_init_failed = true;
    return;
  } else {
    Debug.print("ProductName:");
    Debug.println((char *)productName);
    memcpy(SEN5X_type, productName, 6);
  }

  uint8_t firmwareMajor;
  uint8_t firmwareMinor;
  bool firmwareDebug;
  uint8_t hardwareMajor;
  uint8_t hardwareMinor;
  uint8_t protocolMajor;
  uint8_t protocolMinor;

  error = sen5x.getVersion(firmwareMajor, firmwareMinor, firmwareDebug,
                           hardwareMajor, hardwareMinor, protocolMajor,
                           protocolMinor);
  if (error) {
    Debug.print("Error trying to execute getVersion(): ");
    errorToString(error, errorMessage, 256);
    Debug.println(errorMessage);
    sen5x_init_failed = true;
    return;
  } else {
    Debug.print("Firmware: ");
    Debug.print(firmwareMajor);
    Debug.print(".");
    Debug.print(firmwareMinor);
    Debug.print(", ");
    last_value_SEN5X_sw = String(firmwareMajor) + String(".") + String(firmwareMinor);

    Debug.print("Hardware: ");
    Debug.print(hardwareMajor);
    Debug.print(".");
    Debug.println(hardwareMinor);
    last_value_SEN5X_hw = String(hardwareMajor) + String(".") + String(hardwareMinor);
  }
}

void printSerialNumber() {
  uint16_t error;
  char errorMessage[256];
  unsigned char serialNumber[32];
  uint8_t serialNumberSize = 32;

  error = sen5x.getSerialNumber(serialNumber, serialNumberSize);
  if (error) {
    Debug.print("Error trying to execute getSerialNumber(): ");
    errorToString(error, errorMessage, 256);
    Debug.println(errorMessage);
    sen5x_init_failed = true;
    return;
  } else {
    Debug.print("SerialNumber:");
    Debug.println((char *)serialNumber);
    last_value_SEN5X_serialNumber = String((char *)serialNumber);
  }
}


/*****************************************************************
 * disable unneeded NMEA sentences, TinyGPS++ needs GGA, RMC     *
 *****************************************************************/
static void disable_unneeded_nmea() {
  serialGPS->println(F("$PUBX,40,GLL,0,0,0,0*5C"));  // Geographic position, latitude / longitude
                                                     //	serialGPS->println(F("$PUBX,40,GGA,0,0,0,0*5A"));       // Global Positioning System Fix Data
  serialGPS->println(F("$PUBX,40,GSA,0,0,0,0*4E"));  // GPS DOP and active satellites
                                                     //	serialGPS->println(F("$PUBX,40,RMC,0,0,0,0*47"));       // Recommended minimum specific GPS/Transit data
  serialGPS->println(F("$PUBX,40,GSV,0,0,0,0*59"));  // GNSS satellites in view
  serialGPS->println(F("$PUBX,40,VTG,0,0,0,0*5E"));  // Track made good and ground speed
}

/*****************************************************************
 * read config from LittleFS                                       *
 *****************************************************************/

/* backward compatibility for the times when we stored booleans as strings */
static bool boolFromJSON(const JsonDocument &json, const __FlashStringHelper *key) {
  if (json[key].is<const char *>()) {
    return !strcmp_P(json[key].as<const char *>(), PSTR("true"));
  }
  return json[key].as<bool>();
}



static void readConfig(bool oldconfig = false) {
  bool rewriteConfig = false;

  String cfgName(F("/config.json"));
  if (oldconfig) {
    cfgName += F(".old");
  }

#pragma GCC diagnostic push
#pragma GCC diagnostic ignored "-Wdeprecated-declarations"
  File configFile = LittleFS.open(cfgName, "r");
  if (!configFile) {
    if (!oldconfig) {
      return readConfig(true /* oldconfig */);
    }

    debug_outln_error(F("failed to open config file."));
    return;
  }

  debug_outln_info(F("opened config file..."));
  DynamicJsonDocument json(JSON_BUFFER_SIZE);
  DeserializationError err = deserializeJson(json, configFile.readString());
  configFile.close();
#pragma GCC diagnostic pop

  if (!err) {
    //serializeJsonPretty(json, Debug);
    debug_outln_info(F("parsed json..."));
    for (unsigned e = 0; e < sizeof(configShape) / sizeof(configShape[0]); ++e) {
      ConfigShapeEntry c;
      memcpy_P(&c, &configShape[e], sizeof(ConfigShapeEntry));
      if (json[c.cfg_key()].isNull()) {
        continue;
      }
      switch (c.cfg_type) {
        case Config_Type_Bool:
          *(c.cfg_val.as_bool) = boolFromJSON(json, c.cfg_key());
          break;
        case Config_Type_UInt:
        case Config_Type_Time:
          *(c.cfg_val.as_uint) = json[c.cfg_key()].as<unsigned int>();
          break;
        case Config_Type_String:
        case Config_Type_Password:
          strncpy(c.cfg_val.as_str, json[c.cfg_key()].as<const char *>(), c.cfg_len);
          c.cfg_val.as_str[c.cfg_len] = '\0';
          break;
      };
    }
    String writtenVersion(json["SOFTWARE_VERSION"].as<const char *>());
    if (writtenVersion.length() && writtenVersion[0] == 'N' && SOFTWARE_VERSION != writtenVersion) {
      debug_outln_info(F("Rewriting old config from: "), writtenVersion);
      // would like to do that, but this would wipe firmware.old which the two stage loader
      // might still need
      // LittleFS.format();
      rewriteConfig = true;
    }
    /*  make it possible to set measurement interval down to 1 second
 *  this is not inline with the Sensor.Community interval but may be necessary for other
 *  measurements
 *  
		if (cfg::sending_intervall_ms < READINGTIME_SDS_MS)
		{
			cfg::sending_intervall_ms = READINGTIME_SDS_MS;
		}
*/
    if (strcmp_P(cfg::senseboxid, PSTR("00112233445566778899aabb")) == 0) {
      cfg::senseboxid[0] = '\0';
      cfg::send2sensemap = false;
      rewriteConfig = true;
    }
    if (strlen(cfg::measurement_name_influx) == 0) {
      strcpy_P(cfg::measurement_name_influx, MEASUREMENT_NAME_INFLUX);
      rewriteConfig = true;
    }
    if (strcmp_P(cfg::host_influx, PSTR("api.luftdaten.info")) == 0) {
      cfg::host_influx[0] = '\0';
      cfg::send2influx = false;
      rewriteConfig = true;
    }
    if (boolFromJSON(json, F("pm24_read")) || boolFromJSON(json, F("pms32_read"))) {
      cfg::pms_read = true;
      rewriteConfig = true;
    }
    if (boolFromJSON(json, F("bmp280_read")) || boolFromJSON(json, F("bme280_read"))) {
      cfg::bmx280_read = true;
      rewriteConfig = true;
    }
  } else {
    debug_outln_error(F("failed to load json config"));

    if (!oldconfig) {
      return readConfig(true /* oldconfig */);
    }
  }

  if (rewriteConfig) {
    writeConfig();
  }
}



static void init_config() {

  debug_outln_info(F("mounting FS..."));

#pragma GCC diagnostic push
#pragma GCC diagnostic ignored "-Wdeprecated-declarations"

#if defined(ESP32)
  bool spiffs_begin_ok = SPIFFS.begin(FORMAT_SPIFFS_IF_FAILED);
#else
  bool LittleFS_begin_ok = LittleFS.begin();
#endif

#pragma GCC diagnostic pop

  if (!LittleFS_begin_ok) {
    debug_outln_error(F("failed to mount FS"));
    return;
  }
  readConfig();
}

/*****************************************************************
 * write config to LittleFS                                        *
 *****************************************************************/
static bool writeConfig() {
  JsonDocument json;
  debug_outln_info(F("Saving config..."));
  json["SOFTWARE_VERSION"] = SOFTWARE_VERSION;

  if (cfg::send2dusti || cfg::send2madavi) {
    cfg::sending_intervall_ms = sc_sending_intervall_ms;
  }

  for (unsigned e = 0; e < sizeof(configShape) / sizeof(configShape[0]); ++e) {
    ConfigShapeEntry c;
    memcpy_P(&c, &configShape[e], sizeof(ConfigShapeEntry));
    switch (c.cfg_type) {
      case Config_Type_Bool:
        json[c.cfg_key()].set(*c.cfg_val.as_bool);
        break;
      case Config_Type_UInt:
      case Config_Type_Time:
        json[c.cfg_key()].set(*c.cfg_val.as_uint);
        break;
      case Config_Type_Password:
      case Config_Type_String:
        json[c.cfg_key()].set(c.cfg_val.as_str);
        break;
    };
  }

#pragma GCC diagnostic push
#pragma GCC diagnostic ignored "-Wdeprecated-declarations"

  LittleFS.remove(F("/config.json.old"));
  LittleFS.rename(F("/config.json"), F("/config.json.old"));

  File configFile = LittleFS.open(F("/config.json"), "w");
  if (configFile) {
    serializeJson(json, configFile);
    delay(1);
    configFile.close();

    debug_outln_info(F("Config written successfully."));
  } else {
    debug_outln_error(F("failed to open config file for writing"));
    return false;
  }

#pragma GCC diagnostic pop

  return true;
}

/*****************************************************************
 * Prepare information for data Loggers                          *
 *****************************************************************/
static void createLoggerConfigs() {
#if defined(ESP8266)
  auto new_session = []() {
    return new BearSSL::Session;
  };
#else
  auto new_session = []() {
    return nullptr;
  };
#endif
  if (cfg::send2dusti) {
    loggerConfigs[LoggerSensorCommunity].destport = 80;
    if (cfg::ssl_dusti) {
      loggerConfigs[LoggerSensorCommunity].destport = 443;
      loggerConfigs[LoggerSensorCommunity].session = new_session();
    }
  }
  loggerConfigs[LoggerMadavi].destport = PORT_MADAVI;
  if (cfg::send2madavi && cfg::ssl_madavi) {
    loggerConfigs[LoggerMadavi].destport = 443;
    loggerConfigs[LoggerMadavi].session = new_session();
  }
  loggerConfigs[LoggerSensemap].destport = PORT_SENSEMAP;
  loggerConfigs[LoggerSensemap].session = new_session();
  loggerConfigs[LoggerFSapp].destport = PORT_FSAPP;
  loggerConfigs[Loggeraircms].destport = PORT_AIRCMS;
  loggerConfigs[LoggerInflux].destport = cfg::port_influx;
  if (cfg::send2influx && cfg::ssl_influx) {
    loggerConfigs[LoggerInflux].session = new_session();
  }
  loggerConfigs[LoggerCustom].destport = cfg::port_custom;
  if (cfg::send2custom && (cfg::ssl_custom || (cfg::port_custom == 443))) {
    loggerConfigs[LoggerCustom].session = new_session();
  }

  //  loggerConfigs[LoggerMQTT].destport = cfg::port_mqtt;
}

/*****************************************************************
 * dew point helper function                                     *
 *****************************************************************/
static float dew_point(const float temperature, const float humidity) {
  float dew_temp;
  const float k2 = 17.62;
  const float k3 = 243.12;

  dew_temp = k3 * (((k2 * temperature) / (k3 + temperature)) + log(humidity / 100.0f)) / (((k2 * k3) / (k3 + temperature)) - log(humidity / 100.0f));

  return dew_temp;
}

/*****************************************************************
 * dew point helper function                                     *
 *****************************************************************/
static float pressure_at_sealevel(const float temperature, const float pressure) {
  float pressure_at_sealevel;

  pressure_at_sealevel = pressure * pow(((temperature + 273.15f) / (temperature + 273.15f + (0.0065f * readCorrectionOffset(cfg::height_above_sealevel)))), -5.255f);

  return pressure_at_sealevel;
}

/*****************************************************************
 * html helper functions                                         *
 *****************************************************************/
static void start_html_page(String &page_content, const String &title) {
  last_page_load = millis();

  RESERVE_STRING(s, LARGE_STR);
  s = FPSTR(WEB_PAGE_HEADER);
  s.replace("{t}", title);
  server.setContentLength(CONTENT_LENGTH_UNKNOWN);
  server.send(200, FPSTR(TXT_CONTENT_TYPE_TEXT_HTML), s);

  server.sendContent_P(WEB_PAGE_HEADER_HEAD);

  s = FPSTR(WEB_PAGE_HEADER_BODY);
  s.replace("{t}", title);
  if (title != " ") {
    s.replace("{n}", F("&raquo;"));
  } else {
    s.replace("{n}", emptyString);
  }
  s.replace("{id}", esp_chipid);
  s.replace("{macid}", esp_mac_id);
  s.replace("{mac}", WiFi.macAddress());
  page_content += s;
}

static void end_html_page(String &page_content) {
  if (page_content.length()) {
    server.sendContent(page_content);
  }
  server.sendContent_P(WEB_PAGE_FOOTER);
}

static void add_form_input(String &page_content, const ConfigShapeId cfgid, const __FlashStringHelper *info, const int length) {
  RESERVE_STRING(s, MED_STR);
  s = F("<tr>"
        "<td title='[&lt;= {l}]'>{i}:&nbsp;</td>"
        "<td style='width:{l}em'>"
        "<input type='{t}' name='{n}' id='{n}' placeholder='{i}' value='{v}' maxlength='{l}'/>"
        "</td></tr>");
  String t_value;
  ConfigShapeEntry c;
  memcpy_P(&c, &configShape[cfgid], sizeof(ConfigShapeEntry));
  switch (c.cfg_type) {
    case Config_Type_UInt:
      t_value = String(*c.cfg_val.as_uint);
      s.replace("{t}", F("number"));
      break;
    case Config_Type_Time:
      t_value = String((*c.cfg_val.as_uint) / 1000);
      s.replace("{t}", F("number"));
      break;
    default:
      if (c.cfg_type == Config_Type_Password) {
        s.replace("{t}", F("password"));
        info = FPSTR(INTL_PASSWORD);
      } else {
        t_value = c.cfg_val.as_str;
        t_value.replace("'", "&#39;");
        s.replace("{t}", F("text"));
      }
  }
  s.replace("{i}", info);
  s.replace("{n}", String(c.cfg_key()));
  s.replace("{v}", t_value);
  s.replace("{l}", String(length));
  page_content += s;
}

static String form_checkbox(const ConfigShapeId cfgid, const String &info, const bool linebreak) {
  RESERVE_STRING(s, MED_STR);
  s = F("<label for='{n}'>"
        "<input type='checkbox' name='{n}' value='1' id='{n}' {c}/>"
        "<input type='hidden' name='{n}' value='0'/>"
        "{i}</label><br/>");
  if (*configShape[cfgid].cfg_val.as_bool) {
    s.replace("{c}", F(" checked='checked'"));
  } else {
    s.replace("{c}", emptyString);
  };
  s.replace("{i}", info);
  s.replace("{n}", String(configShape[cfgid].cfg_key()));
  if (!linebreak) {
    s.replace("<br/>", emptyString);
  }
  return s;
}

static String form_submit(const String &value) {
  String s = F("<tr>"
               "<td>&nbsp;</td>"
               "<td>"
               "<input type='submit' class='s_red' name='submit' value='{v}' />"
               "</td>"
               "</tr>");
  s.replace("{v}", value);
  return s;
}

static String form_select_lang() {
  String s_select = F(" selected='selected'");
  String s = F("<tr>"
               "<td>" INTL_LANGUAGE ":&nbsp;</td>"
               "<td>"
               "<select id='current_lang' name='current_lang'>"
               "<option value='BG'>Bulgarian (BG)</option>"
               "<option value='CN'>中文 (CN)</option>"
               "<option value='CZ'>Český (CZ)</option>"
               "<option value='DE'>Deutsch (DE)</option>"
               "<option value='DK'>Dansk (DK)</option>"
               "<option value='EE'>Eesti keel (EE)</option>"
               "<option value='EN'>English (EN)</option>"
               "<option value='ES'>Español (ES)</option>"
               "<option value='FR'>Français (FR)</option>"
               "<option value='GR'>Ελληνικά (GR)</option>"
               "<option value='IT'>Italiano (IT)</option>"
               "<option value='JP'>日本語 (JP)</option>"
               "<option value='LT'>Lietuvių kalba (LT)</option>"
               "<option value='LU'>Lëtzebuergesch (LU)</option>"
               "<option value='LV'>Latviešu valoda (LV)</option>"
               "<option value='NL'>Nederlands (NL)</option>"
               "<option value='HU'>Magyar (HU)</option>"
               "<option value='PL'>Polski (PL)</option>"
               "<option value='PT'>Português (PT)</option>"
               "<option value='RO'>Română (RO)</option>"
               "<option value='RS'>Srpski (RS)</option>"
               "<option value='RU'>Русский (RU)</option>"
               "<option value='SI'>Slovenščina (SI)</option>"
               "<option value='SK'>Slovák (SK)</option>"
               "<option value='SE'>Svenska (SE)</option>"
               "<option value='TR'>Türkçe (TR)</option>"
               "<option value='UA'>український (UA)</option>"
               "</select>"
               "</td>"
               "</tr>");

  s.replace("'" + String(cfg::current_lang) + "'>", "'" + String(cfg::current_lang) + "'" + s_select + ">");
  return s;
}

static void add_warning_first_cycle(String &page_content) {
  String s = FPSTR(INTL_TIME_TO_FIRST_MEASUREMENT);
  unsigned int time_to_first = cfg::sending_intervall_ms - msSince(starttime);
  if (time_to_first > cfg::sending_intervall_ms) {
    time_to_first = 0;
  }
  s.replace("{v}", String(((time_to_first + 500) / 1000)));
  page_content += s;
}

static void add_age_last_values(String &s) {
  s += "<b>";
  unsigned int time_since_last = msSince(starttime);
  if (time_since_last > cfg::sending_intervall_ms) {
    time_since_last = 0;
  }
  s += String((time_since_last + 500) / 1000);
  s += FPSTR(INTL_TIME_SINCE_LAST_MEASUREMENT);
  s += FPSTR(WEB_B_BR_BR);
}

/*****************************************************************
 * Webserver request auth: prompt for BasicAuth
 *
 * -Provide BasicAuth for all page contexts except /values and images
 *****************************************************************/
static bool webserver_request_auth() {
  if (cfg::www_basicauth_enabled && !wificonfig_loop) {
    debug_outln_info(F("validate request auth..."));
    if (!server.authenticate(cfg::www_username, cfg::www_password)) {
      server.requestAuthentication(BASIC_AUTH, "Sensor Login", F("Authentication failed"));
      return false;
    }
  }
  return true;
}

static void sendHttpRedirect() {
  const IPAddress defaultIP(
    default_ip_first_octet,
    default_ip_second_octet,
    default_ip_third_octet,
    default_ip_fourth_octet);

  String defaultAddress = F("http://") + defaultIP.toString() + F("/config");
  server.sendHeader(F("Location"), defaultAddress);
  server.send(302, FPSTR(TXT_CONTENT_TYPE_TEXT_HTML), emptyString);
}

/*****************************************************************
 * Webserver root: show all options                              *
 *****************************************************************/
static void webserver_root() {
  if (WiFi.status() != WL_CONNECTED) {
    sendHttpRedirect();
  } else {
    if (!webserver_request_auth()) {
      return;
    }

    RESERVE_STRING(page_content, XXLARGE_STR);
    start_html_page(page_content, emptyString);
    debug_outln_info(F("ws: root ..."));

    // Enable Pagination
    page_content += FPSTR(WEB_ROOT_PAGE_CONTENT);
    page_content.replace(F("{t}"), FPSTR(INTL_CURRENT_DATA));
    page_content.replace(F("{s}"), FPSTR(INTL_DEVICE_STATUS));
    page_content.replace(F("{conf}"), FPSTR(INTL_CONFIGURATION));
    page_content.replace(F("{restart}"), FPSTR(INTL_RESTART_SENSOR));
    page_content.replace(F("{debug}"), FPSTR(INTL_DEBUG_LEVEL));
    end_html_page(page_content);
  }
}

/*****************************************************************
 * Webserver config: show config page                            *
 *****************************************************************/
static void webserver_config_send_body_get(String &page_content) {
  auto add_form_checkbox = [&page_content](const ConfigShapeId cfgid, const String &info) {
    page_content += form_checkbox(cfgid, info, true);
  };

  auto add_form_checkbox_sensor = [&add_form_checkbox](const ConfigShapeId cfgid, __const __FlashStringHelper *info) {
    add_form_checkbox(cfgid, add_sensor_type(info));
  };


  debug_outln_info(F("begin webserver_config_body_get ..."));

  page_content += F("<form method='POST' action='/config' style='width:100%;'>\n"
                    "<input class='radio' id='r1' name='group' type='radio' checked>"
                    "<input class='radio' id='r2' name='group' type='radio'>"
                    "<input class='radio' id='r3' name='group' type='radio'>"
                    "<input class='radio' id='r4' name='group' type='radio'>"
                    "<input class='radio' id='r5' name='group' type='radio'>"
                    "<div class='tabs'>"
                    "<label class='tab' id='tab1' for='r1'>" INTL_WIFI_SETTINGS "</label>"
                    "<label class='tab' id='tab2' for='r2'>");
  page_content += FPSTR(INTL_MORE_SETTINGS);
  page_content += F("</label>"
                    "<label class='tab' id='tab3' for='r3'>");
  page_content += FPSTR(INTL_DNMS_SENSOR);
  page_content += F("</label>"
                    "<label class='tab' id='tab4' for='r4'>");
  page_content += FPSTR(INTL_MORE_SENSORS);
  page_content += F("</label>"
                    "<label class='tab' id='tab5' for='r5'>APIs"
                    "</label></div><div class='panels'>"
                    "<div class='panel' id='panel1'>");

  if (wificonfig_loop) {  // scan for wlan ssids
    page_content += F("<div id='wifilist'>" INTL_WIFI_NETWORKS "</div><br/>");
  }
  page_content += FPSTR(TABLE_TAG_OPEN);
  add_form_input(page_content, Config_wlanssid, FPSTR(INTL_FS_WIFI_NAME), LEN_WLANSSID - 1);
  page_content += FPSTR(TABLE_TAG_OPEN);
  add_form_checkbox(Config_with_wlanpwd, FPSTR(INTL_WIFI_WITH_PWD));
  page_content += FPSTR(TABLE_TAG_OPEN);
  add_form_input(page_content, Config_wlanpwd, FPSTR(INTL_PASSWORD), LEN_CFG_PASSWORD - 1);
  page_content += FPSTR(TABLE_TAG_CLOSE_BR);
  page_content += F("<hr/>");

  page_content += FPSTR(WEB_BR_LF_B);
  page_content += FPSTR(INTL_AB_HIER_NUR_ANDERN);
  page_content += FPSTR(WEB_B_BR);
  page_content += FPSTR(BR_TAG);

  // Paginate page after ~ 1500 Bytes
  server.sendContent(page_content);
  page_content = emptyString;

  add_form_checkbox(Config_www_basicauth_enabled, FPSTR(INTL_BASICAUTH));
  page_content += FPSTR(TABLE_TAG_OPEN);
  add_form_input(page_content, Config_www_username, FPSTR(INTL_USER), LEN_WWW_USERNAME - 1);
  add_form_input(page_content, Config_www_password, FPSTR(INTL_PASSWORD), LEN_CFG_PASSWORD - 1);
  page_content += FPSTR(TABLE_TAG_CLOSE_BR);
  page_content += FPSTR(BR_TAG);

  // Paginate page after ~ 1500 Bytes
  server.sendContent(page_content);

  if (!wificonfig_loop) {
    page_content = FPSTR(INTL_FS_WIFI_DESCRIPTION);
    page_content += FPSTR(BR_TAG);

    page_content += FPSTR(TABLE_TAG_OPEN);
    add_form_input(page_content, Config_fs_ssid, FPSTR(INTL_FS_WIFI_NAME), LEN_FS_SSID - 1);
    add_form_input(page_content, Config_fs_pwd, FPSTR(INTL_PASSWORD), LEN_CFG_PASSWORD - 1);
    page_content += FPSTR(TABLE_TAG_CLOSE_BR);

    // Paginate page after ~ 1500 Bytes
    server.sendContent(page_content);
  }

  /**************                        Further Settings                             **************/
  page_content = tmpl(FPSTR(WEB_DIV_PANEL), String(2));

  add_form_checkbox(Config_has_display, FPSTR(INTL_DISPLAY));
  add_form_checkbox(Config_has_sh1106, FPSTR(INTL_SH1106));
  add_form_checkbox(Config_has_flipped_display, FPSTR(INTL_FLIP_DISPLAY));
  add_form_checkbox(Config_has_lcd1602_27, FPSTR(INTL_LCD1602_27));
  add_form_checkbox(Config_has_lcd1602, FPSTR(INTL_LCD1602_3F));

  // Paginate page after ~ 1500 Bytes
  server.sendContent(page_content);
  page_content = emptyString;

  add_form_checkbox(Config_has_lcd2004_27, FPSTR(INTL_LCD2004_27));
  add_form_checkbox(Config_has_lcd2004, FPSTR(INTL_LCD2004_3F));
  add_form_checkbox(Config_display_wifi_info, FPSTR(INTL_DISPLAY_WIFI_INFO));
  add_form_checkbox(Config_display_device_info, FPSTR(INTL_DISPLAY_DEVICE_INFO));

  page_content += FPSTR(WEB_BR_LF_B);
  page_content += F(INTL_STATIC_IP_TEXT);
  page_content += FPSTR(WEB_B_BR);
  page_content += FPSTR(TABLE_TAG_OPEN);
  add_form_input(page_content, Config_static_ip, FPSTR(INTL_STATIC_IP), 15);
  add_form_input(page_content, Config_static_subnet, FPSTR(INTL_STATIC_SUBNET), 15);
  add_form_input(page_content, Config_static_gateway, FPSTR(INTL_STATIC_GATEWAY), 15);
  add_form_input(page_content, Config_static_dns, FPSTR(INTL_STATIC_DNS), 15);
  page_content += FPSTR(TABLE_TAG_CLOSE_BR);

  server.sendContent(page_content);
  page_content = emptyString;
  /*
  page_content = FPSTR(WEB_BR_LF_B);
  page_content += F(INTL_FIRMWARE);
  page_content += FPSTR(WEB_B_BR);
  add_form_checkbox(Config_auto_update, FPSTR(INTL_AUTO_UPDATE));
  add_form_checkbox(Config_use_beta, FPSTR(INTL_USE_BETA));

  page_content += FPSTR(TABLE_TAG_OPEN);
  page_content += form_select_lang();
  page_content += FPSTR(TABLE_TAG_CLOSE_BR);

  page_content += F("<script>"
                    "var $ = function(e) { return document.getElementById(e); };"
                    "function updateOTAOptions() { "
                    "$('current_lang').disabled = $('use_beta').disabled = !$('auto_update').checked; "
                    "}; updateOTAOptions(); $('auto_update').onchange = updateOTAOptions;"
                    "</script>");
*/

  page_content += FPSTR(WEB_BR_LF_B);
  page_content += FPSTR(INTL_AB_HIER_NUR_ANDERN);
  page_content += FPSTR(WEB_B_BR);
  page_content += FPSTR(BR_TAG);

  //  add_form_checkbox(Config_powersave, FPSTR(INTL_POWERSAVE));
  page_content += FPSTR(TABLE_TAG_OPEN);
  add_form_input(page_content, Config_debug, FPSTR(INTL_DEBUG_LEVEL), 1);
  add_form_input(page_content, Config_sending_intervall_ms, FPSTR(INTL_MEASUREMENT_INTERVAL), 5);
  add_form_input(page_content, Config_time_for_wifi_config, FPSTR(INTL_DURATION_ROUTER_MODE), 5);
  page_content += FPSTR(TABLE_TAG_CLOSE_BR);

  server.sendContent(page_content);
  page_content = emptyString;

  page_content += FPSTR(WEB_BR_BR);
  page_content += FPSTR(INTL_NTP_SERVER_TEXT);
  page_content += FPSTR(WEB_BR);
  page_content += FPSTR(TABLE_TAG_OPEN);
  add_form_input(page_content, Config_ntp_1, FPSTR(INTL_NTP_SERVER_1), LEN_NTP_1 - 1);
  add_form_input(page_content, Config_ntp_2, FPSTR(INTL_NTP_SERVER_2), LEN_NTP_2 - 1);
  page_content += FPSTR(TABLE_TAG_CLOSE_BR);

  page_content += FPSTR(WEB_BR_BR);
  page_content += FPSTR(INTL_START);
  page_content += FPSTR(WEB_BR);
  add_form_checkbox_sensor(Config_start_on_full_minute, FPSTR(INTL_START_ON_FULL_MINUTE));
  add_form_checkbox_sensor(Config_start_on_full_hour, FPSTR(INTL_START_ON_FULL_HOUR));
  page_content += FPSTR(WEB_LF_B);
  page_content += FPSTR(INTL_START_ZWEI);
  page_content += FPSTR(WEB_B_BR_BR);

  add_form_checkbox_sensor(Config_sensor_cyclic_restart, FPSTR(INTL_SENSOR_CYCLIC_RESTART));
  page_content += FPSTR(TABLE_TAG_OPEN);
  add_form_input(page_content, Config_sensor_cyclic_restart_time, FPSTR(INTL_SENSOR_CYCLIC_RESTART_TIME), 5);
  page_content += FPSTR(TABLE_TAG_CLOSE_BR);

  page_content += FPSTR(WEB_BR_BR);
  page_content += FPSTR(INTL_CAREFUL_ATTENTION);
  page_content += FPSTR(TABLE_TAG_OPEN);
  add_form_input(page_content, Config_i2c_gpio_scl, FPSTR(INTL_I2C_GPIO_SCL), 5);
  add_form_input(page_content, Config_i2c_gpio_sda, FPSTR(INTL_I2C_GPIO_SDA), 5);
  page_content += FPSTR(TABLE_TAG_CLOSE_BR);
  server.sendContent(page_content);


  /**************                        DNMS Noise Sensor                             **************/
  page_content = tmpl(FPSTR(WEB_DIV_PANEL), String(3));
  add_form_checkbox_sensor(Config_dnms_read, FPSTR(INTL_DNMS));
  add_form_checkbox_sensor(Config_dnms_read_Z, FPSTR(INTL_DNMS_Z));
  add_form_checkbox_sensor(Config_dnms_read_C, FPSTR(INTL_DNMS_C));
  add_form_checkbox_sensor(Config_dnms_read_spectrum, FPSTR(INTL_DNMS_SPECTRUM));
  add_form_checkbox_sensor(Config_dnms_read_spectrum_Z, FPSTR(INTL_DNMS_SPECTRUM_Z));
  add_form_checkbox_sensor(Config_dnms_read_spectrum_C, FPSTR(INTL_DNMS_SPECTRUM_C));
  page_content += FPSTR(WEB_BR_BR);
  add_form_checkbox_sensor(Config_dnms_2nd_interval, FPSTR(INTL_DNMS_2nd_INTERVAL));
  add_form_checkbox_sensor(Config_dnms_2nd_interval_Z, FPSTR(INTL_DNMS_2nd_INTERVAL_Z));
  add_form_checkbox_sensor(Config_dnms_2nd_interval_C, FPSTR(INTL_DNMS_2nd_INTERVAL_C));
  add_form_checkbox_sensor(Config_dnms_2nd_read_spectrum, FPSTR(INTL_DNMS_2nd_SPECTRUM));
  add_form_checkbox_sensor(Config_dnms_2nd_read_spectrum_Z, FPSTR(INTL_DNMS_2nd_SPECTRUM_Z));
  add_form_checkbox_sensor(Config_dnms_2nd_read_spectrum_C, FPSTR(INTL_DNMS_2nd_SPECTRUM_C));
  page_content += FPSTR(WEB_BR_BR);
  // Paginate page after ~ 1500 Bytes
  server.sendContent(page_content);
  page_content = emptyString;

  page_content += FPSTR(TABLE_TAG_OPEN);
  add_form_input(page_content, Config_dnms_2nd_interval_time, FPSTR(INTL_DNMS_2nd_INTERVAL_TIME), 5);
  add_form_input(page_content, Config_dnms_2nd_threshold, FPSTR(INTL_DNMS_2nd_THRESHOLD), 5);
  add_form_input(page_content, Config_dnms_2nd_number_measurements, FPSTR(INTL_DNMS_2nd_NUMBER_MEASUREMENTS), 5);
  page_content += FPSTR(TABLE_TAG_CLOSE_BR);
  add_form_checkbox_sensor(Config_dnms_2nd_switch_output, FPSTR(INTL_DNMS_2nd_SWITCH_OUTPUT));
  page_content += FPSTR(TABLE_TAG_OPEN);
  add_form_input(page_content, Config_dnms_2nd_gpio_pin, FPSTR(INTL_DNMS_2nd_GPIO_PIN), 5);
  page_content += FPSTR(TABLE_TAG_CLOSE_BR);
  page_content += FPSTR(WEB_BR_BR);
  page_content += FPSTR(TABLE_TAG_OPEN);
  add_form_input(page_content, Config_dnms_correction, FPSTR(INTL_DNMS_CORRECTION), LEN_DNMS_CORRECTION - 1);
  page_content += FPSTR(TABLE_TAG_CLOSE_BR);

  page_content += FPSTR(WEB_BR_BR);
  page_content += FPSTR(INTL_DNMS_MICROPHONE);
  page_content += FPSTR(WEB_BR);
  page_content += FPSTR(INTL_DNMS_MICROPHONE2);
  page_content += FPSTR(WEB_BR);

  page_content += FPSTR(TABLE_TAG_OPEN);
  add_form_input(page_content, Config_dnms_micro_type, FPSTR(INTL_DNMS_MICRO_TYPE), 5);
  page_content += FPSTR(TABLE_TAG_CLOSE_BR);


  page_content += FPSTR(WEB_BR_BR);
  page_content += FPSTR(TABLE_TAG_CLOSE_BR);
  add_form_checkbox_sensor(Config_dnms_read_din01, FPSTR(INTL_DNMS_READ_DIN01));
  page_content += FPSTR(TABLE_TAG_OPEN);
  add_form_input(page_content, Config_dnms_din01_pin, FPSTR(INTL_DNMS_DIN01_PIN), 5);
  page_content += FPSTR(TABLE_TAG_CLOSE_BR);


  // Paginate page after ~ 1500 Bytes
  server.sendContent(page_content);


  /**************                        More Sensors                             **************/
  page_content = tmpl(FPSTR(WEB_DIV_PANEL), String(4));
  add_form_checkbox_sensor(Config_sds_read, FPSTR(INTL_SDS011));
  add_form_checkbox_sensor(Config_hpm_read, FPSTR(INTL_HPM));
  add_form_checkbox_sensor(Config_sps30_read, FPSTR(INTL_SPS30));
  add_form_checkbox_sensor(Config_sen5x_read, FPSTR(INTL_SEN5X));
  add_form_checkbox_sensor(Config_dht_read, FPSTR(INTL_DHT22));
  add_form_checkbox_sensor(Config_htu21d_read, FPSTR(INTL_HTU21D));
  add_form_checkbox_sensor(Config_bmx280_read, FPSTR(INTL_BMX280));
  add_form_checkbox_sensor(Config_sht3x_read, FPSTR(INTL_SHT3X));
  add_form_checkbox_sensor(Config_scd30_read, FPSTR(INTL_SCD30));
  add_form_checkbox_sensor(Config_scd4x_read, FPSTR(INTL_SCD4X));
  add_form_checkbox_sensor(Config_scd4x_low_power, FPSTR(INTL_SCD4X_LOW_POWER));

  // Paginate page after ~ 1500 Bytes
  server.sendContent(page_content);
  page_content = emptyString;

  page_content += FPSTR(TABLE_TAG_OPEN);
  add_form_input(page_content, Config_temp_correction, FPSTR(INTL_TEMP_CORRECTION), LEN_TEMP_CORRECTION - 1);
  add_form_input(page_content, Config_height_above_sealevel, FPSTR(INTL_HEIGHT_ABOVE_SEALEVEL), LEN_HEIGHT_ABOVE_SEALEVEL - 1);
  page_content += FPSTR(TABLE_TAG_CLOSE_BR);

  page_content += FPSTR(WEB_BR_LF_B);
  page_content += FPSTR(INTL_MORE_SENSORS);
  page_content += FPSTR(WEB_B_BR);

  add_form_checkbox_sensor(Config_ds18b20_read, FPSTR(INTL_DS18B20));
  add_form_checkbox_sensor(Config_pms_read, FPSTR(INTL_PMS));
  add_form_checkbox_sensor(Config_npm_read, FPSTR(INTL_NPM));
  add_form_checkbox_sensor(Config_npm_fulltime, FPSTR(INTL_NPM_FULLTIME));
  add_form_checkbox_sensor(Config_ips_read, FPSTR(INTL_IPS));
  add_form_checkbox_sensor(Config_bmp_read, FPSTR(INTL_BMP180));
  add_form_checkbox(Config_gps_read, FPSTR(INTL_NEO6M));

  // Paginate page after ~ 1500 Bytes
  server.sendContent(page_content);


  /**************                        APIs                             **************/
  page_content = tmpl(FPSTR(WEB_DIV_PANEL), String(5));

  page_content += tmpl(FPSTR(INTL_SEND_TO), F("APIs"));
  page_content += FPSTR(BR_TAG);
  page_content += form_checkbox(Config_send2dusti, FPSTR(WEB_SENSORCOMMUNITY), false);
  page_content += FPSTR(BR_TAG);
  //  page_content += FPSTR(WEB_NBSP_NBSP_BRACE);
  //  page_content += form_checkbox(Config_ssl_dusti, FPSTR(WEB_HTTPS), false);
  //  page_content += FPSTR(WEB_BRACE_BR);
  page_content += form_checkbox(Config_send2madavi, FPSTR(WEB_MADAVI), false);
  page_content += FPSTR(BR_TAG);
  //  page_content += FPSTR(WEB_NBSP_NBSP_BRACE);
  //  page_content += form_checkbox(Config_ssl_madavi, FPSTR(WEB_HTTPS), false);
  //  page_content += FPSTR(WEB_BRACE_BR);
  add_form_checkbox(Config_send2csv, FPSTR(WEB_CSV));
  add_form_checkbox(Config_send2fsapp, FPSTR(WEB_FEINSTAUB_APP));
  add_form_checkbox(Config_send2aircms, FPSTR(WEB_AIRCMS));
  add_form_checkbox(Config_send2sensemap, FPSTR(WEB_OPENSENSEMAP));
  page_content += FPSTR(TABLE_TAG_OPEN);
  add_form_input(page_content, Config_senseboxid, F("senseBox&nbsp;ID"), LEN_SENSEBOXID - 1);

  server.sendContent(page_content);

  page_content = FPSTR(TABLE_TAG_CLOSE_BR);
  page_content += FPSTR(BR_TAG);
  page_content += form_checkbox(Config_send2custom, FPSTR(INTL_SEND_TO_OWN_API), false);
  //  page_content += FPSTR(WEB_NBSP_NBSP_BRACE);
  //  page_content += form_checkbox(Config_ssl_custom, FPSTR(WEB_HTTPS), false);
  //  page_content += FPSTR(WEB_BRACE_BR);

  page_content = FPSTR(TABLE_TAG_OPEN);
  add_form_input(page_content, Config_host_custom, FPSTR(INTL_SERVER), LEN_HOST_CUSTOM - 1);
  add_form_input(page_content, Config_url_custom, FPSTR(INTL_PATH), LEN_URL_CUSTOM - 1);
  add_form_input(page_content, Config_port_custom, FPSTR(INTL_PORT), MAX_PORT_DIGITS);
  add_form_input(page_content, Config_user_custom, FPSTR(INTL_USER), LEN_USER_CUSTOM - 1);
  add_form_input(page_content, Config_pwd_custom, FPSTR(INTL_PASSWORD), LEN_CFG_PASSWORD - 1);
  page_content += FPSTR(TABLE_TAG_CLOSE_BR);

  page_content += FPSTR(BR_TAG);

  server.sendContent(page_content);

  page_content = form_checkbox(Config_send2influx, tmpl(FPSTR(INTL_SEND_TO), F("InfluxDB (V1, V2 and V3 only with 1.x compatibility mode)")), false);
  //  page_content += FPSTR(WEB_NBSP_NBSP_BRACE);
  //  page_content += form_checkbox(Config_ssl_influx, FPSTR(WEB_HTTPS), false);
  //  page_content += FPSTR(WEB_BRACE_BR);
  page_content += FPSTR(TABLE_TAG_OPEN);
  add_form_input(page_content, Config_host_influx, FPSTR(INTL_SERVER), LEN_HOST_INFLUX - 1);
  add_form_input(page_content, Config_url_influx, FPSTR(INTL_PATH), LEN_URL_INFLUX - 1);
  add_form_input(page_content, Config_port_influx, FPSTR(INTL_PORT), MAX_PORT_DIGITS);
  add_form_input(page_content, Config_user_influx, FPSTR(INTL_USER), LEN_USER_INFLUX - 1);
  add_form_input(page_content, Config_pwd_influx, FPSTR(INTL_PASSWORD), LEN_PASS_INFLUX - 1);
  add_form_input(page_content, Config_measurement_name_influx, FPSTR(INTL_INFLUX_MEASUREMENT), LEN_MEASUREMENT_NAME_INFLUX - 1);
  page_content += FPSTR(TABLE_TAG_CLOSE_BR);

  page_content += FPSTR(BR_TAG);

  server.sendContent(page_content);
    
  page_content = form_checkbox(Config_send2mqtt, tmpl(FPSTR(INTL_SEND_TO), F("MQTT Broker")), false);
  //  page_content += FPSTR(WEB_NBSP_NBSP_BRACE);
  //  page_content += form_checkbox(Config_tls_mqtt, FPSTR(WEB_TLS), false);
  //  page_content += FPSTR(WEB_BRACE_BR);
  page_content += FPSTR(TABLE_TAG_OPEN);
  add_form_input(page_content, Config_host_mqtt, FPSTR(INTL_SERVER), LEN_HOST_MQTT - 1);
  add_form_input(page_content, Config_port_mqtt, FPSTR(INTL_PORT), MAX_PORT_DIGITS);
  add_form_input(page_content, Config_user_mqtt, FPSTR(INTL_USER), LEN_USER_MQTT - 1);
  add_form_input(page_content, Config_pwd_mqtt, FPSTR(INTL_PASSWORD), LEN_PASS_MQTT - 1);
  add_form_input(page_content, Config_measurement_name_mqtt, FPSTR(INTL_MQTT_MEASUREMENT), LEN_MEASUREMENT_NAME_MQTT - 1);
  add_form_input(page_content, Config_mqtt_main_topic, FPSTR(INTL_MQTT_MAIN_TOPIC), LEN_MQTT_MAIN_TOPIC - 1);
  page_content += FPSTR(TABLE_TAG_CLOSE_BR);
  add_form_checkbox_sensor(Config_id_as_mqtt_sub_topic, FPSTR(INTL_ID_AS_MQTT_SUB_TOPIC));
  page_content += FPSTR(TABLE_TAG_OPEN);
  page_content += FPSTR(TABLE_TAG_CLOSE_BR);

  page_content += F("</div></div>");
  page_content += form_submit(FPSTR(INTL_SAVE_AND_RESTART));
  page_content += FPSTR(BR_TAG);
  page_content += FPSTR(WEB_BR_FORM);

  if (wificonfig_loop) {  // scan for wlan ssids
    page_content += F("<script>window.setTimeout(load_wifi_list,1000);</script>");
  }

  server.sendContent(page_content);
  page_content = emptyString;
}


static void webserver_config_send_body_post(String &page_content) {
  String masked_pwd;

  for (unsigned e = 0; e < sizeof(configShape) / sizeof(configShape[0]); ++e) {
    ConfigShapeEntry c;
    memcpy_P(&c, &configShape[e], sizeof(ConfigShapeEntry));
    const String s_param(c.cfg_key());
    if (!server.hasArg(s_param)) {
      continue;
    }
    const String server_arg(server.arg(s_param));

    switch (c.cfg_type) {
      case Config_Type_UInt:
        *(c.cfg_val.as_uint) = server_arg.toInt();
        break;
      case Config_Type_Time:
        *(c.cfg_val.as_uint) = server_arg.toInt() * 1000;
        break;
      case Config_Type_Bool:
        *(c.cfg_val.as_bool) = (server_arg == "1");
        break;
      case Config_Type_String:
        strncpy(c.cfg_val.as_str, server_arg.c_str(), c.cfg_len);
        c.cfg_val.as_str[c.cfg_len] = '\0';
        break;
      case Config_Type_Password:
        if (server_arg.length()) {
          server_arg.toCharArray(c.cfg_val.as_str, LEN_CFG_PASSWORD);
        }
        break;
    }
  }

  page_content += FPSTR(INTL_SENSOR_IS_REBOOTING);

  server.sendContent(page_content);
  page_content = emptyString;
}

static void webserver_config() {
  if (!webserver_request_auth()) {
    return;
  }

  debug_outln_info(F("ws: config page ..."));

  server.sendHeader(F("Cache-Control"), F("no-cache, no-store, must-revalidate"));
  server.sendHeader(F("Pragma"), F("no-cache"));
  server.sendHeader(F("Expires"), F("0"));
  // Enable Pagination (Chunked Transfer)
  server.setContentLength(CONTENT_LENGTH_UNKNOWN);

  RESERVE_STRING(page_content, XLARGE_STR);

  start_html_page(page_content, FPSTR(INTL_CONFIGURATION));
  if (wificonfig_loop) {  // scan for wlan ssids
    page_content += FPSTR(WEB_CONFIG_SCRIPT);
  }

  if (server.method() == HTTP_GET) {
    webserver_config_send_body_get(page_content);
  } else {
    webserver_config_send_body_post(page_content);
  }
  end_html_page(page_content);

  if (server.method() == HTTP_POST) {
    display_debug(F("Writing config"), emptyString);
    if (writeConfig()) {
      display_debug(F("Writing config"), F("and restarting"));
      sensor_restart();
    }
  }
}

/*****************************************************************
 * sensor restart                                                *
 *****************************************************************/
static void sensor_restart() {
#if defined(ESP8266)
  WiFi.disconnect();
  WiFi.mode(WIFI_OFF);
  delay(100);
#endif

#pragma GCC diagnostic push
#pragma GCC diagnostic ignored "-Wdeprecated-declarations"

  LittleFS.end();

#pragma GCC diagnostic pop

  if (cfg::npm_read) {
    serialNPM.end();
  } else {
    serialSDS.end();
  }
  debug_outln_info(F("Restart."));
  delay(500);
  ESP.restart();
  // should not be reached
  while (true) {
    yield();
  }
}

/*****************************************************************
 * Webserver wifi: show available wifi networks                  *
 *****************************************************************/
static void webserver_wifi() {
  String page_content;

  debug_outln_info(F("wifi networks found: "), String(count_wifiInfo));
  if (count_wifiInfo == 0) {
    page_content += FPSTR(BR_TAG);
    page_content += FPSTR(INTL_NO_NETWORKS);
    page_content += FPSTR(BR_TAG);
  } else {
    std::unique_ptr<int[]> indices(new int[count_wifiInfo]);
    debug_outln_info(F("ws: wifi ..."));
    for (unsigned i = 0; i < count_wifiInfo; ++i) {
      indices[i] = i;
    }
    for (unsigned i = 0; i < count_wifiInfo; i++) {
      for (unsigned j = i + 1; j < count_wifiInfo; j++) {
        if (wifiInfo[indices[j]].RSSI > wifiInfo[indices[i]].RSSI) {
          std::swap(indices[i], indices[j]);
        }
      }
    }
    int duplicateSsids = 0;
    for (int i = 0; i < count_wifiInfo; i++) {
      if (indices[i] == -1) {
        continue;
      }
      for (int j = i + 1; j < count_wifiInfo; j++) {
        if (strncmp(wifiInfo[indices[i]].ssid, wifiInfo[indices[j]].ssid, sizeof(wifiInfo[0].ssid)) == 0) {
          indices[j] = -1;  // set dup aps to index -1
          ++duplicateSsids;
        }
      }
    }

    page_content += FPSTR(INTL_NETWORKS_FOUND);
    page_content += String(count_wifiInfo - duplicateSsids);
    page_content += FPSTR(BR_TAG);
    page_content += FPSTR(BR_TAG);
    page_content += FPSTR(TABLE_TAG_OPEN);
    //if (n > 30) n=30;
    for (int i = 0; i < count_wifiInfo; ++i) {
      if (indices[i] == -1
#if defined(ESP8266)
          || wifiInfo[indices[i]].isHidden
#endif
      ) {
        continue;
      }
      // Print SSID and RSSI for each network found
#if defined(ESP8266)
      page_content += wlan_ssid_to_table_row(wifiInfo[indices[i]].ssid, ((wifiInfo[indices[i]].encryptionType == ENC_TYPE_NONE) ? " " : u8"🔒"), wifiInfo[indices[i]].RSSI);
#endif
#if defined(ESP32)
      page_content += wlan_ssid_to_table_row(wifiInfo[indices[i]].ssid, ((wifiInfo[indices[i]].encryptionType == WIFI_AUTH_OPEN) ? " " : u8"🔒"), wifiInfo[indices[i]].RSSI);
#endif
    }
    page_content += FPSTR(TABLE_TAG_CLOSE_BR);
    page_content += FPSTR(BR_TAG);
  }
  server.send(200, FPSTR(TXT_CONTENT_TYPE_TEXT_HTML), page_content);
}

/*****************************************************************
 * Webserver root: show latest values                            *
 *****************************************************************/
static void webserver_values() {
  if (WiFi.status() != WL_CONNECTED) {
    sendHttpRedirect();
    return;
  }

  RESERVE_STRING(page_content, XLARGE_STR);
  start_html_page(page_content, FPSTR(INTL_CURRENT_DATA));
  const String unit_Deg("°");
  const String unit_P("hPa");
  const String unit_T("°C");
  const String unit_CO2("ppm");
  const String unit_NC();
  const String unit_LA(F("dB(A)"));
  const String unit_LZ(F("dB"));
  const String unit_LC(F("dB(C)"));
  float dew_point_temp;

  const int signal_quality = calcWiFiSignalQuality(last_signal_strength);
  debug_outln_info(F("ws: values ..."));
  if (!count_sends) {
    page_content += F("<b style='color:red'>");
    add_warning_first_cycle(page_content);
    page_content += FPSTR(WEB_B_BR_BR);
  } else {
    add_age_last_values(page_content);
  }

  auto add_table_pm_value = [&page_content](const __FlashStringHelper *sensor, const __FlashStringHelper *param, const float &value) {
    add_table_row_from_value(page_content, sensor, param, check_display_value(value, -1, 1, 0), F("µg/m³"));
  };

  auto add_table_nc_value = [&page_content](const __FlashStringHelper *sensor, const __FlashStringHelper *param, const float value) {
    add_table_row_from_value(page_content, sensor, param, check_display_value(value, -1, 1, 0), F("#/cm³"));
  };

  auto add_table_t_value = [&page_content](const __FlashStringHelper *sensor, const __FlashStringHelper *param, const float value) {
    add_table_row_from_value(page_content, sensor, param, check_display_value(value, -128, 1, 0), "°C");
  };

  auto add_table_h_value = [&page_content](const __FlashStringHelper *sensor, const __FlashStringHelper *param, const float value) {
    add_table_row_from_value(page_content, sensor, param, check_display_value(value, -1, 1, 0), "%");
  };

  auto add_table_value = [&page_content](const __FlashStringHelper *sensor, const __FlashStringHelper *param, const String &value, const String &unit) {
    add_table_row_from_value(page_content, sensor, param, value, unit);
  };

  // Flush page_content to the client and reset it. Called after each large
  // DNMS spectrum block (31 rows × ~85 bytes = ~2.6 KB) to avoid growing
  // page_content past what ESP8266 heap can reliably allocate in one chunk.
  // Guards against empty sends: in chunked HTTP mode, sendContent("") emits
  // the zero-length terminator chunk (0\r\n\r\n) and closes the response,
  // which would silently drop everything sent afterwards.
  auto flush_page = [&page_content]() {
    if (page_content.length()) {
      server.sendContent(page_content);
      page_content = emptyString;
    }
  };

  server.sendContent(page_content);
  page_content = F("<table cellspacing='0' cellpadding='5' class='v'>\n"
                   "<thead><tr><th>" INTL_SENSOR "</th><th> " INTL_PARAMETER "</th><th>" INTL_VALUE "</th></tr></thead>");
  if (cfg::ppd_read) {
    add_table_value(FPSTR(SENSORS_PPD42NS), FPSTR(WEB_PM1), check_display_value(last_value_PPD_P1, -1, 1, 0), FPSTR(INTL_PARTICLES_PER_LITER));
    add_table_value(FPSTR(SENSORS_PPD42NS), FPSTR(WEB_PM25), check_display_value(last_value_PPD_P2, -1, 1, 0), FPSTR(INTL_PARTICLES_PER_LITER));
    page_content += FPSTR(EMPTY_ROW);
  }
  if (cfg::sds_read) {
    add_table_pm_value(FPSTR(SENSORS_SDS011), FPSTR(WEB_PM25), last_value_SDS_P2);
    add_table_pm_value(FPSTR(SENSORS_SDS011), FPSTR(WEB_PM10), last_value_SDS_P1);
    page_content += FPSTR(EMPTY_ROW);
  }
  if (cfg::pms_read) {
    add_table_pm_value(FPSTR(SENSORS_PMSx003), FPSTR(WEB_PM1), last_value_PMS_P0);
    add_table_pm_value(FPSTR(SENSORS_PMSx003), FPSTR(WEB_PM25), last_value_PMS_P2);
    add_table_pm_value(FPSTR(SENSORS_PMSx003), FPSTR(WEB_PM10), last_value_PMS_P1);
    page_content += FPSTR(EMPTY_ROW);
  }
  if (cfg::hpm_read) {
    add_table_pm_value(FPSTR(SENSORS_HPM), FPSTR(WEB_PM25), last_value_HPM_P2);
    add_table_pm_value(FPSTR(SENSORS_HPM), FPSTR(WEB_PM10), last_value_HPM_P1);
    page_content += FPSTR(EMPTY_ROW);
  }
  if (cfg::npm_read) {
    add_table_pm_value(FPSTR(SENSORS_NPM), FPSTR(WEB_PM1), last_value_NPM_P0);
    add_table_pm_value(FPSTR(SENSORS_NPM), FPSTR(WEB_PM25), last_value_NPM_P2);
    add_table_pm_value(FPSTR(SENSORS_NPM), FPSTR(WEB_PM10), last_value_NPM_P1);
    add_table_nc_value(FPSTR(SENSORS_NPM), FPSTR(WEB_NC1k0), last_value_NPM_N1);
    add_table_nc_value(FPSTR(SENSORS_NPM), FPSTR(WEB_NC2k5), last_value_NPM_N25);
    add_table_nc_value(FPSTR(SENSORS_NPM), FPSTR(WEB_NC10), last_value_NPM_N10);
    page_content += FPSTR(EMPTY_ROW);
  }
  if (cfg::ips_read) {
    add_table_pm_value(FPSTR(SENSORS_IPS), FPSTR(WEB_PM01), last_value_IPS_P01);
    add_table_pm_value(FPSTR(SENSORS_IPS), FPSTR(WEB_PM03), last_value_IPS_P03);
    add_table_pm_value(FPSTR(SENSORS_IPS), FPSTR(WEB_PM05), last_value_IPS_P05);
    add_table_pm_value(FPSTR(SENSORS_IPS), FPSTR(WEB_PM1), last_value_IPS_P0);
    add_table_pm_value(FPSTR(SENSORS_IPS), FPSTR(WEB_PM25), last_value_IPS_P2);
    add_table_pm_value(FPSTR(SENSORS_IPS), FPSTR(WEB_PM5), last_value_IPS_P5);
    add_table_pm_value(FPSTR(SENSORS_IPS), FPSTR(WEB_PM10), last_value_IPS_P1);
    add_table_nc_value(FPSTR(SENSORS_IPS), FPSTR(WEB_NC0k1), last_value_IPS_N01);
    add_table_nc_value(FPSTR(SENSORS_IPS), FPSTR(WEB_NC0k3), last_value_IPS_N03);
    add_table_nc_value(FPSTR(SENSORS_IPS), FPSTR(WEB_NC0k5), last_value_IPS_N05);
    add_table_nc_value(FPSTR(SENSORS_IPS), FPSTR(WEB_NC1k0), last_value_IPS_N1);
    add_table_nc_value(FPSTR(SENSORS_IPS), FPSTR(WEB_NC2k5), last_value_IPS_N25);
    add_table_nc_value(FPSTR(SENSORS_IPS), FPSTR(WEB_NC5k0), last_value_IPS_N5);
    add_table_nc_value(FPSTR(SENSORS_IPS), FPSTR(WEB_NC10), last_value_IPS_N10);
    page_content += FPSTR(EMPTY_ROW);
  }
  if (cfg::sps30_read) {
    add_table_pm_value(FPSTR(SENSORS_SPS30), FPSTR(WEB_PM1), last_value_SPS30_P0);
    add_table_pm_value(FPSTR(SENSORS_SPS30), FPSTR(WEB_PM25), last_value_SPS30_P2);
    add_table_pm_value(FPSTR(SENSORS_SPS30), FPSTR(WEB_PM4), last_value_SPS30_P4);
    add_table_pm_value(FPSTR(SENSORS_SPS30), FPSTR(WEB_PM10), last_value_SPS30_P1);
    add_table_nc_value(FPSTR(SENSORS_SPS30), FPSTR(WEB_NC0k5), last_value_SPS30_N05);
    add_table_nc_value(FPSTR(SENSORS_SPS30), FPSTR(WEB_NC1k0), last_value_SPS30_N1);
    add_table_nc_value(FPSTR(SENSORS_SPS30), FPSTR(WEB_NC2k5), last_value_SPS30_N25);
    add_table_nc_value(FPSTR(SENSORS_SPS30), FPSTR(WEB_NC4k0), last_value_SPS30_N4);
    add_table_nc_value(FPSTR(SENSORS_SPS30), FPSTR(WEB_NC10), last_value_SPS30_N10);
    add_table_value(FPSTR(SENSORS_SPS30), FPSTR(WEB_TPS), check_display_value(last_value_SPS30_TS, -1, 1, 0), "µm");
    page_content += FPSTR(EMPTY_ROW);
  }
  if (cfg::sen5x_read) {
    add_table_pm_value(FPSTR(SENSORS_SEN5X), FPSTR(WEB_PM1), last_value_SEN5X_P0);
    add_table_pm_value(FPSTR(SENSORS_SEN5X), FPSTR(WEB_PM25), last_value_SEN5X_P2);
    add_table_pm_value(FPSTR(SENSORS_SEN5X), FPSTR(WEB_PM4), last_value_SEN5X_P4);
    add_table_pm_value(FPSTR(SENSORS_SEN5X), FPSTR(WEB_PM10), last_value_SEN5X_P1);
    add_table_nc_value(FPSTR(SENSORS_SEN5X), FPSTR(WEB_NC0k5), last_value_SEN5X_N05);
    add_table_nc_value(FPSTR(SENSORS_SEN5X), FPSTR(WEB_NC1k0), last_value_SEN5X_N1);
    add_table_nc_value(FPSTR(SENSORS_SEN5X), FPSTR(WEB_NC2k5), last_value_SEN5X_N25);
    add_table_nc_value(FPSTR(SENSORS_SEN5X), FPSTR(WEB_NC4k0), last_value_SEN5X_N4);
    add_table_nc_value(FPSTR(SENSORS_SEN5X), FPSTR(WEB_NC10), last_value_SEN5X_N10);
    add_table_value(FPSTR(SENSORS_SEN5X), FPSTR(WEB_TPS), check_display_value(last_value_SEN5X_TS, -1, 1, 0), "µm");
    if ((SEN5X_type[4] == '4') || (SEN5X_type[4] == '5')) {
      add_table_t_value(FPSTR(SENSORS_SEN5X), FPSTR(INTL_TEMPERATURE), last_value_SEN5X_T);
      add_table_h_value(FPSTR(SENSORS_SEN5X), FPSTR(INTL_HUMIDITY), last_value_SEN5X_H);
      add_table_value(FPSTR(SENSORS_SEN5X), FPSTR(INTL_VOC), check_display_value(last_value_SEN5X_VOC, 0, 0, 0), "(index)");
    }
    if (SEN5X_type[4] == '5') {
      add_table_value(FPSTR(SENSORS_SEN5X), FPSTR(INTL_NOX), check_display_value(last_value_SEN5X_NOX, 0, 0, 0), "(index)");
    }
    page_content += FPSTR(EMPTY_ROW);
  }
  if (cfg::dht_read) {
    add_table_t_value(FPSTR(SENSORS_DHT22), FPSTR(INTL_TEMPERATURE), last_value_DHT_T);
    add_table_h_value(FPSTR(SENSORS_DHT22), FPSTR(INTL_HUMIDITY), last_value_DHT_H);
    page_content += FPSTR(EMPTY_ROW);
  }
  if (cfg::htu21d_read) {
    add_table_t_value(FPSTR(SENSORS_HTU21D), FPSTR(INTL_TEMPERATURE), last_value_HTU21D_T);
    add_table_h_value(FPSTR(SENSORS_HTU21D), FPSTR(INTL_HUMIDITY), last_value_HTU21D_H);
    dew_point_temp = dew_point(last_value_HTU21D_T, last_value_HTU21D_H);
    add_table_value(FPSTR(SENSORS_HTU21D), FPSTR(INTL_DEW_POINT), isnan(dew_point_temp) ? "-" : String(dew_point_temp, 1), unit_T);
    page_content += FPSTR(EMPTY_ROW);
  }
  if (cfg::bmp_read) {
    add_table_t_value(FPSTR(SENSORS_BMP180), FPSTR(INTL_TEMPERATURE), last_value_BMP_T);
    add_table_value(FPSTR(SENSORS_BMP180), FPSTR(INTL_PRESSURE), check_display_value(last_value_BMP_P / 100.0f, (-1 / 100.0f), 2, 0), unit_P);
    add_table_value(FPSTR(SENSORS_BMP180), FPSTR(INTL_PRESSURE_AT_SEALEVEL), last_value_BMP_P != -1.0f ? String(pressure_at_sealevel(last_value_BMP_T, last_value_BMP_P / 100.0f), 2) : "-", unit_P);
    page_content += FPSTR(EMPTY_ROW);
  }
  if (cfg::bmx280_read) {
    const char *const sensor_name = (bmx280.sensorID() == BME280_SENSOR_ID) ? SENSORS_BME280 : SENSORS_BMP280;
    add_table_t_value(FPSTR(sensor_name), FPSTR(INTL_TEMPERATURE), last_value_BMX280_T);
    add_table_value(FPSTR(sensor_name), FPSTR(INTL_PRESSURE), check_display_value(last_value_BMX280_P / 100.0f, (-1 / 100.0f), 2, 0), unit_P);
    add_table_value(FPSTR(sensor_name), FPSTR(INTL_PRESSURE_AT_SEALEVEL), last_value_BMX280_P != -1.0f ? String(pressure_at_sealevel(last_value_BMX280_T, last_value_BMX280_P / 100.0f), 2) : "-", unit_P);
    if (bmx280.sensorID() == BME280_SENSOR_ID) {
      add_table_h_value(FPSTR(sensor_name), FPSTR(INTL_HUMIDITY), last_value_BME280_H);
      dew_point_temp = dew_point(last_value_BMX280_T, last_value_BME280_H);
      add_table_value(FPSTR(sensor_name), FPSTR(INTL_DEW_POINT), isnan(dew_point_temp) ? "-" : String(dew_point_temp, 1), unit_T);
    }
    page_content += FPSTR(EMPTY_ROW);
  }
  if (cfg::sht3x_read) {
    add_table_t_value(FPSTR(SENSORS_SHT3X), FPSTR(INTL_TEMPERATURE), last_value_SHT3X_T);
    add_table_h_value(FPSTR(SENSORS_SHT3X), FPSTR(INTL_HUMIDITY), last_value_SHT3X_H);
    dew_point_temp = dew_point(last_value_SHT3X_T, last_value_SHT3X_H);
    add_table_value(FPSTR(SENSORS_SHT3X), FPSTR(INTL_DEW_POINT), isnan(dew_point_temp) ? "-" : String(dew_point_temp, 1), unit_T);
    page_content += FPSTR(EMPTY_ROW);
  }
  if (cfg::scd30_read) {
    add_table_t_value(FPSTR(SENSORS_SCD30), FPSTR(INTL_TEMPERATURE), last_value_SCD30_T);
    add_table_h_value(FPSTR(SENSORS_SCD30), FPSTR(INTL_HUMIDITY), last_value_SCD30_H);
    add_table_value(FPSTR(SENSORS_SCD30), FPSTR(INTL_CO2_PPM), check_display_value(last_value_SCD30_CO2, 0, 0, 0), unit_CO2);
    dew_point_temp = dew_point(last_value_SCD30_T, last_value_SCD30_H);
    add_table_value(FPSTR(SENSORS_SCD30), FPSTR(INTL_DEW_POINT), isnan(dew_point_temp) ? "-" : String(dew_point_temp, 1), unit_T);
    page_content += FPSTR(EMPTY_ROW);
  }
  if (cfg::scd4x_read) {
    add_table_t_value(FPSTR(SENSORS_SCD4X), FPSTR(INTL_TEMPERATURE), last_value_SCD4X_T);
    add_table_h_value(FPSTR(SENSORS_SCD4X), FPSTR(INTL_HUMIDITY), last_value_SCD4X_H);
    add_table_value(FPSTR(SENSORS_SCD4X), FPSTR(INTL_CO2_PPM), check_display_value(last_value_SCD4X_CO2, 0, 0, 0), unit_CO2);
    dew_point_temp = dew_point(last_value_SCD4X_T, last_value_SCD4X_H);
    add_table_value(FPSTR(SENSORS_SCD4X), FPSTR(INTL_DEW_POINT), isnan(dew_point_temp) ? "-" : String(dew_point_temp, 1), unit_T);
    page_content += FPSTR(EMPTY_ROW);
  }
  if (cfg::ds18b20_read) {
    add_table_t_value(FPSTR(SENSORS_DS18B20), FPSTR(INTL_TEMPERATURE), last_value_DS18B20_T);
    page_content += FPSTR(EMPTY_ROW);
  }
  if (cfg::dnms_read_active) {
    add_table_value(FPSTR(SENSORS_DNMS), FPSTR(INTL_LEQ_A), check_display_value(last_value_dnms_laeq, -1, 1, 0), unit_LA);
    add_table_value(FPSTR(SENSORS_DNMS), FPSTR(INTL_LA_MIN), check_display_value(last_value_dnms_la_min, -1, 1, 0), unit_LA);
    add_table_value(FPSTR(SENSORS_DNMS), FPSTR(INTL_LA_MAX), check_display_value(last_value_dnms_la_max, -1, 1, 0), unit_LA);
    page_content += FPSTR(EMPTY_ROW);
  }
  if (cfg::dnms_read_Z_active) {
    add_table_value(FPSTR(SENSORS_DNMS), FPSTR(INTL_LEQ_Z), check_display_value(last_value_dnms_lzeq, -1, 1, 0), unit_LZ);
    add_table_value(FPSTR(SENSORS_DNMS), FPSTR(INTL_LZ_MIN), check_display_value(last_value_dnms_lz_min, -1, 1, 0), unit_LZ);
    add_table_value(FPSTR(SENSORS_DNMS), FPSTR(INTL_LZ_MAX), check_display_value(last_value_dnms_lz_max, -1, 1, 0), unit_LZ);
    page_content += FPSTR(EMPTY_ROW);
  }
  if (cfg::dnms_read_C_active) {
    add_table_value(FPSTR(SENSORS_DNMS), FPSTR(INTL_LEQ_C), check_display_value(last_value_dnms_lceq, -1, 1, 0), unit_LC);
    add_table_value(FPSTR(SENSORS_DNMS), FPSTR(INTL_LC_MIN), check_display_value(last_value_dnms_lc_min, -1, 1, 0), unit_LC);
    add_table_value(FPSTR(SENSORS_DNMS), FPSTR(INTL_LC_MAX), check_display_value(last_value_dnms_lc_max, -1, 1, 0), unit_LC);
    page_content += FPSTR(EMPTY_ROW);
  }
  if (cfg::dnms_read_spectrum_active) {
    for (unsigned i = 0; i < 31; i++) {
      add_table_value(FPSTR(SENSORS_DNMS), FPSTR(WEB_LAeq_HZ_2[i]), check_display_value(last_value_dnms_laeq_freq_spec[i], -1, 1, 0), unit_LA);
    }
    page_content += FPSTR(EMPTY_ROW);
    flush_page();
  }
  if (cfg::dnms_read_spectrum_Z_active) {
    for (unsigned i = 0; i < 31; i++) {
      add_table_value(FPSTR(SENSORS_DNMS), FPSTR(WEB_LZeq_HZ_2[i]), check_display_value(last_value_dnms_lzeq_freq_spec[i], -1, 1, 0), unit_LZ);
    }
    page_content += FPSTR(EMPTY_ROW);
    flush_page();
  }
  if (cfg::dnms_read_spectrum_C_active) {
    for (unsigned i = 0; i < 31; i++) {
      add_table_value(FPSTR(SENSORS_DNMS), FPSTR(WEB_LCeq_HZ_2[i]), check_display_value(last_value_dnms_lceq_freq_spec[i], -1, 1, 0), unit_LC);
    }
    page_content += FPSTR(EMPTY_ROW);
    flush_page();
  }
  if (cfg::dnms_2nd_interval_active) {
    add_table_value(FPSTR(SENSORS_DNMS), FPSTR(INTL_LEQ_A_2nd), check_display_value(last_value_dnms_laeq_2nd, -1, 1, 0), unit_LA);
    add_table_value(FPSTR(SENSORS_DNMS), FPSTR(INTL_LA_MIN_2nd), check_display_value(last_value_dnms_la_min_2nd, -1, 1, 0), unit_LA);
    add_table_value(FPSTR(SENSORS_DNMS), FPSTR(INTL_LA_MAX_2nd), check_display_value(last_value_dnms_la_max_2nd, -1, 1, 0), unit_LA);
    page_content += FPSTR(EMPTY_ROW);
  }
  if (cfg::dnms_2nd_interval_Z_active) {
    add_table_value(FPSTR(SENSORS_DNMS), FPSTR(INTL_LEQ_Z_2nd), check_display_value(last_value_dnms_lzeq_2nd, -1, 1, 0), unit_LZ);
    add_table_value(FPSTR(SENSORS_DNMS), FPSTR(INTL_LZ_MIN_2nd), check_display_value(last_value_dnms_lz_min_2nd, -1, 1, 0), unit_LZ);
    add_table_value(FPSTR(SENSORS_DNMS), FPSTR(INTL_LZ_MAX_2nd), check_display_value(last_value_dnms_lz_max_2nd, -1, 1, 0), unit_LZ);
    page_content += FPSTR(EMPTY_ROW);
  }
  if (cfg::dnms_2nd_interval_C_active) {
    add_table_value(FPSTR(SENSORS_DNMS), FPSTR(INTL_LEQ_C_2nd), check_display_value(last_value_dnms_lceq_2nd, -1, 1, 0), unit_LC);
    add_table_value(FPSTR(SENSORS_DNMS), FPSTR(INTL_LC_MIN_2nd), check_display_value(last_value_dnms_lc_min_2nd, -1, 1, 0), unit_LC);
    add_table_value(FPSTR(SENSORS_DNMS), FPSTR(INTL_LC_MAX_2nd), check_display_value(last_value_dnms_lc_max_2nd, -1, 1, 0), unit_LC);
    page_content += FPSTR(EMPTY_ROW);
  }
  if (cfg::dnms_2nd_read_spectrum_active) {
    for (unsigned i = 0; i < 31; i++) {
      add_table_value(FPSTR(SENSORS_DNMS), FPSTR(WEB_LAeq_HZ_2_2nd[i]), check_display_value(last_value_dnms_laeq_freq_spec_2nd[i], -1, 1, 0), unit_LA);
    }
    page_content += FPSTR(EMPTY_ROW);
    flush_page();
  }
  if (cfg::dnms_2nd_read_spectrum_Z_active) {
    for (unsigned i = 0; i < 31; i++) {
      add_table_value(FPSTR(SENSORS_DNMS), FPSTR(WEB_LZeq_HZ_2_2nd[i]), check_display_value(last_value_dnms_lzeq_freq_spec_2nd[i], -1, 1, 0), unit_LZ);
    }
    page_content += FPSTR(EMPTY_ROW);
    flush_page();
  }
  if (cfg::dnms_2nd_read_spectrum_C_active) {
    for (unsigned i = 0; i < 31; i++) {
      add_table_value(FPSTR(SENSORS_DNMS), FPSTR(WEB_LCeq_HZ_2_2nd[i]), check_display_value(last_value_dnms_lceq_freq_spec_2nd[i], -1, 1, 0), unit_LC);
    }
    page_content += FPSTR(EMPTY_ROW);
    flush_page();
  }

  if (cfg::gps_read) {
    add_table_value(FPSTR(WEB_GPS), FPSTR(INTL_LATITUDE), check_display_value(last_value_GPS_lat, -200.0, 6, 0), unit_Deg);
    add_table_value(FPSTR(WEB_GPS), FPSTR(INTL_LONGITUDE), check_display_value(last_value_GPS_lon, -200.0, 6, 0), unit_Deg);
    add_table_value(FPSTR(WEB_GPS), FPSTR(INTL_ALTITUDE), check_display_value(last_value_GPS_alt, -1000.0, 2, 0), "m");
    add_table_value(FPSTR(WEB_GPS), FPSTR(INTL_TIME_UTC), last_value_GPS_timestamp, emptyString);
    page_content += FPSTR(EMPTY_ROW);
  }

  flush_page();

  add_table_value(F("WiFi"), FPSTR(INTL_SIGNAL_STRENGTH), String(last_signal_strength), "dBm");
  add_table_value(F("WiFi"), FPSTR(INTL_SIGNAL_QUALITY), String(signal_quality), "%");

  page_content += FPSTR(TABLE_TAG_CLOSE_BR);
  page_content += FPSTR(BR_TAG);
  end_html_page(page_content);
}
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
void loop(void) {
  bool something_to_send;
  unsigned long sleep = SLEEPTIME_MS;
  String result_PPD, result_SDS, result_PMS, result_HPM, result_NPM, result_IPS;
  String result_GPS, result_DNMS;

  unsigned sum_send_time = 0;

  act_micro = micros();
  act_milli = millis();
  send_now = msSince(starttime) >= cfg::sending_intervall_ms;

  if (send_now) {
    sleep = 0;
  }

  if (msSince(led_timer) > led_status_period_1) {
    led_timer = millis();
    if (led_status_state) {
      digitalWrite(led_status, HIGH);  // turn the LED off (HIGH is the voltage level)
      led_status_state = false;
    } else {
      digitalWrite(led_status, LOW);  // turn the LED on (LOW is the voltage level)
      led_status_state = true;
    }
    // should DIN01 be sampled?
    if (cfg::dnms_read_din01 && (din01_state == 0)) {
      din01_state = digitalRead(cfg::dnms_din01_pin);
    }
  }

  // Wait at least 30s for each NTP server to sync
  if (!sntp_time_set && send_now && msSince(time_point_device_start_ms) < 1000 * 2 * 30 + 5000) {
    debug_outln_error(F("NTP sync not finished yet, skipping send"));
    send_now = false;
    starttime = act_milli;
  }

  sample_count++;
  if (last_micro != 0) {
    unsigned long diff_micro = act_micro - last_micro;
    UPDATE_MIN_MAX(min_micro, max_micro, diff_micro);
  }
  last_micro = act_micro;

  if (cfg::sps30_read && (!sps30_init_failed)) {
    if ((msSince(starttime) - SPS30_read_timer) > SPS30_WAITING_AFTER_LAST_READ) {
      struct sps30_measurement sps30_values;
      int16_t ret_SPS30;

      SPS30_read_timer = msSince(starttime);

      ret_SPS30 = sps30_read_measurement(&sps30_values);
      ++SPS30_read_counter;
      if (ret_SPS30 < 0) {
        debug_outln_error(F("SPS30 error reading measurement"));
        SPS30_read_error_counter++;
      } else {
        if (SPS_IS_ERR_STATE(ret_SPS30)) {
          debug_outln_error(F("SPS30 measurements may not be accurate"));
          SPS30_read_error_counter++;
        }
        value_SPS30_P0 += sps30_values.mc_1p0;
        value_SPS30_P2 += sps30_values.mc_2p5;
        value_SPS30_P4 += sps30_values.mc_4p0;
        value_SPS30_P1 += sps30_values.mc_10p0;
        value_SPS30_N05 += sps30_values.nc_0p5;
        value_SPS30_N1 += sps30_values.nc_1p0;
        value_SPS30_N25 += sps30_values.nc_2p5;
        value_SPS30_N4 += sps30_values.nc_4p0;
        value_SPS30_N10 += sps30_values.nc_10p0;
        value_SPS30_TS += sps30_values.tps;
        ++SPS30_measurement_count;
      }
    }
  }

  if (cfg::sen5x_read && (!sen5x_init_failed)) {
    if ((msSince(starttime) - SEN5X_read_timer) > SEN5X_WAITING_AFTER_LAST_READ) {
      uint16_t error;
      char errorMessage[256];

      float massConcentrationPm1p0;
      float massConcentrationPm2p5;
      float massConcentrationPm4p0;
      float massConcentrationPm10p0;
      float numberConcentrationPm0p5;
      float numberConcentrationPm1p0;
      float numberConcentrationPm2p5;
      float numberConcentrationPm4p0;
      float numberConcentrationPm10p0;
      float typicalParticleSize;
      float ambientHumidity;
      float ambientTemperature;
      float vocIndex;
      float noxIndex;

      SEN5X_read_timer = msSince(starttime);

      error = sen5x.readMeasuredPmValues(massConcentrationPm1p0, massConcentrationPm2p5,
                                         massConcentrationPm4p0, massConcentrationPm10p0, numberConcentrationPm0p5, numberConcentrationPm1p0,
                                         numberConcentrationPm2p5, numberConcentrationPm4p0, numberConcentrationPm10p0, typicalParticleSize);
      if (error) {
        Debug.print("Error trying to execute readMeasuredPmValues(): ");
        errorToString(error, errorMessage, 256);
        Debug.println(errorMessage);
        ++SEN5X_read_error_counter;
      } else {
        value_SEN5X_P0 += massConcentrationPm1p0;
        value_SEN5X_P1 += massConcentrationPm10p0;
        value_SEN5X_P2 += massConcentrationPm2p5;
        value_SEN5X_P4 += massConcentrationPm4p0;
        value_SEN5X_N05 += numberConcentrationPm0p5;
        value_SEN5X_N1 += numberConcentrationPm1p0;
        value_SEN5X_N25 += numberConcentrationPm2p5;
        value_SEN5X_N4 += numberConcentrationPm4p0;
        value_SEN5X_N10 += numberConcentrationPm10p0;
        value_SEN5X_TS += typicalParticleSize;
        ++SEN5X_read_counter;
        ++SEN5X_measurement_count;
      }

      error = sen5x.readMeasuredValues(massConcentrationPm1p0, massConcentrationPm2p5, massConcentrationPm4p0, massConcentrationPm10p0, ambientHumidity, ambientTemperature, vocIndex, noxIndex);

      if (error) {
        Debug.print("Error trying to execute readMeasuredValues(): ");
        errorToString(error, errorMessage, 256);
        Debug.println(errorMessage);
        ++SEN5X_read_error_counter;
      } else {
        value_SEN5X_T += ambientTemperature;
        value_SEN5X_H += ambientHumidity;
        value_SEN5X_VOC += vocIndex;
        value_SEN5X_NOX += noxIndex;
      }
    }
  }

  if (cfg::ppd_read) {
    fetchSensorPPD(result_PPD);
  }

  if (cfg::npm_read) {
    if ((msSince(starttime_NPM) > SAMPLETIME_NPM_MS) || send_now) {
      starttime_NPM = act_milli;
      fetchSensorNPM(result_NPM);
    }
  } else if (cfg::ips_read) {
    if ((msSince(starttime_IPS) > SAMPLETIME_IPS_MS) || send_now) {
      starttime_IPS = act_milli;
      fetchSensorIPS(result_IPS);
    }
  } else {
    if ((msSince(starttime_SDS) > SAMPLETIME_SDS_MS) || send_now) {
      starttime_SDS = act_milli;
      if (cfg::sds_read) {
        fetchSensorSDS(result_SDS);
      }

      if (cfg::pms_read) {
        fetchSensorPMS(result_PMS);
      }

      if (cfg::hpm_read) {
        fetchSensorHPM(result_HPM);
      }
    }
  }

  if (cfg::gps_read && !gps_init_failed) {
    // process serial GPS data..
    while (serialGPS->available() > 0) {
      gps.encode(serialGPS->read());
    }

    if ((msSince(starttime_GPS) > SAMPLETIME_GPS_MS) || send_now) {
      // getting GPS coordinates
      fetchSensorGPS(result_GPS);
      starttime_GPS = act_milli;
    }
  }

  if ((msSince(last_display_millis) > DISPLAY_UPDATE_INTERVAL_MS) && (cfg::has_display || cfg::has_sh1106 || lcd_1602 || lcd_2004)) {
    display_values();
    last_display_millis = act_milli;
  }

  process_one_tx_job();
  drain_one_tx_2nd();

  /* DNMS 2nd measurement interval ? */
  if (cfg::dnms_2nd_interval_active || cfg::dnms_2nd_interval_Z_active || cfg::dnms_2nd_interval_C_active || cfg::dnms_2nd_read_spectrum_active || cfg::dnms_2nd_read_spectrum_Z_active || cfg::dnms_2nd_read_spectrum_C_active) {
    if (sntp_time_set) {
      struct timeval _tv_2nd;
      gettimeofday(&_tv_2nd, nullptr);
      int64_t _now_ms = (int64_t)_tv_2nd.tv_sec * 1000 + _tv_2nd.tv_usec / 1000;
      send_dnms_2nd_interval = (_now_ms >= dnms_2nd_next_wall_ms);
      if (send_dnms_2nd_interval) {
        dnms_2nd_now = _tv_2nd;
        starttime_dnms = millis();
        int64_t _n = _now_ms / (int64_t)cfg::dnms_2nd_interval_time;
        dnms_2nd_next_wall_ms = (_n + 1) * (int64_t)cfg::dnms_2nd_interval_time;
      }
    } else {
      send_dnms_2nd_interval = msSince(starttime_dnms) >= cfg::dnms_2nd_interval_time;
      if (send_dnms_2nd_interval) {
        gettimeofday(&dnms_2nd_now, nullptr);
        starttime_dnms = millis();
      }
    }
    if (send_dnms_2nd_interval) {
      String data;
      data = FPSTR(data_first_part);
      RESERVE_STRING(result, MED_STR);
      fetchSensorDNMS_2nd(result);
      if (cfg::dnms_2nd_interval_active) {
        data += result;
      }
      result = emptyString;

      static bool dnms_2nd_above_threshold = false;
      if (last_value_dnms_laeq_2nd >= cfg::dnms_2nd_threshold) {
        if (!dnms_2nd_above_threshold) {
          dnms_2nd_above_threshold = true;
          if (cfg::dnms_2nd_switch_output) {
            digitalWrite(cfg::dnms_2nd_gpio_pin, HIGH);  // set output pin high on rising edge
          }
        }
        // Refresh the trailing window while above threshold so count does not drain to 0.
        // The count only drains naturally after sound drops below the hysteresis band.
        dnms_2nd_count = cfg::dnms_2nd_number_measurements;
      } else if (dnms_2nd_above_threshold && last_value_dnms_laeq_2nd < (cfg::dnms_2nd_threshold - 1.0f)) {
        dnms_2nd_above_threshold = false;
        // count now drains to 0 after the post-event trailing window
      }

      if (dnms_2nd_count > 0) {
        if (cfg::dnms_2nd_interval_Z_active) {
          fetchSensorDNMS_Z_2nd(result);
          data += result;
          result = emptyString;
        }

        if (cfg::dnms_2nd_read_spectrum_active) {
          fetchSensorDNMS_FFT_2nd(result);
          data += result;
          result = emptyString;
        }

        if (cfg::dnms_2nd_read_spectrum_Z_active) {
          fetchSensorDNMS_FFT_Z_2nd(result);
          data += result;
          result = emptyString;
        }

        if (cfg::dnms_2nd_interval_C_active) {
          fetchSensorDNMS_C_2nd(result);
          data += result;
          result = emptyString;
        }

        if (cfg::dnms_2nd_read_spectrum_C_active) {
          fetchSensorDNMS_FFT_C_2nd(result);
          data += result;
          result = emptyString;
        }
        add_Value2Json(data, F("signal"), String(last_signal_strength));
        if ((unsigned)(data.lastIndexOf(',') + 1) == data.length()) {
          data.remove(data.length() - 1);
        }

        data += "]}";
        //Debug.println(data);
        send_2nd_dnms = true;
        sendDataToOptionalApis(data);
        count_sends_2nd++;
        server.handleClient();

        dnms_2nd_count--;
        if (dnms_2nd_count == 0) {
          if (cfg::dnms_2nd_switch_output) {
            digitalWrite(cfg::dnms_2nd_gpio_pin, LOW);  // set output to low
          }
        }
      }
    }
  }

  server.handleClient();
  if (cfg::send2mqtt && mqtt_client.connected()) {
    mqtt_client.loop();
  }
  yield();

  if (send_now) {
    if (sntp_time_set) {
      struct timeval _tv_1st;
      gettimeofday(&_tv_1st, nullptr);
      int64_t _now_ms = (int64_t)_tv_1st.tv_sec * 1000 + _tv_1st.tv_usec / 1000;
      int64_t _half = (int64_t)cfg::sending_intervall_ms / 2;
      int64_t _n = (_now_ms - dnms_1st_start_ms + _half) / (int64_t)cfg::sending_intervall_ms;
      int64_t _bound_ms = dnms_1st_start_ms + _n * (int64_t)cfg::sending_intervall_ms;
      dnms_now.tv_sec  = (time_t)(_bound_ms / 1000);
      dnms_now.tv_usec = (suseconds_t)((_bound_ms % 1000) * 1000);
    } else {
      gettimeofday(&dnms_now, nullptr);
    }
    drainTxBuffer();
    something_to_send = false;
    last_signal_strength = WiFi.RSSI();
    String data;
    data = FPSTR(data_first_part);
    RESERVE_STRING(result, MED_STR);

    if (cfg::ppd_read) {
      data += result_PPD;
      sum_send_time += sendSensorCommunity(result_PPD, PPD_API_PIN, FPSTR(SENSORS_PPD42NS), "PPD_");
      something_to_send = true;
    }
    if (cfg::sds_read) {
      data += result_SDS;
      sum_send_time += sendSensorCommunity(result_SDS, SDS_API_PIN, FPSTR(SENSORS_SDS011), "SDS_");
      something_to_send = true;
    }
    if (cfg::pms_read) {
      data += result_PMS;
      sum_send_time += sendSensorCommunity(result_PMS, PMS_API_PIN, FPSTR(SENSORS_PMSx003), "PMS_");
      something_to_send = true;
    }
    if (cfg::hpm_read) {
      data += result_HPM;
      sum_send_time += sendSensorCommunity(result_HPM, HPM_API_PIN, FPSTR(SENSORS_HPM), "HPM_");
      something_to_send = true;
    }
    if (cfg::npm_read) {
      data += result_NPM;
      sum_send_time += sendSensorCommunity(result_NPM, NPM_API_PIN, FPSTR(SENSORS_NPM), "NPM_");
      something_to_send = true;
    }
    if (cfg::ips_read) {
      data += result_IPS;
      sum_send_time += sendSensorCommunity(result_IPS, IPS_API_PIN, FPSTR(SENSORS_IPS), "IPS_");
      something_to_send = true;
    }

    if (cfg::sen5x_read && (!sen5x_init_failed)) {
      fetchSensorSEN5X(result);
      data += result;
      something_to_send = true;
      if (SEN5X_type[4] == '0') {
        sum_send_time += sendSensorCommunity(result, SEN5X_API_PIN, FPSTR(SENSORS_SEN50), "SEN50_");
      }
      if (SEN5X_type[4] == '4') {
        sum_send_time += sendSensorCommunity(result, SEN5X_API_PIN, FPSTR(SENSORS_SEN54), "SEN54_");
      }
      if (SEN5X_type[4] == '5') {
        sum_send_time += sendSensorCommunity(result, SEN5X_API_PIN, FPSTR(SENSORS_SEN55), "SEN55_");
      }
      result = emptyString;
    }

    if (cfg::sps30_read && (!sps30_init_failed)) {
      fetchSensorSPS30(result);
      data += result;
      sum_send_time += sendSensorCommunity(result, SPS30_API_PIN, FPSTR(SENSORS_SPS30), "SPS30_");
      something_to_send = true;
      result = emptyString;
    }
    if (cfg::dht_read) {
      // getting temperature and humidity (optional)
      fetchSensorDHT(result);
      data += result;
      sum_send_time += sendSensorCommunity(result, DHT_API_PIN, FPSTR(SENSORS_DHT22), "DHT_");
      something_to_send = true;
      result = emptyString;
    }
    if (cfg::htu21d_read && (!htu21d_init_failed)) {
      // getting temperature and humidity (optional)
      fetchSensorHTU21D(result);
      data += result;
      sum_send_time += sendSensorCommunity(result, HTU21D_API_PIN, FPSTR(SENSORS_HTU21D), "HTU21D_");
      something_to_send = true;
      result = emptyString;
    }
    if (cfg::bmp_read && (!bmp_init_failed)) {
      // getting temperature and pressure (optional)
      fetchSensorBMP(result);
      data += result;
      sum_send_time += sendSensorCommunity(result, BMP_API_PIN, FPSTR(SENSORS_BMP180), "BMP_");
      something_to_send = true;
      result = emptyString;
    }
    if (cfg::bmx280_read && (!bmx280_init_failed)) {
      // getting temperature, humidity and pressure (optional)
      fetchSensorBMX280(result);
      something_to_send = true;
      data += result;
      if (bmx280.sensorID() == BME280_SENSOR_ID) {
        sum_send_time += sendSensorCommunity(result, BME280_API_PIN, FPSTR(SENSORS_BME280), "BME280_");
      } else {
        sum_send_time += sendSensorCommunity(result, BMP280_API_PIN, FPSTR(SENSORS_BMP280), "BMP280_");
      }
      result = emptyString;
    }
    if (cfg::sht3x_read && (!sht3x_init_failed)) {
      // getting temperature and humidity (optional)
      fetchSensorSHT3x(result);
      data += result;
      sum_send_time += sendSensorCommunity(result, SHT3X_API_PIN, FPSTR(SENSORS_SHT3X), "SHT3X_");
      something_to_send = true;
      result = emptyString;
    }
    if (cfg::scd30_read && (!scd30_init_failed)) {
      // getting temperature and humidity (optional)
      fetchSensorSCD30(result);
      data += result;
      sum_send_time += sendSensorCommunity(result, SCD30_API_PIN, FPSTR(SENSORS_SCD30), "SCD30_");
      result = emptyString;
    }
    if (cfg::scd4x_read && (!scd4x_init_failed)) {
      // getting temperature and humidity (optional)
      fetchSensorSCD4X(result);
      data += result;
      sum_send_time += sendSensorCommunity(result, SCD4X_API_PIN, FPSTR(SENSORS_SCD4X), "SCD4X_");
      something_to_send = true;
      result = emptyString;
    }
    if (cfg::ds18b20_read) {
      // getting temperature (optional)
      fetchSensorDS18B20(result);
      data += result;
      sum_send_time += sendSensorCommunity(result, DS18B20_API_PIN, FPSTR(SENSORS_DS18B20), "DS18B20_");
      something_to_send = true;
      result = emptyString;
    }
    if (cfg::dnms_read_active || cfg::dnms_read_spectrum_active || cfg::dnms_read_Z_active || cfg::dnms_read_spectrum_Z_active || cfg::dnms_read_C_active || cfg::dnms_read_spectrum_C_active) {
      // getting noise measurement values from dnms (optional)
      fetchSensorDNMS(result);
      something_to_send = true;
      if (cfg::dnms_read_active) {
        data += result;
        sum_send_time += sendSensorCommunity(result, DNMS_API_PIN, FPSTR(SENSORS_DNMS), "DNMS_");
      }
      result = emptyString;
    }
    if (cfg::dnms_read_Z_active) {
      fetchSensorDNMS_Z(result);
      data += result;
      result = emptyString;
    }
    if (cfg::dnms_read_spectrum_active) {
      fetchSensorDNMS_FFT(result);
      data += result;
      result = emptyString;
    }
    if (cfg::dnms_read_spectrum_Z_active) {
      fetchSensorDNMS_FFT_Z(result);
      data += result;
      result = emptyString;
    }
    if (cfg::dnms_read_C_active) {
      fetchSensorDNMS_C(result);
      data += result;
      result = emptyString;
    }
    if (cfg::dnms_read_spectrum_C_active) {
      fetchSensorDNMS_FFT_C(result);
      data += result;
      result = emptyString;
    }

    if (cfg::gps_read) {
      data += result_GPS;
      sum_send_time += sendSensorCommunity(result_GPS, GPS_API_PIN, F("GPS"), "GPS_");
      something_to_send = true;
      result = emptyString;
    }
    add_Value2Json(data, F("samples"), String(sample_count));
    add_Value2Json(data, F("min_micro"), String(min_micro));
    add_Value2Json(data, F("max_micro"), String(max_micro));
    add_Value2Json(data, F("interval"), String(cfg::sending_intervall_ms));
    add_Value2Json(data, F("signal"), String(last_signal_strength));

    if ((unsigned)(data.lastIndexOf(',') + 1) == data.length()) {
      data.remove(data.length() - 1);
    }
    data += "]}";

    //	Debug.println(data);   // print complete JSON string

    yield();
    if (something_to_send) {
      sum_send_time += sendDataToOptionalApis(data);
      server.handleClient();
    }

    // https://en.wikipedia.org/wiki/Moving_average#Cumulative_moving_average
    sending_time = (3 * sending_time + sum_send_time) / 4;
    if (sum_send_time > 0) {
      debug_outln_info(F("Time for Sending (ms): "), String(sending_time));
    }

    // reconnect to WiFi if disconnected
    if (WiFi.status() != WL_CONNECTED) {
      debug_outln_error(F("Connection lost, reconnecting "));
      WiFi_error_count++;
      WiFi.reconnect();
      waitForWifiToConnect(20);
    }

    // only do a restart after finishing sending
    if (msSince(time_point_device_start_ms) > DURATION_BEFORE_FORCED_RESTART_MS) {
      sensor_restart();
    }

    // cyclic restart configured??
    if (cfg::sensor_cyclic_restart) {
      if (msSince(time_point_device_start_ms) >= (cfg::sensor_cyclic_restart_time * 3600000 - 150000)) {
        sensor_restart();
      }
    }


    // time for a OTA attempt?
    if (msSince(last_update_attempt) > PAUSE_BETWEEN_UPDATE_ATTEMPTS_MS) {
      twoStageOTAUpdate();
      last_update_attempt = act_milli;
    }

    // Resetting for next sampling
    last_data_string = std::move(data);
    lowpulseoccupancyP1 = 0;
    lowpulseoccupancyP2 = 0;
    sample_count = 0;
    last_micro = 0;
    min_micro = 1000000000;
    max_micro = 0;
    sum_send_time = 0;
    // Advance by one interval rather than resetting to now, so transmission
    // time does not accumulate as drift over many cycles.
    // Fall back to millis() only if we are more than one full interval late
    // (e.g. after a long WiFi reconnect or OTA update).
    starttime += cfg::sending_intervall_ms;
    if (msSince(starttime) > cfg::sending_intervall_ms)
      starttime = millis();
    count_sends++;
  }

#if defined(ESP8266)
  MDNS.update();
  if (cfg::npm_read) {
    //		serialNPM.perform_work();
  } else {
    //		serialSDS.perform_work();
  }

#endif

  // Sleep if all of the tasks have an event in the future. The chip can then
  // enter a lower power mode.
  if (cfg::powersave) {
    unsigned long sleep_until = millis() + sleep;
    while (millis() < sleep_until) {
      server.handleClient();
      yield();
    }
  }

  if (sample_count % 500 == 0) {
    //		Serial.println(ESP.getFreeHeap(),DEC);
  }
}
