hbitter/DNMS/Firmware/NodeMCU/airrohr-DNMS-6.0-en/airrohr-firmware/airrohr-logo-common.h

//const char DNMS_INFO_LOGO_SVG[] PROGMEM = "<svg xmlns=\"http://www.w3.org/2000/svg\" width=\"100\" height=\"89\" fill=\"#fff\"><path d=\"M90.28 66.57v.1h-6.95c-2.04 0-3.7-1.66-3.7-3.7a3.7 3.7 0 0 1 3.7-3.7h5.56a3.72 3.72 0 0 0 3.7-3.7c0-2.06-1.67-3.72-3.7-3.72a3.73 3.73 0 0 1-3.72-3.7 3.7 3.7 0 0 1 3.7-3.7 3.74 3.74 0 0 1 .75.07c5.8.4 10.37 5.15 10.37 11.04 0 5.66-4.24 10.32-9.72 11zm-19.9-22.13a3.7 3.7 0 0 1-3.7-3.7c0-2.04 1.66-3.7 3.7-3.7a3.74 3.74 0 0 1 .75.07c5.78.4 10.36 5.17 10.36 11.05 0 5.66-4.24 10.33-9.72 11v.1H29.63c-2.04 0-3.7 1.67-3.7 3.7 0 2.06 1.65 3.72 3.7 3.72h42.14v.1a11.09 11.09 0 0 1 9.7 11c0 5.9-4.57 10.65-10.35 11.05-.25.04-.5.07-.75.07-2.04 0-3.7-1.67-3.7-3.7a3.71 3.71 0 0 1 3.7-3.72c2.04 0 3.7-1.66 3.7-3.7a3.7 3.7 0 0 0-3.7-3.7H28.23v-.1c-5.47-.7-9.7-5.35-9.7-11.02 0-1.95.53-3.76 1.42-5.35C8.35 53.6 0 42.6 0 29.64 0 13.27 13.27 0 29.63 0c11.12 0 20.8 6.13 25.86 15.2 1.22-.22 2.47-.38 3.76-.38 10.92 0 19.98 7.88 21.85 18.26-2.57-1.84-5.64-3.05-8.97-3.36-2.55-4.48-7.35-7.5-12.87-7.5-2.96 0-5.7.9-8.03 2.4-2.28-9.85-11.06-17.2-21.6-17.2C17.36 7.4 7.4 17.35 7.4 29.6c0 12.28 9.96 22.23 22.23 22.23h40.74c2.04 0 3.7-1.66 3.7-3.7a3.69 3.69 0 0 0-3.7-3.7z\"/></svg>";

constexpr const unsigned int DNMS_INFO_LOGO_PNG_SIZE = 1397;

const uint8_t DNMS_INFO_LOGO_PNG[] PROGMEM = {
  0x89, 0x50, 0x4e, 0x47, 0x0d, 0x0a, 0x1a, 0x0a, 0x00, 0x00, 0x00, 0x0d, 0x49, 0x48, 0x44, 0x52,
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
  0x25, 0xce, 0x3f, 0x6d, 0x0e, 0xe9, 0xab, 0x0d, 0x57, 0xad, 0x58, 0x1d, 0x34, 0xaf, 0xb1, 0x41,
  0x9a, 0xd9, 0x49, 0xe1, 0x28, 0x0b, 0x36, 0x69, 0xbb, 0x42, 0xec, 0xf1, 0xaf, 0xfe, 0xe0, 0x37,
  0x7c, 0x54, 0x0b, 0x30, 0xff, 0x3b, 0x42, 0x15, 0x00, 0x00, 0x00, 0x00, 0x49, 0x45, 0x4e, 0x44,
  0xae, 0x42, 0x60, 0x82,
};
