hbitter/DNMS/Firmware/NodeMCU/airrohr-DNMS-6.0-en/airrohr-firmware/intl_bg.h

/*
 *	airRohr firmware
 *	Copyright (C) 2016-2018 Code for Stuttgart a.o.
 *
 *  Bulgarian translations
 *
 *	Texts should be as short as possible
 */

#define INTL_LANG "BG"
#define INTL_PM_SENSOR "Сензор за прахови частици"
const char INTL_CONFIGURATION[] PROGMEM = "Конфигурация";
#define INTL_WIFI_SETTINGS "Настройки за WiFi"
#define INTL_WIFI_NETWORKS "Зареждането WiFi мрежи ..."
#define INTL_LANGUAGE "Език"
const char INTL_NO_NETWORKS[] PROGMEM =  "Няма намерени мрежи";
const char INTL_NETWORKS_FOUND[] PROGMEM = "Намерени мрежи: ";
const char INTL_AB_HIER_NUR_ANDERN[] PROGMEM = "Разширени настройки (само ако знаете какво правите)";
const char INTL_SAVE[] PROGMEM = "Запиши";
const char INTL_SENSORS[] PROGMEM = "Сензори";
const char INTL_MORE_SENSORS[] PROGMEM = "Още Сензори";
const char INTL_SDS011[] PROGMEM = "SDS011 ({pm})";
const char INTL_PMS[] PROGMEM = "Plantower PMS(1,3,5,6,7)003 ({pm})";
const char INTL_HPM[] PROGMEM = "Honeywell сензора за прахови частици";
const char INTL_NPM[] PROGMEM = "Tera Sensor Next PM ({pm})";
const char INTL_NPM_FULLTIME[] PROGMEM = "Next PM fulltime";
const char INTL_SPS30[] PROGMEM = "Sensirion SPS30 ({pm})";
const char INTL_PPD42NS[] PROGMEM = "PPD42NS ({pm})";
const char INTL_DHT22[] PROGMEM = "DHT22 ({t}, {h})";
const char INTL_HTU21D[] PROGMEM = "HTU21D ({t}, {h})";
const char INTL_BMP180[] PROGMEM = "BMP180 ({t}, {p})";
const char INTL_BMX280[] PROGMEM = "BME280 ({t}, {h}, {p}), BMP280 ({t}, {p})";
const char INTL_DS18B20[] PROGMEM = "DS18B20 ({t})";
const char INTL_SHT3X[] PROGMEM = "SHT3X ({t}, {h})";
const char INTL_SCD30[] PROGMEM = "SCD30 ({t}, {h}, CO₂)";
const char INTL_DNMS[] PROGMEM = "DNMS ({l_a})";
const char INTL_DNMS_CORRECTION[] PROGMEM = "корекция в dB (A)";
const char INTL_TEMP_CORRECTION[] PROGMEM = "Корекция в °C";
const char INTL_HEIGHT_ABOVE_SEALEVEL[] PROGMEM = "Над морското ниво (м)";
const char INTL_PRESSURE_AT_SEALEVEL[] PROGMEM = "Налягане на морското ниво";
const char INTL_NEO6M[] PROGMEM = "GPS (NEO 6M)";
const char INTL_BASICAUTH[] PROGMEM = "Оторизация";
#define INTL_REPORT_ISSUE "Подаване на сигнал за проблем"

const char INTL_FS_WIFI_DESCRIPTION[] PROGMEM = "WiFi сензор в режим на конфигуриране";
const char INTL_FS_WIFI_NAME[] PROGMEM = "Име";
const char INTL_MORE_SETTINGS[] PROGMEM = "Още настройки";
const char INTL_AUTO_UPDATE[] PROGMEM = "Автоматична актуализация";
const char INTL_USE_BETA[] PROGMEM = "Зареждане на бета актуализация";
const char INTL_DISPLAY[] PROGMEM = "OLED SSD1306";
const char INTL_SH1106[] PROGMEM = "OLED SH1106";
const char INTL_FLIP_DISPLAY[] PROGMEM = "OLED дисплей обръщане";
const char INTL_LCD1602_27[] PROGMEM = "LCD 1602 (I2C: 0x27)";
const char INTL_LCD1602_3F[] PROGMEM = "LCD 1602 (I2C: 0x3F)";
const char INTL_LCD2004_27[] PROGMEM = "LCD 2004 (I2C: 0x27)";
const char INTL_LCD2004_3F[] PROGMEM = "LCD 2004 (I2C: 0x3F)";

#define INTL_STATIC_IP_TEXT "Конфигурация на статичен IP адрес (всички полета трябва да са попълнени)"
const char INTL_STATIC_IP[] PROGMEM = "IP адрес";
const char INTL_STATIC_SUBNET[] PROGMEM = "Subnet";
const char INTL_STATIC_GATEWAY[] PROGMEM = "Gateway";
const char INTL_STATIC_DNS[] PROGMEM = "DNS сървър";

const char INTL_DISPLAY_WIFI_INFO[] PROGMEM = "Показване на WiFi информация";
const char INTL_DISPLAY_DEVICE_INFO[] PROGMEM = "Информация за устройството на дисплея";
const char INTL_DEBUG_LEVEL[] PROGMEM = "Debug&nbsp;Level";
const char INTL_MEASUREMENT_INTERVAL[] PROGMEM = "Интервал на измерване";
const char INTL_DURATION_ROUTER_MODE[] PROGMEM = "Продължителност като рутер";
const char INTL_MORE_APIS[] PROGMEM = "Още API";
const char INTL_SEND_TO_OWN_API[] PROGMEM = "Изпращане към собствено API";
const char INTL_SERVER[] PROGMEM = "Сървър";
const char INTL_PATH[] PROGMEM = "Път";
const char INTL_PORT[] PROGMEM = "Порт";
const char INTL_USER[] PROGMEM = "Потребител";
const char INTL_PASSWORD[] PROGMEM = "Парола";
const char INTL_MEASUREMENT[] PROGMEM = "Измерване";
const char INTL_SEND_TO[] PROGMEM = "Изпрати до {v}";
const char INTL_READ_FROM[] PROGMEM = "Получено от {v}";
const char INTL_SENSOR_IS_REBOOTING[] PROGMEM = "Сензорът се рестартира.";
const char INTL_RESTART_DEVICE[] PROGMEM = "Рестартирайте устройството";
const char INTL_DELETE_CONFIG[] PROGMEM = "Изтриване на Конфигурацията";
const char INTL_RESTART_SENSOR[] PROGMEM = "Рестартиране на сензора";
#define INTL_HOME "Начало"
#define INTL_BACK_TO_HOME "Обратно към начало"
const char INTL_CURRENT_DATA[] PROGMEM = "Текущи данни";
const char INTL_DEVICE_STATUS[] PROGMEM = "Статус на устройството";
#define INTL_ACTIVE_SENSORS_MAP "Карта на активните сензори (външен линк)"
#define INTL_CONFIGURATION_DELETE "Изтриване на Конфигурацията"
#define INTL_CONFIGURATION_REALLY_DELETE "Наистина ли искате да изтриете конфигурацията?"
#define INTL_DELETE "Изтрий"
#define INTL_CANCEL "Отказ"
#define INTL_REALLY_RESTART_SENSOR "Наистина ли искате да рестартирате сензора?"
#define INTL_RESTART "Рестарт"
const char INTL_SAVE_AND_RESTART[] PROGMEM = "Запис и рестарт";
#define INTL_FIRMWARE "Софтуер версия"
const char INTL_DEBUG_SETTING_TO[] PROGMEM = "Настройки дебъгването на";
#define INTL_NONE "изключено"
#define INTL_ERROR "само грешки"
#define INTL_WARNING "предупреждения"
#define INTL_MIN_INFO "минимална информация"
#define INTL_MED_INFO "средна информация"
#define INTL_MAX_INFO "пълна информация"
#define INTL_CONFIG_DELETED "Конфигурацията е изтрита"
#define INTL_CONFIG_CAN_NOT_BE_DELETED "Конфигурацията не може да бъде изтрита"
#define INTL_CONFIG_NOT_FOUND "Конфигурацията не е открита"
const char INTL_TIME_TO_FIRST_MEASUREMENT[] PROGMEM = "Oще {v} секунди до първото измерване.";
const char INTL_TIME_SINCE_LAST_MEASUREMENT[] PROGMEM = " секунди от последното измерване.";
const char INTL_PARTICLES_PER_LITER[] PROGMEM = "частици/литър";
const char INTL_PARTICULATE_MATTER[] PROGMEM = "Прахови частици";
const char INTL_TEMPERATURE[] PROGMEM = "Температура";
const char INTL_HUMIDITY[] PROGMEM = "Влажност на въздуха";
const char INTL_PRESSURE[] PROGMEM = "Атмосферно налягане";
const char INTL_DEW_POINT[] PROGMEM = "Точка на оросяване";
const char INTL_CO2_PPM[] PROGMEM = "ppm CO₂";
const char INTL_LEQ_A[] PROGMEM = "LAeq";
const char INTL_LA_MIN[] PROGMEM = "LA min";
const char INTL_LA_MAX[] PROGMEM = "LA max";
const char INTL_LATITUDE[] PROGMEM = "Географска ширина";
const char INTL_LONGITUDE[] PROGMEM = "Географска дължина";
const char INTL_ALTITUDE[] PROGMEM = "Надморска височина";
const char INTL_TIME_UTC[] PROGMEM = "Дата (UTC)";
const char INTL_SIGNAL_STRENGTH[] PROGMEM = "Сила на сигнала";
const char INTL_SIGNAL_QUALITY[] PROGMEM = "Качество на сигнала";
#define INTL_NUMBER_OF_MEASUREMENTS "Брой измервания"
#define INTL_NUMBER_OF_MEASUREMENTS_2nd "Number of measurements (2nd interval)"
#define INTL_TIME_SENDING_MS "Време, прекарано в изпращане"
#define INTL_SENSOR "Сензор"
#define INTL_PARAMETER "Параметър"
#define INTL_VALUE "Стойност"

//const char DNMS_INFO_LOGO_SVG[] PROGMEM = "<svg xmlns=\"http://www.w3.org/2000/svg\" width=\"128\" height=\"128\" viewBox=\"0 0 128 128\"><path fill=\"#009A93\" d=\"M123.58 77.76c0-6.22-3.2-11.66-7.96-14.66 2.36-3.87 3.73-8.42 3.73-13.3 0-14.1-11.44-25.52-25.53-25.52-4 0-7.8.93-11.17 2.57C80.63 19.6 74 14.3 66.1 14.3c-7.7 0-14.22 5.07-16.4 12.07-3.05-1.2-6.4-1.87-9.88-1.87-14.94 0-27.06 12.07-27.16 27-5.43 4.47-8.9 11.3-8.9 18.95 0 13.5 10.8 24.45 24.1 24.45h79.32c9.07-.06 16.4-7.7 16.4-17.14z\"/><path fill=\"#fff\" d=\"M55.5 49.92v19.05c0 9.37-7.64 17-17.1 17-9.36 0-17-7.63-17-17 0-9.38 7.64-17.02 17-17.02h.7V56h-.7c-7.1 0-12.88 5.84-12.88 12.96 0 7.13 5.77 12.97 12.9 12.97 7.2 0 12.96-5.85 12.96-12.97V49.92c0-7.2-5.77-12.97-12.97-12.97-7.1 0-12.8 5.78-12.8 12.9v.75h-4.2v-.75c0-9.37 7.7-17.02 17-17.02 9.5 0 17.1 7.65 17.1 17.1zm-5.47 0v19.05c0 6.37-5.17 11.54-11.62 11.54-6.3 0-11.5-5.1-11.5-11.5 0-6.3 5.2-11.5 11.6-11.5h.7v4.1h-.7c-4.1 0-7.5 3.4-7.5 7.5s3.4 7.5 7.5 7.5c4.2 0 7.6-3.4 7.6-7.5V49.9c0-4.2-3.3-7.57-7.5-7.57-4.1 0-7.5 3.38-7.5 7.5v.75H27v-.75c0-6.37 5.17-11.55 11.54-11.55 6.46 0 11.63 5.18 11.63 11.62zm-5.47 0v19.05c0 3.37-2.7 6.14-6.15 6.14-3.3 0-6-2.7-6-6.1 0-3.4 2.7-6.1 6.1-6.1h.7V67h-.7c-1.1 0-2 .9-2 2.02 0 1.1.9 2 2 2 1.2 0 2.1-.9 2.1-2V49.9c0-1.2-.9-2.1-2.1-2.1-1.1 0-2 .9-2 2.03v.75h-4.1v-.75c0-3.38 2.7-6.08 6.1-6.08 3.5 0 6.2 2.7 6.2 6.15zm13.94-2.17v-15h4.05v15H58.5zm4.05 38.16H58.5V49.2h4.05v36.7zm1.42-38.1v-15h4.05v15h-4.05zm0 38.2V49.2h4.05v36.7h-4.05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
  0x57, 0x41, 0x08, 0xe0, 0x6b, 0xc7, 0x21, 0x36, 0x99, 0x2e, 0xeb, 0x52,
  0x2a, 0x19, 0xe2, 0x31, 0xc8, 0xc1, 0x7b, 0xb8, 0x5f, 0x00, 0x7c, 0x05,
  0x68, 0x6a, 0x41, 0xc0, 0x3c, 0x42, 0x01, 0x17, 0xa7, 0x70, 0x33, 0x02,
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
};
