hbitter/DNMS/Firmware/NodeMCU/airrohr-DNMS-6.0-en/airrohr-firmware/intl_cz.h

/*
 *	airRohr firmware
 *	Copyright (C) 2016-2018 Code for Stuttgart a.o.
 *
 *  Czech translations
 *
 *	Texts should be as short as possible
 */

#define INTL_LANG "CZ"
#define INTL_PM_SENSOR "Senzor prachových èástic"
const char INTL_CONFIGURATION[] PROGMEM = "Konfigurace";
#define INTL_WIFI_SETTINGS "Nastavení Wi-Fi"
#define INTL_WIFI_NETWORKS "Vyhledávání Wi-Fi sítí ..."
#define INTL_LANGUAGE "Jazyk"
const char INTL_NO_NETWORKS[] PROGMEM = "Žádné Wi-Fi sítì v dosahu.";
const char INTL_NETWORKS_FOUND[] PROGMEM = "Dostupné sítì: ";
const char INTL_AB_HIER_NUR_ANDERN[] PROGMEM = "Rozšíøené nastavení (jen pokud víte jistì, co dìláte)";
const char INTL_SAVE[] PROGMEM = "Uložit";
const char INTL_SENSORS[] PROGMEM = "Moduly (èidla)";
const char INTL_MORE_SENSORS[] PROGMEM = "More Moduly (èidla)";
const char INTL_SDS011[] PROGMEM = "SDS011 (modul {pm})";
const char INTL_PMS[] PROGMEM = "Plantower PMS(1,3,5,6,7)003 (modul {pm})";
const char INTL_HPM[] PROGMEM = "Honeywell PM ({pm})";
const char INTL_NPM[] PROGMEM = "Tera Sensor Next PM ({pm})";
const char INTL_NPM_FULLTIME[] PROGMEM = "Next PM fulltime";
const char INTL_SPS30[] PROGMEM = "Sensirion SPS30 ({pm})";
const char INTL_PPD42NS[] PROGMEM = "PPD42NS ({pm})";
const char INTL_DHT22[] PROGMEM = "DHT22 ({t}, {h})";
const char INTL_HTU21D[] PROGMEM = "HTU21D ({t}, {h})";
const char INTL_BMP180[] PROGMEM = "BMP180 ({t}, {p})";
const char INTL_BMX280[] PROGMEM = "BME280 ({t}, {h}, {p}), BMP280 ({t}, {p})";
const char INTL_SHT3X[] PROGMEM = "SHT3X ({t}, {h})";
const char INTL_SCD30[] PROGMEM = "SCD30 ({t}, {h}, CO₂)";
const char INTL_DS18B20[] PROGMEM = "DS18B20 ({t})";
const char INTL_DNMS[] PROGMEM = "DNMS ({l_a})";
const char INTL_DNMS_CORRECTION[] PROGMEM = "Korekce v dB (A)";
const char INTL_TEMP_CORRECTION[] PROGMEM = "Korekce ve °C";
const char INTL_HEIGHT_ABOVE_SEALEVEL[] PROGMEM = "";
const char INTL_PRESSURE_AT_SEALEVEL[] PROGMEM = "";
const char INTL_NEO6M[] PROGMEM = "GPS (NEO 6M)";
const char INTL_BASICAUTH[] PROGMEM = "Pøihlášení (heslem)";
#define INTL_REPORT_ISSUE "Nahlásit problém"

const char INTL_FS_WIFI_DESCRIPTION[] PROGMEM = "Wi-Fi modul v konfiguraèním módu";
const char INTL_FS_WIFI_NAME[] PROGMEM = "Název";
const char INTL_MORE_SETTINGS[] PROGMEM = "Další nastavení";
const char INTL_AUTO_UPDATE[] PROGMEM = "Autom. aktualizace";
const char INTL_USE_BETA[] PROGMEM = "Nahrát betaverzi";
const char INTL_DISPLAY[] PROGMEM = "OLED SSD1306";
const char INTL_SH1106[] PROGMEM = "OLED SH1106";
const char INTL_FLIP_DISPLAY[] PROGMEM = "OLED displej flip";
const char INTL_LCD1602_27[] PROGMEM = "LCD 1602 (I2C: 0x27)";
const char INTL_LCD1602_3F[] PROGMEM = "LCD 1602 (I2C: 0x3F)";
const char INTL_LCD2004_27[] PROGMEM = "LCD 2004 (I2C: 0x27)";
const char INTL_LCD2004_3F[] PROGMEM = "LCD 2004 (I2C: 0x3F)";
const char INTL_DISPLAY_WIFI_INFO[] PROGMEM = "Zobrazit informace o WiFi";
const char INTL_DISPLAY_DEVICE_INFO[] PROGMEM = "Zobrazit informace o zařízení";
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
